IRNAS/smartparks-lion-tracker-hardware/LION/04_OUTPUT_FILES/Lion_9.png

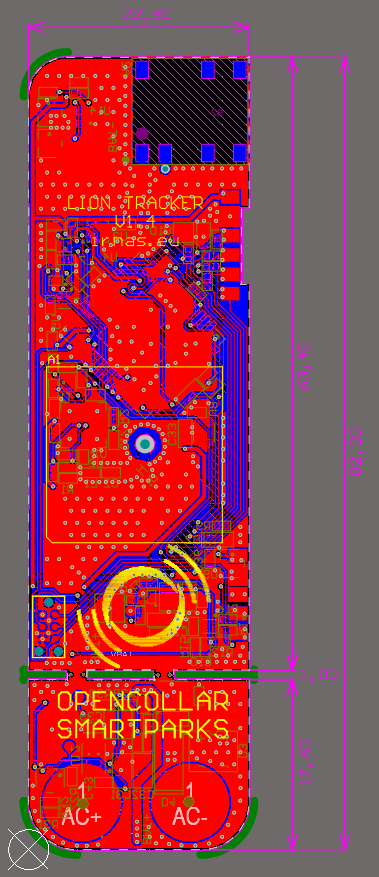
LION/04_OUTPUT_FILES/Lion_9.png
