IRNAS/smartparks-lion-tracker-hardware/Fence_monitor/06_RELEASE/V1/Fence monitor_V1_3D/Fence monitor_V1_PCB_3D_PRINT.pdf

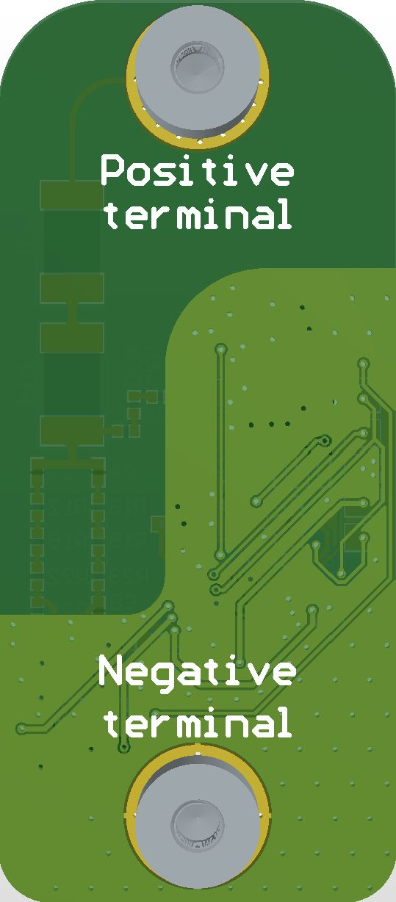
[picture p21: figure]

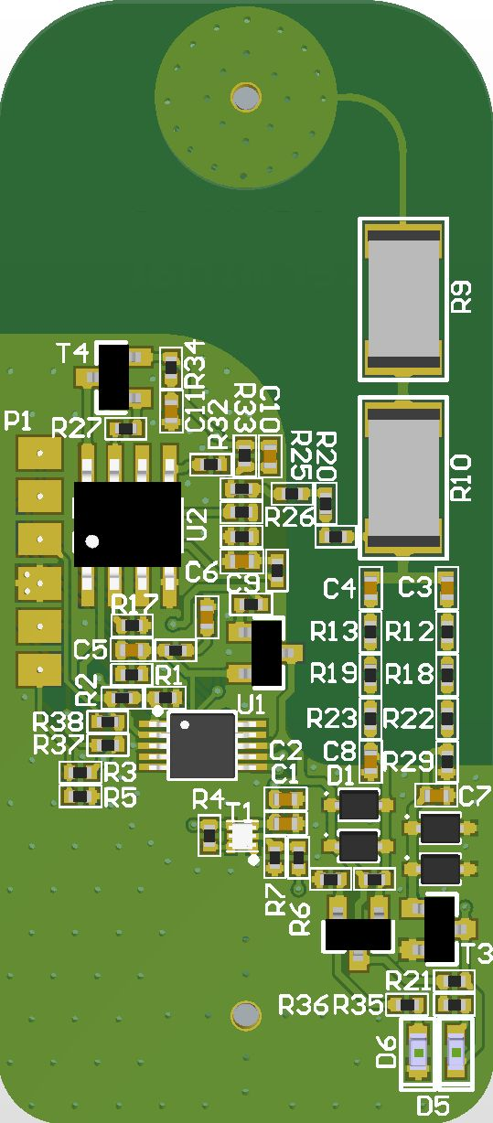
[picture p22: figure]
