IRNAS/smartparks-lion-tracker-hardware/LION/06_RELEASE/V1.4/Lion_Tracker_V1.4_3D/Lion_Tracker_V1.4_PCB 3D Print.pdf

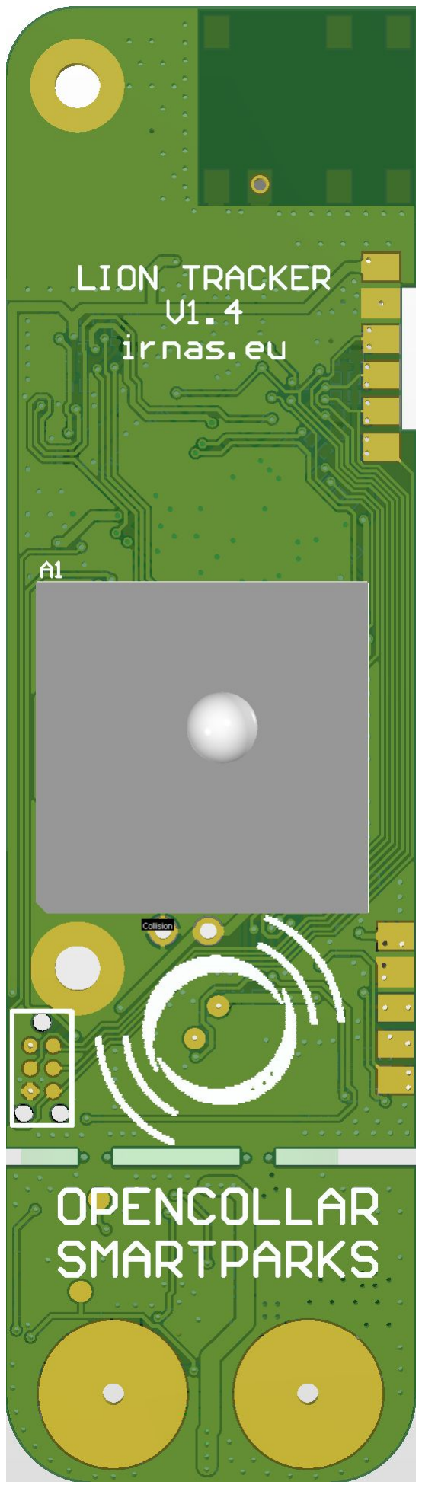
[picture p23: figure]

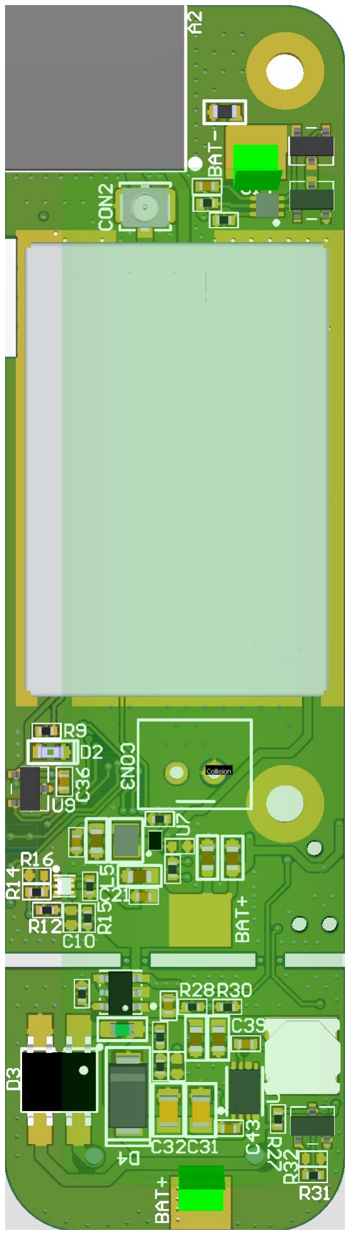
[picture p24: figure]
