IRNAS/smartparks-lion-tracker-hardware/LION/06_RELEASE/V0/Lion tracker_V0_3D/Lion tracker_V0_PCB 3D Print.pdf

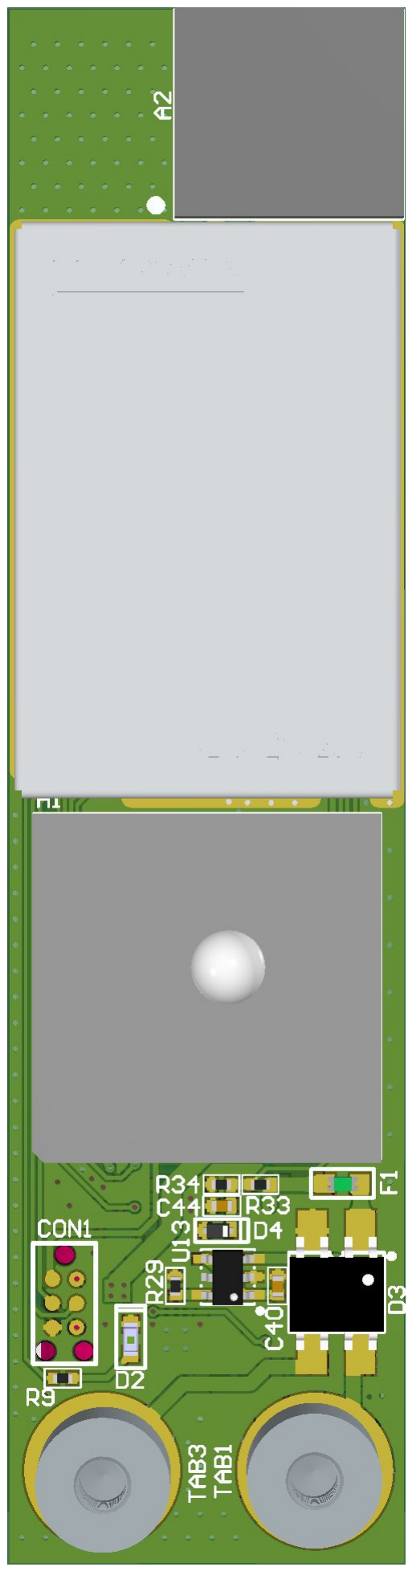
[picture p25: figure]

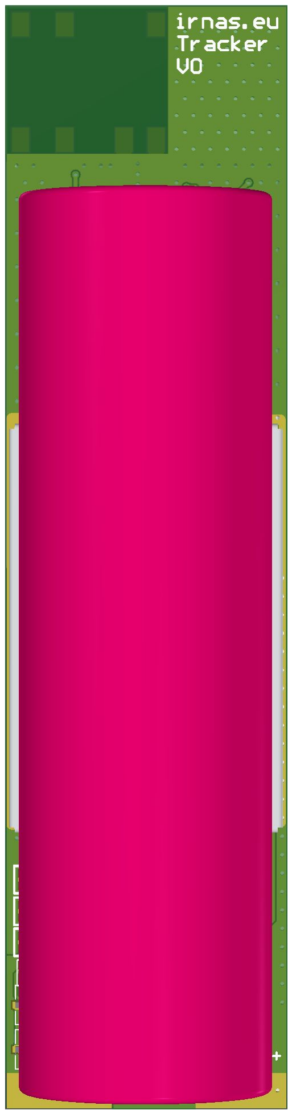
[picture p26: figure]
