IRNAS/smartparks-lion-tracker-hardware/LION/06_RELEASE/V1.1/Lion_Tracker_V1.1_3D/Lion_Tracker_V1.1_PCB 3D Print.pdf

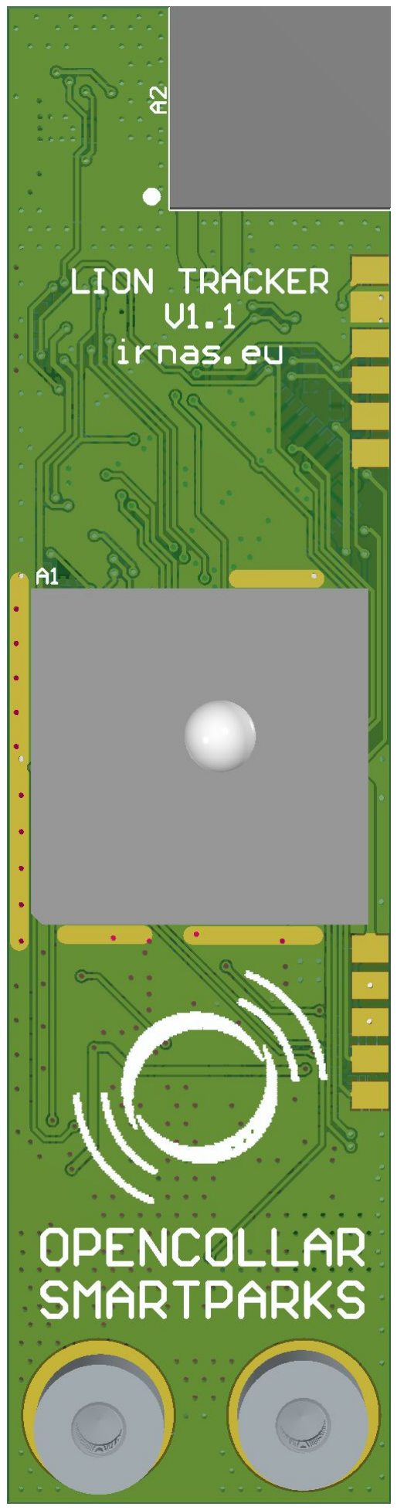
[picture p27: figure]

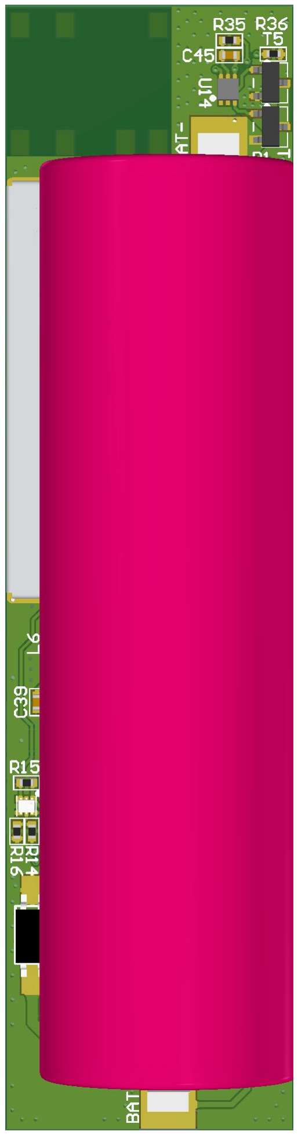
[picture p28: figure]
