IRNAS/smartparks-lion-tracker-hardware/LION/06_RELEASE/V1.2/Lion_Tracker_V1.2_3D/Lion_Tracker_V1.2_PCB 3D Print.pdf

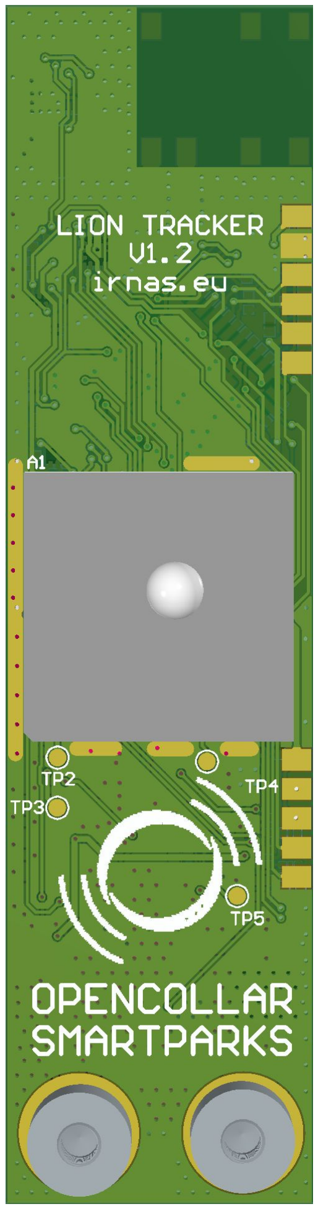
[picture p29: figure]

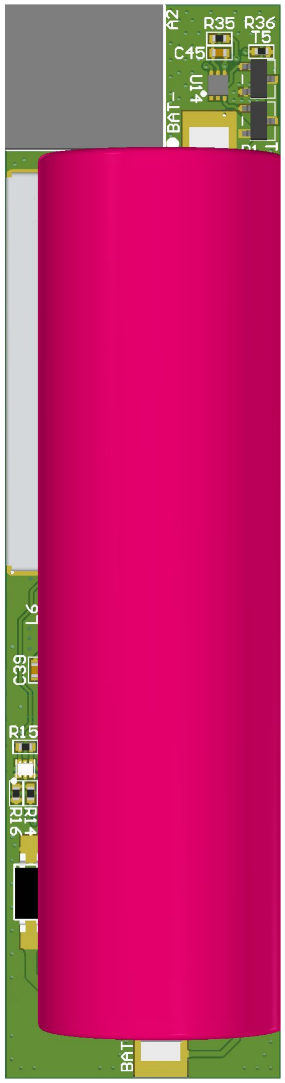
[picture p30: figure]
