IRNAS/smartparks-lion-tracker-hardware/LION/06_RELEASE/V1.3/Lion_Tracker_V1.3_3D/Lion_Tracker_V1.3_PCB 3D Print.pdf

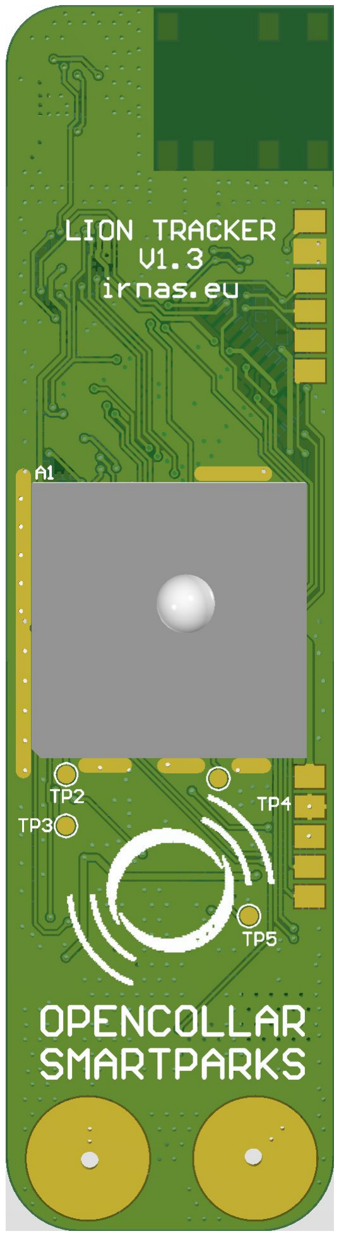
[picture p31: figure]

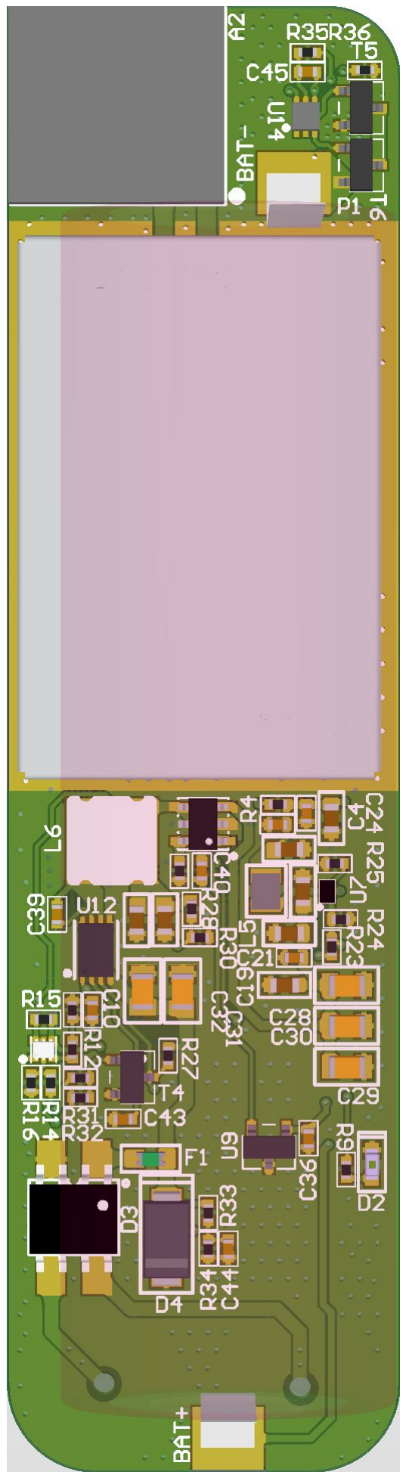
[picture p32: figure]
