IRNAS/smartparks-lion-tracker-hardware/LION/06_RELEASE/V1.4/Lion_Tracker_V1.4_SCHEMATICS/Lion_Tracker_V1.4_SCHEMATICS.PDF

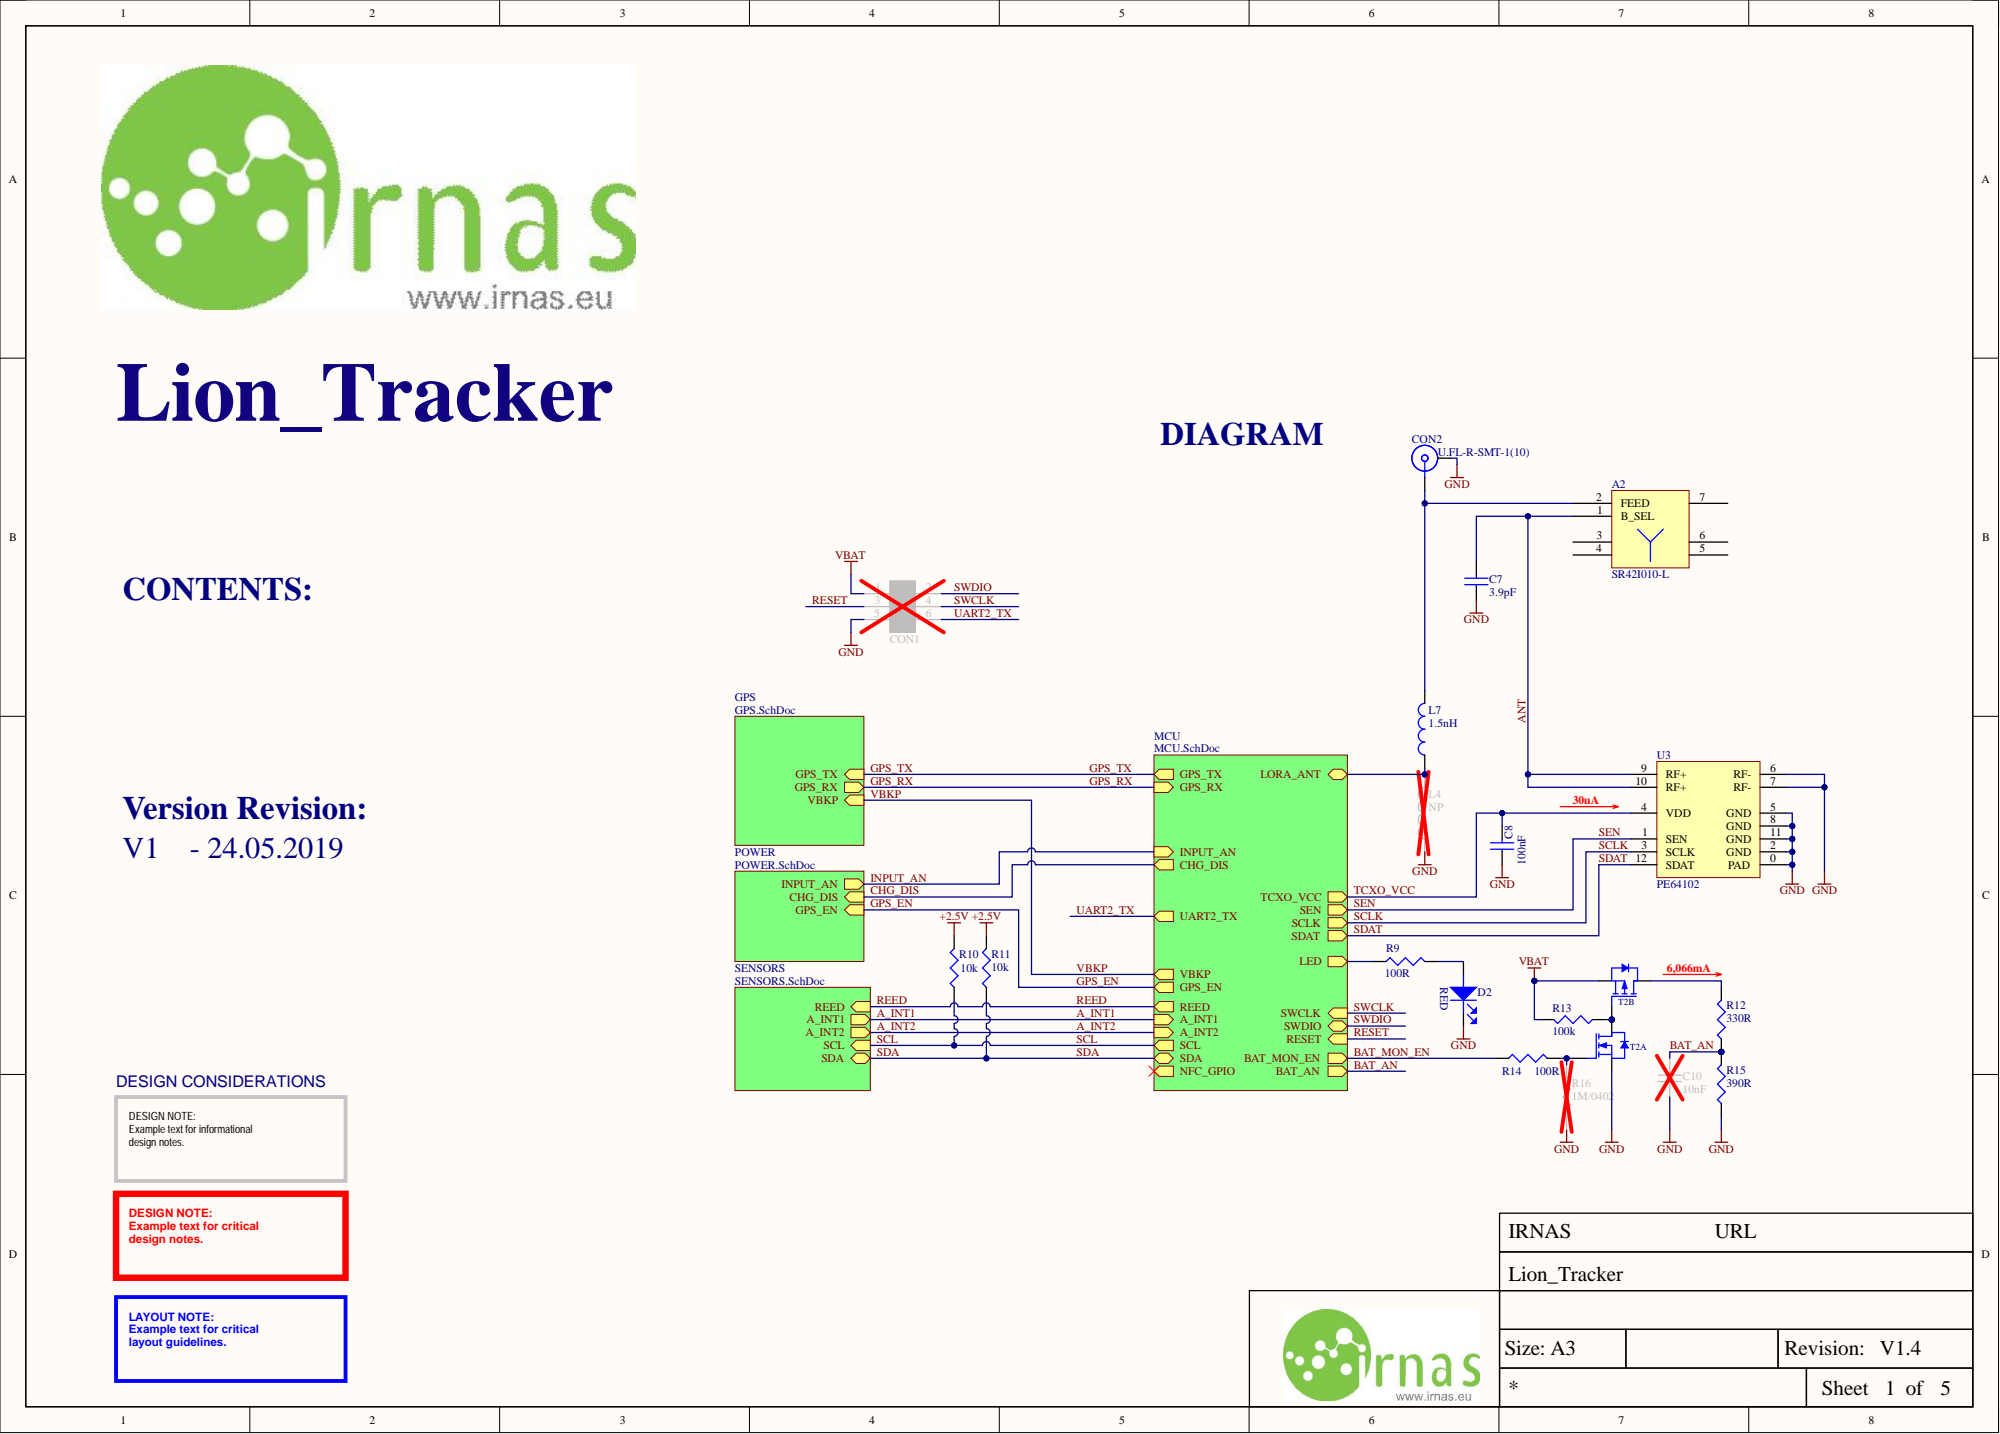
[picture p64: page 1]

B_SEL 1 FEED 2

SCLK
SDAT

GPS_EN | SEN

+2.5V +2.5V R10 R11 10k 10k VBKP | SCLK

REED A_INT1 A_INT2 SCL SDA | REED | REED

A_INT1 | A_INT1

SCL | SCL
SDA | SDA

DESIGN NOTE:
Example text for informational
design notes.

Example text for critical

LAYOUT NOTE:
layout guidelines.

Size: A3 | | Revision: V1.4

Sheet of

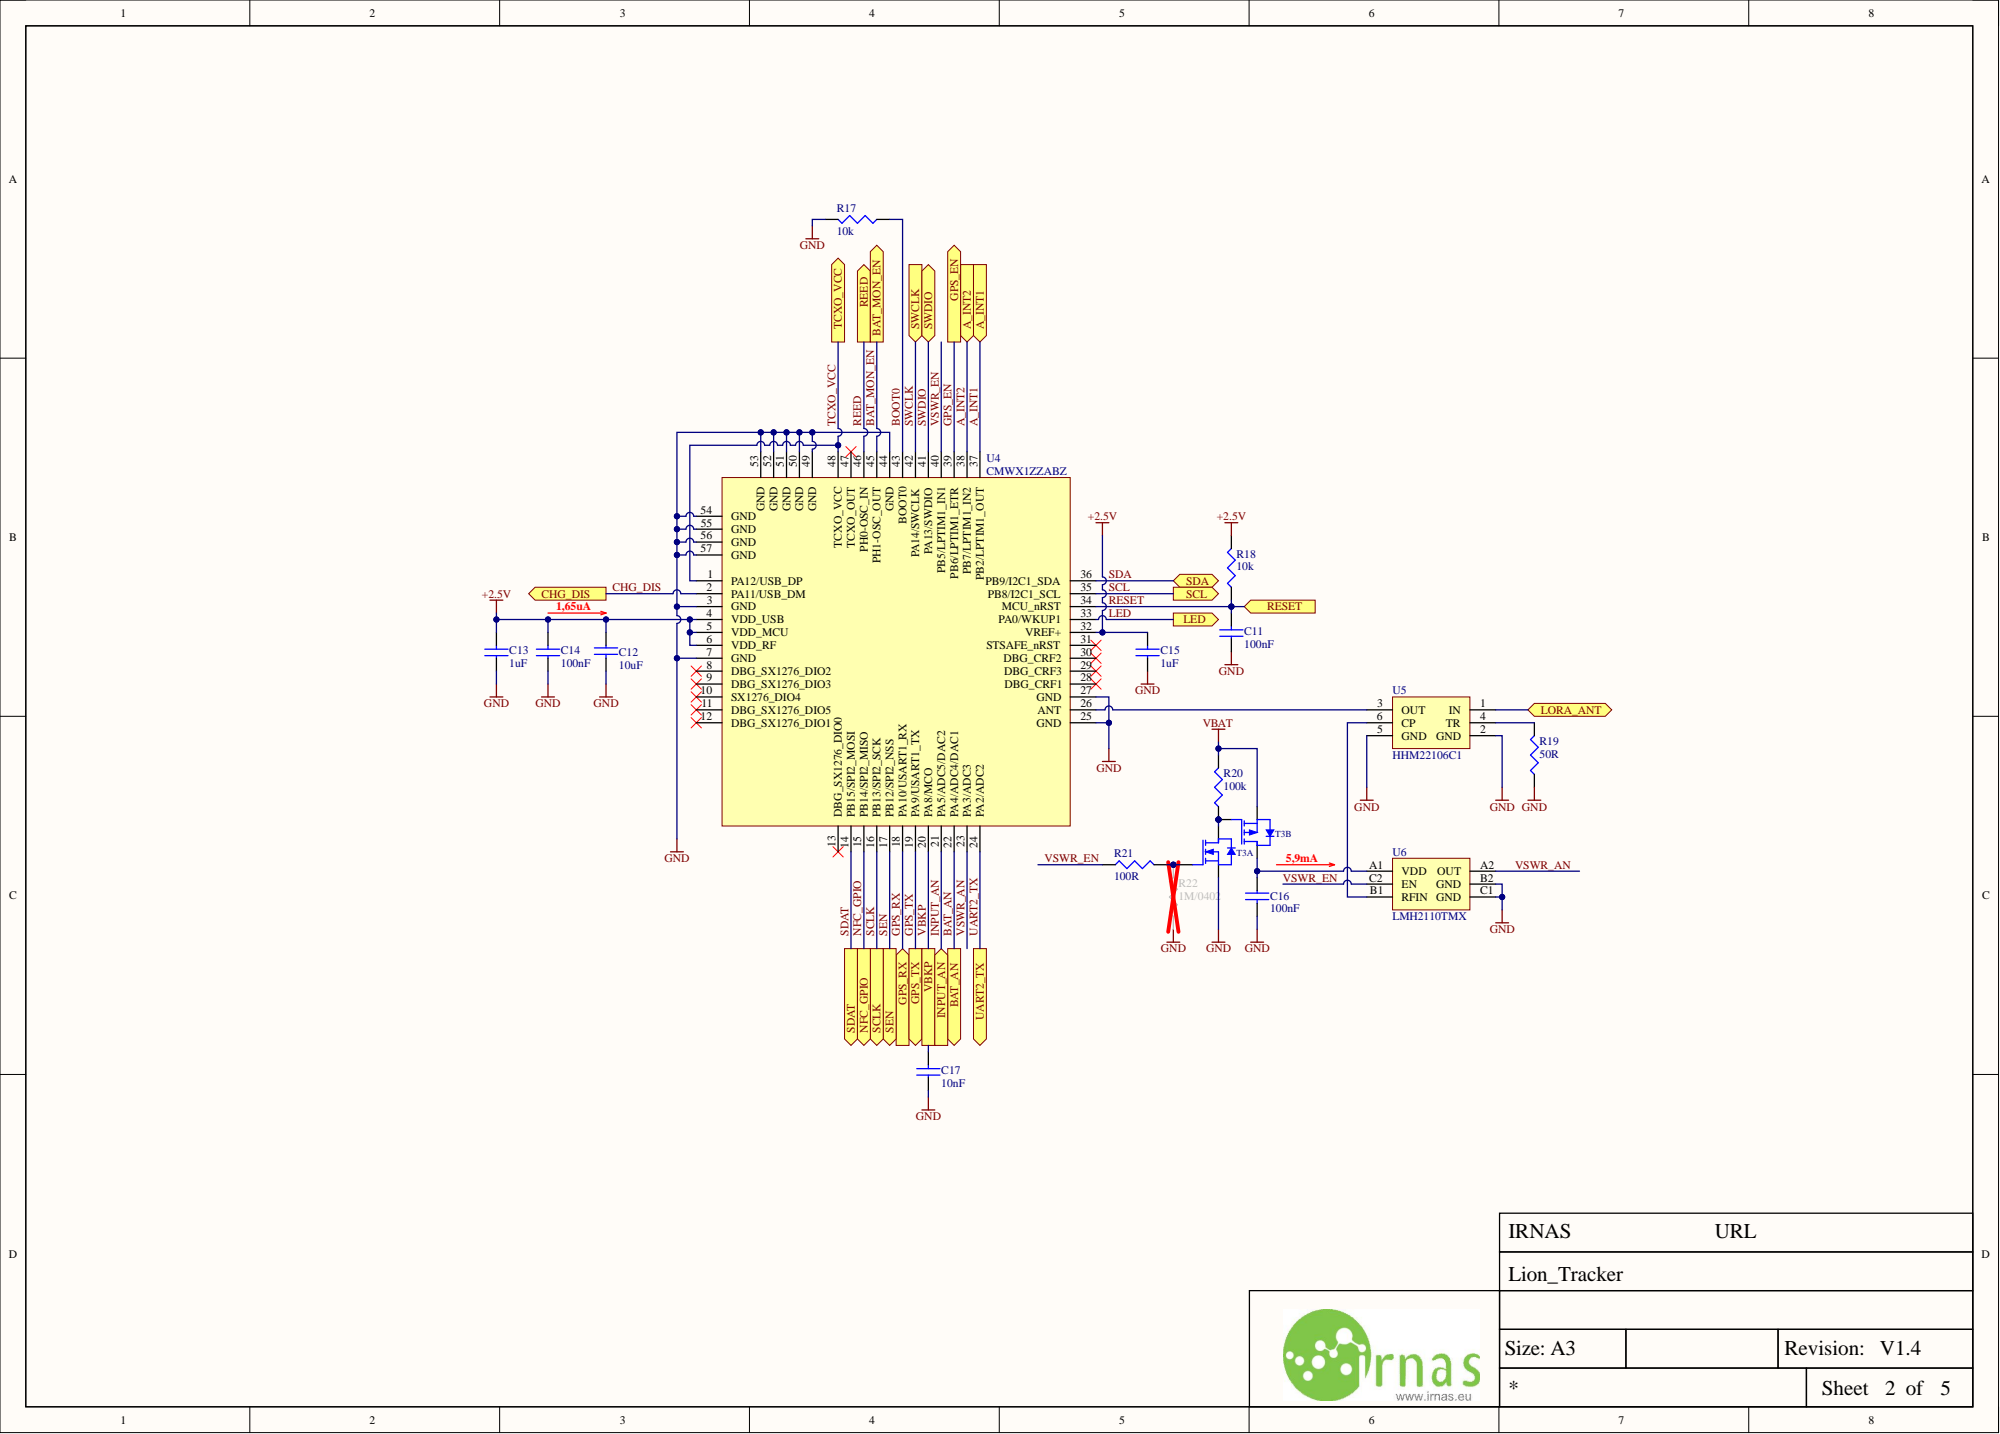
[picture p65: page 2]

GND 50 GND 51 GND 52 GND 53

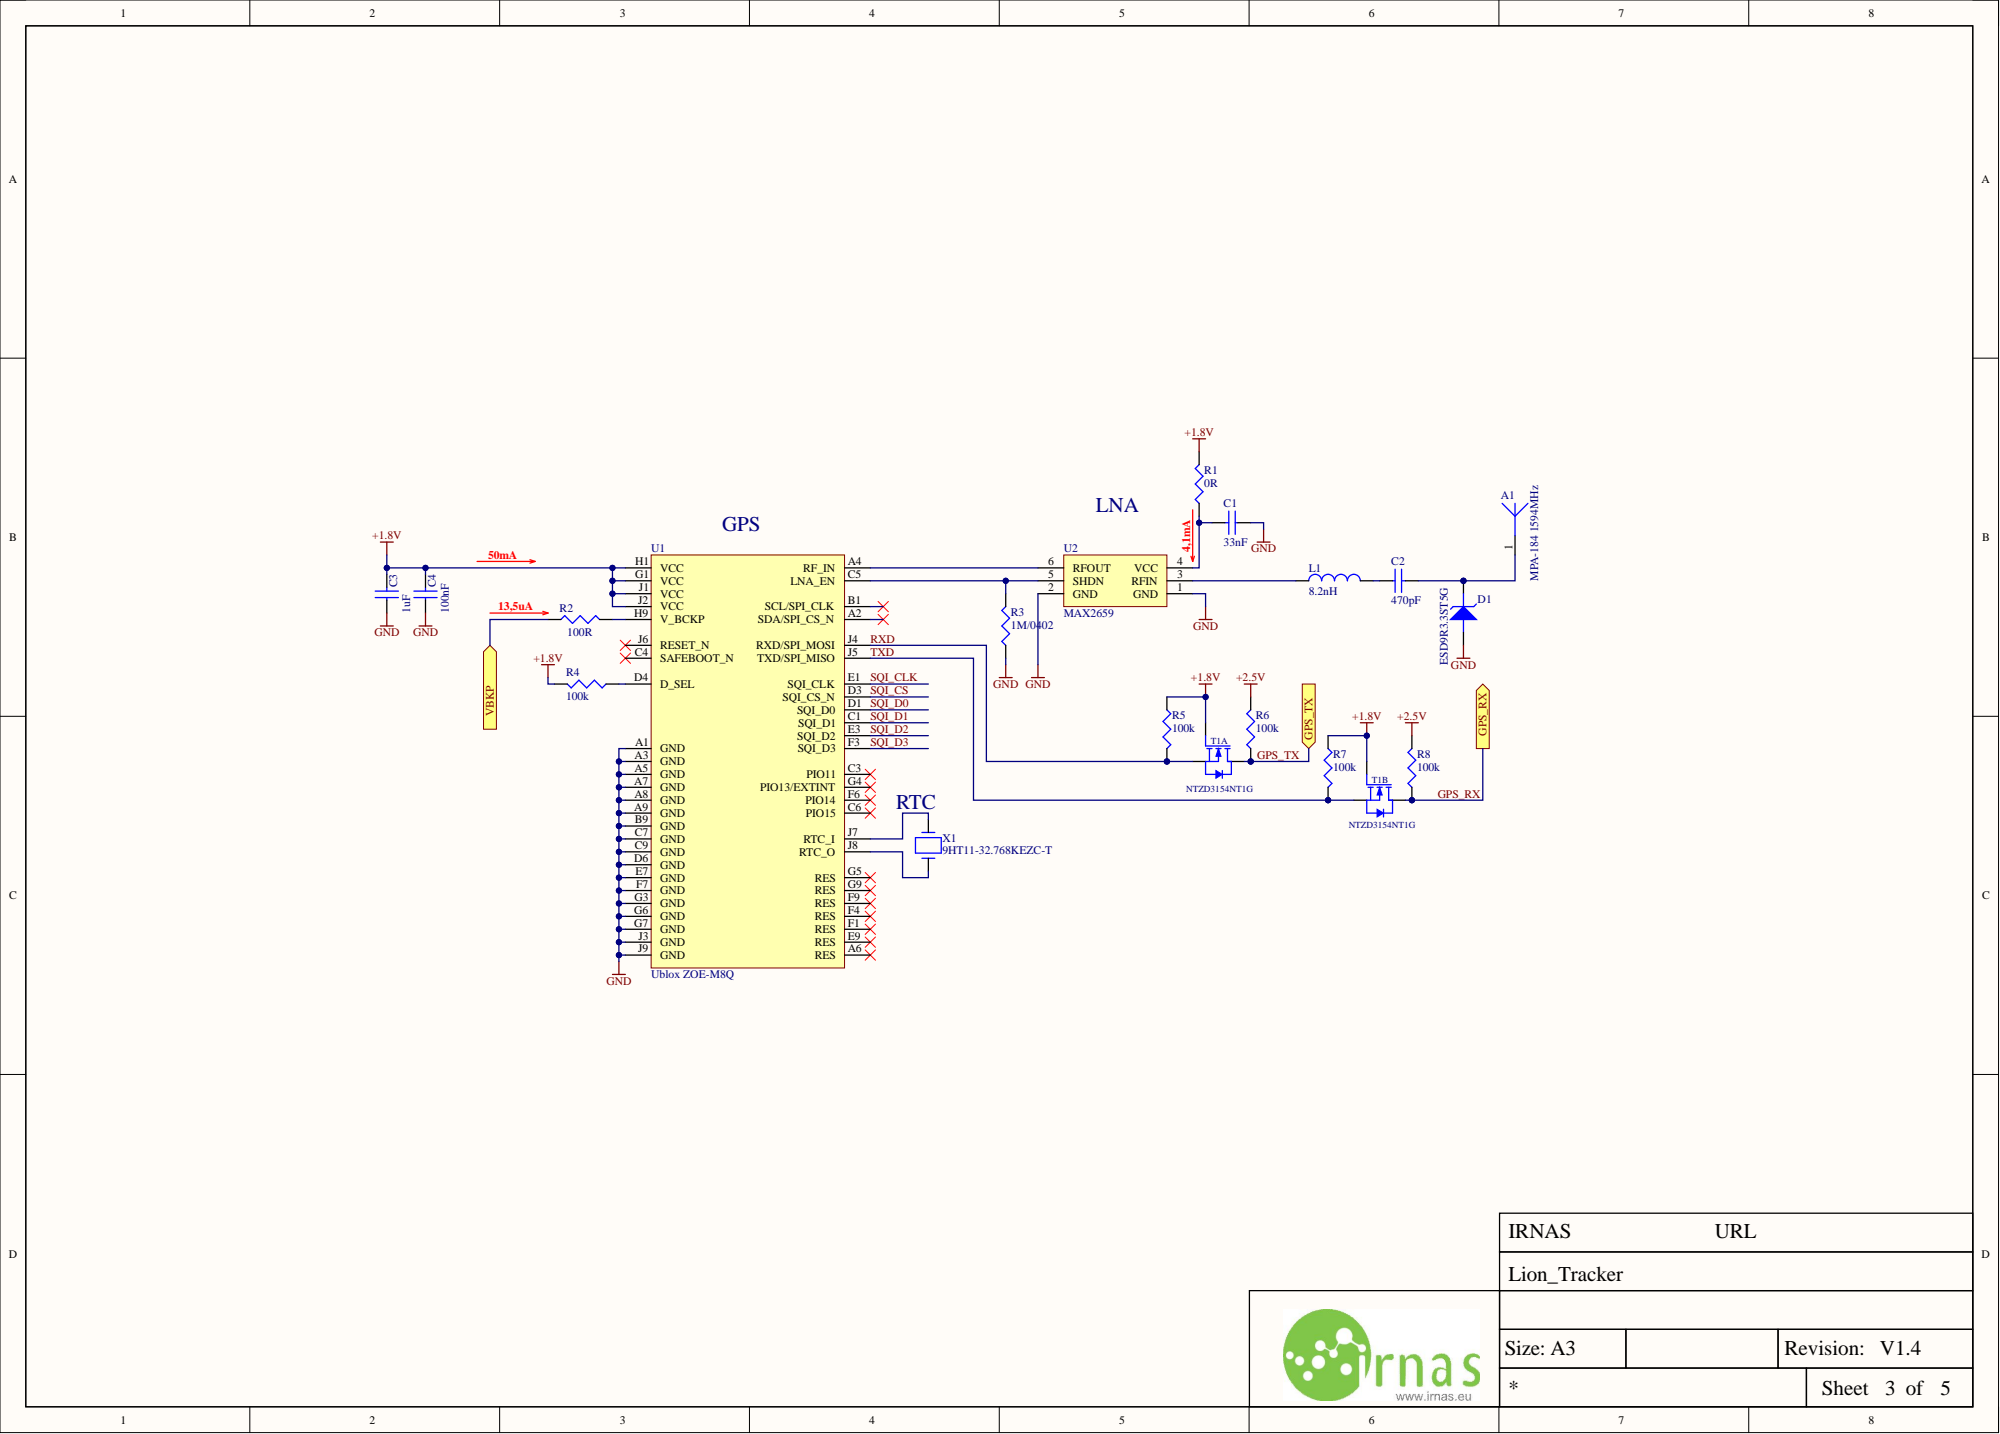
[picture p66: page 3]

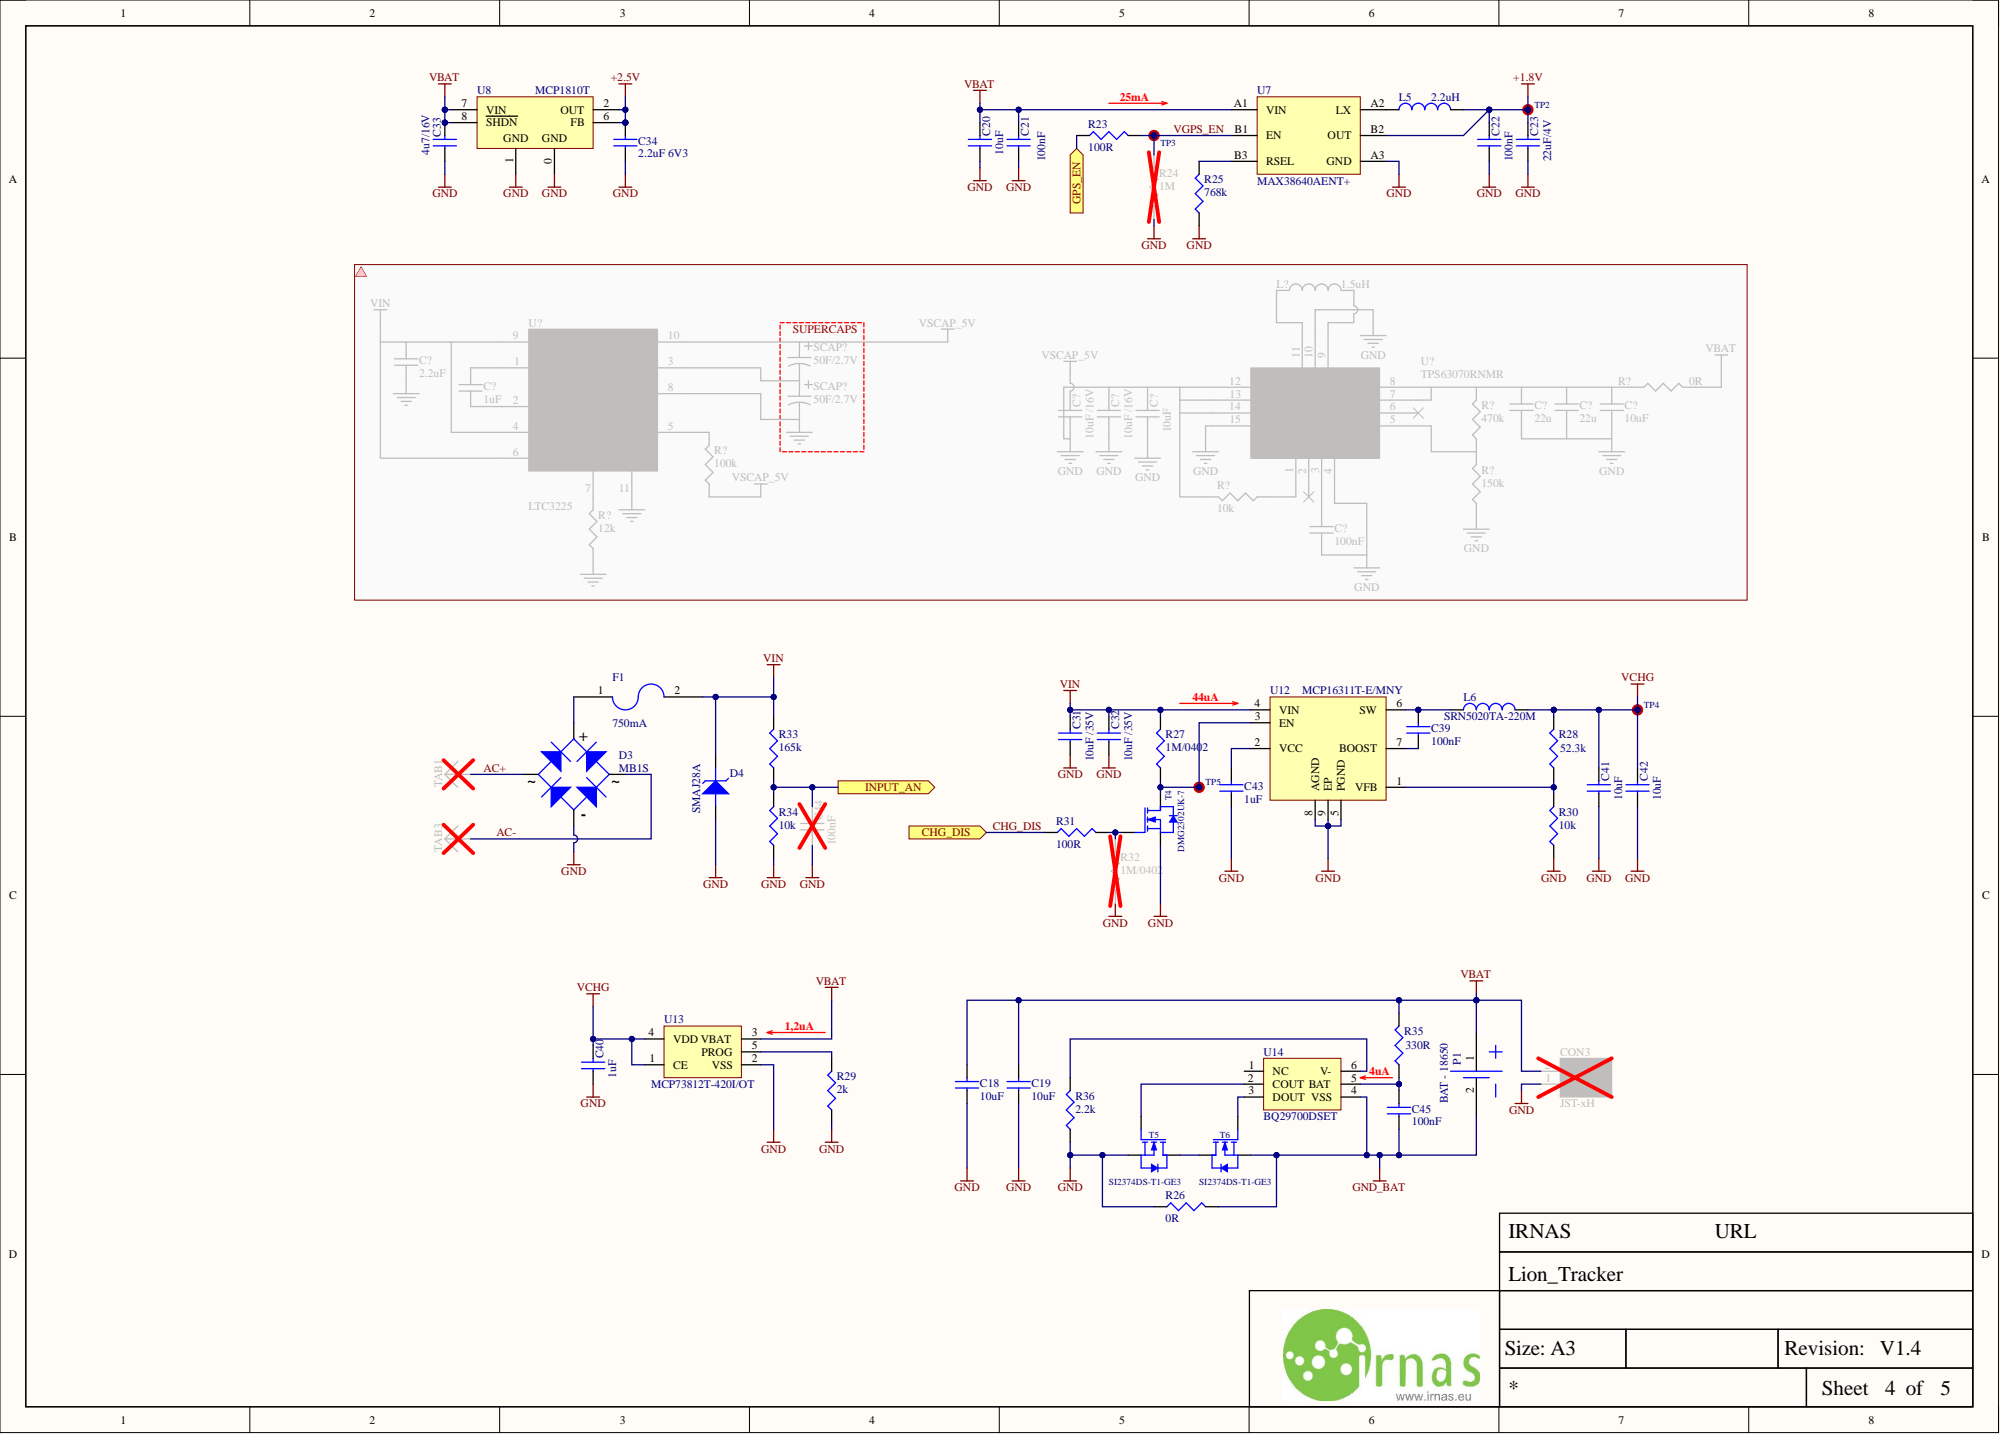
[picture p67: page 4]

VIN 13

VSEL 15

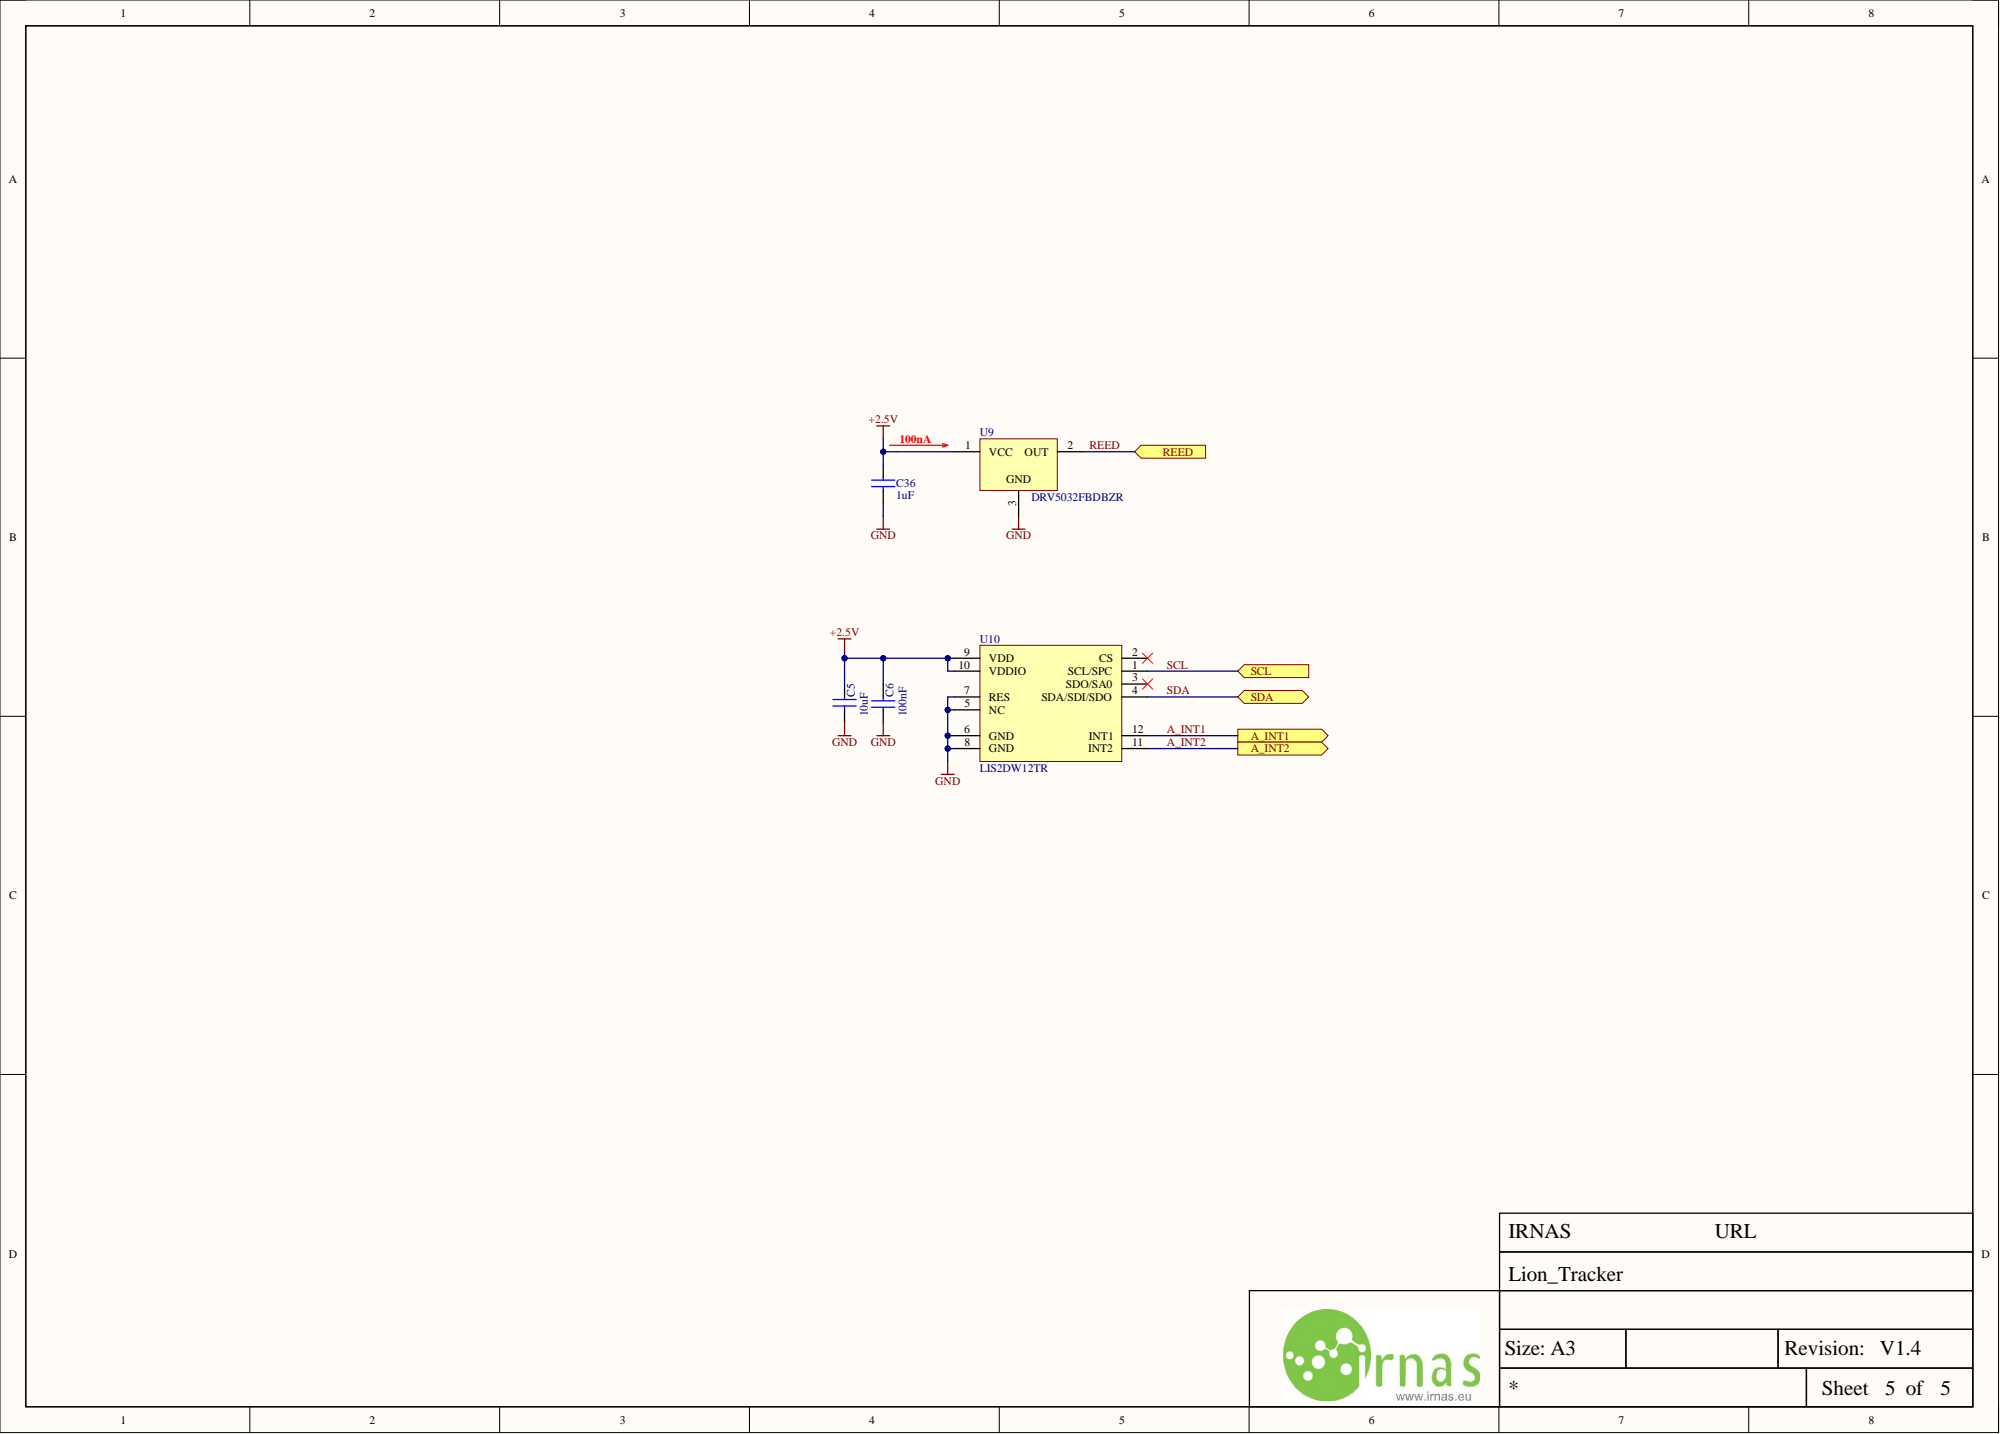
[picture p68: page 5]
