IRNAS/smartparks-lion-tracker-hardware/LION/06_RELEASE/V0/Lion tracker_V0_SCHEMATICS/Lion tracker_V0_SCHEMATICS.PDF

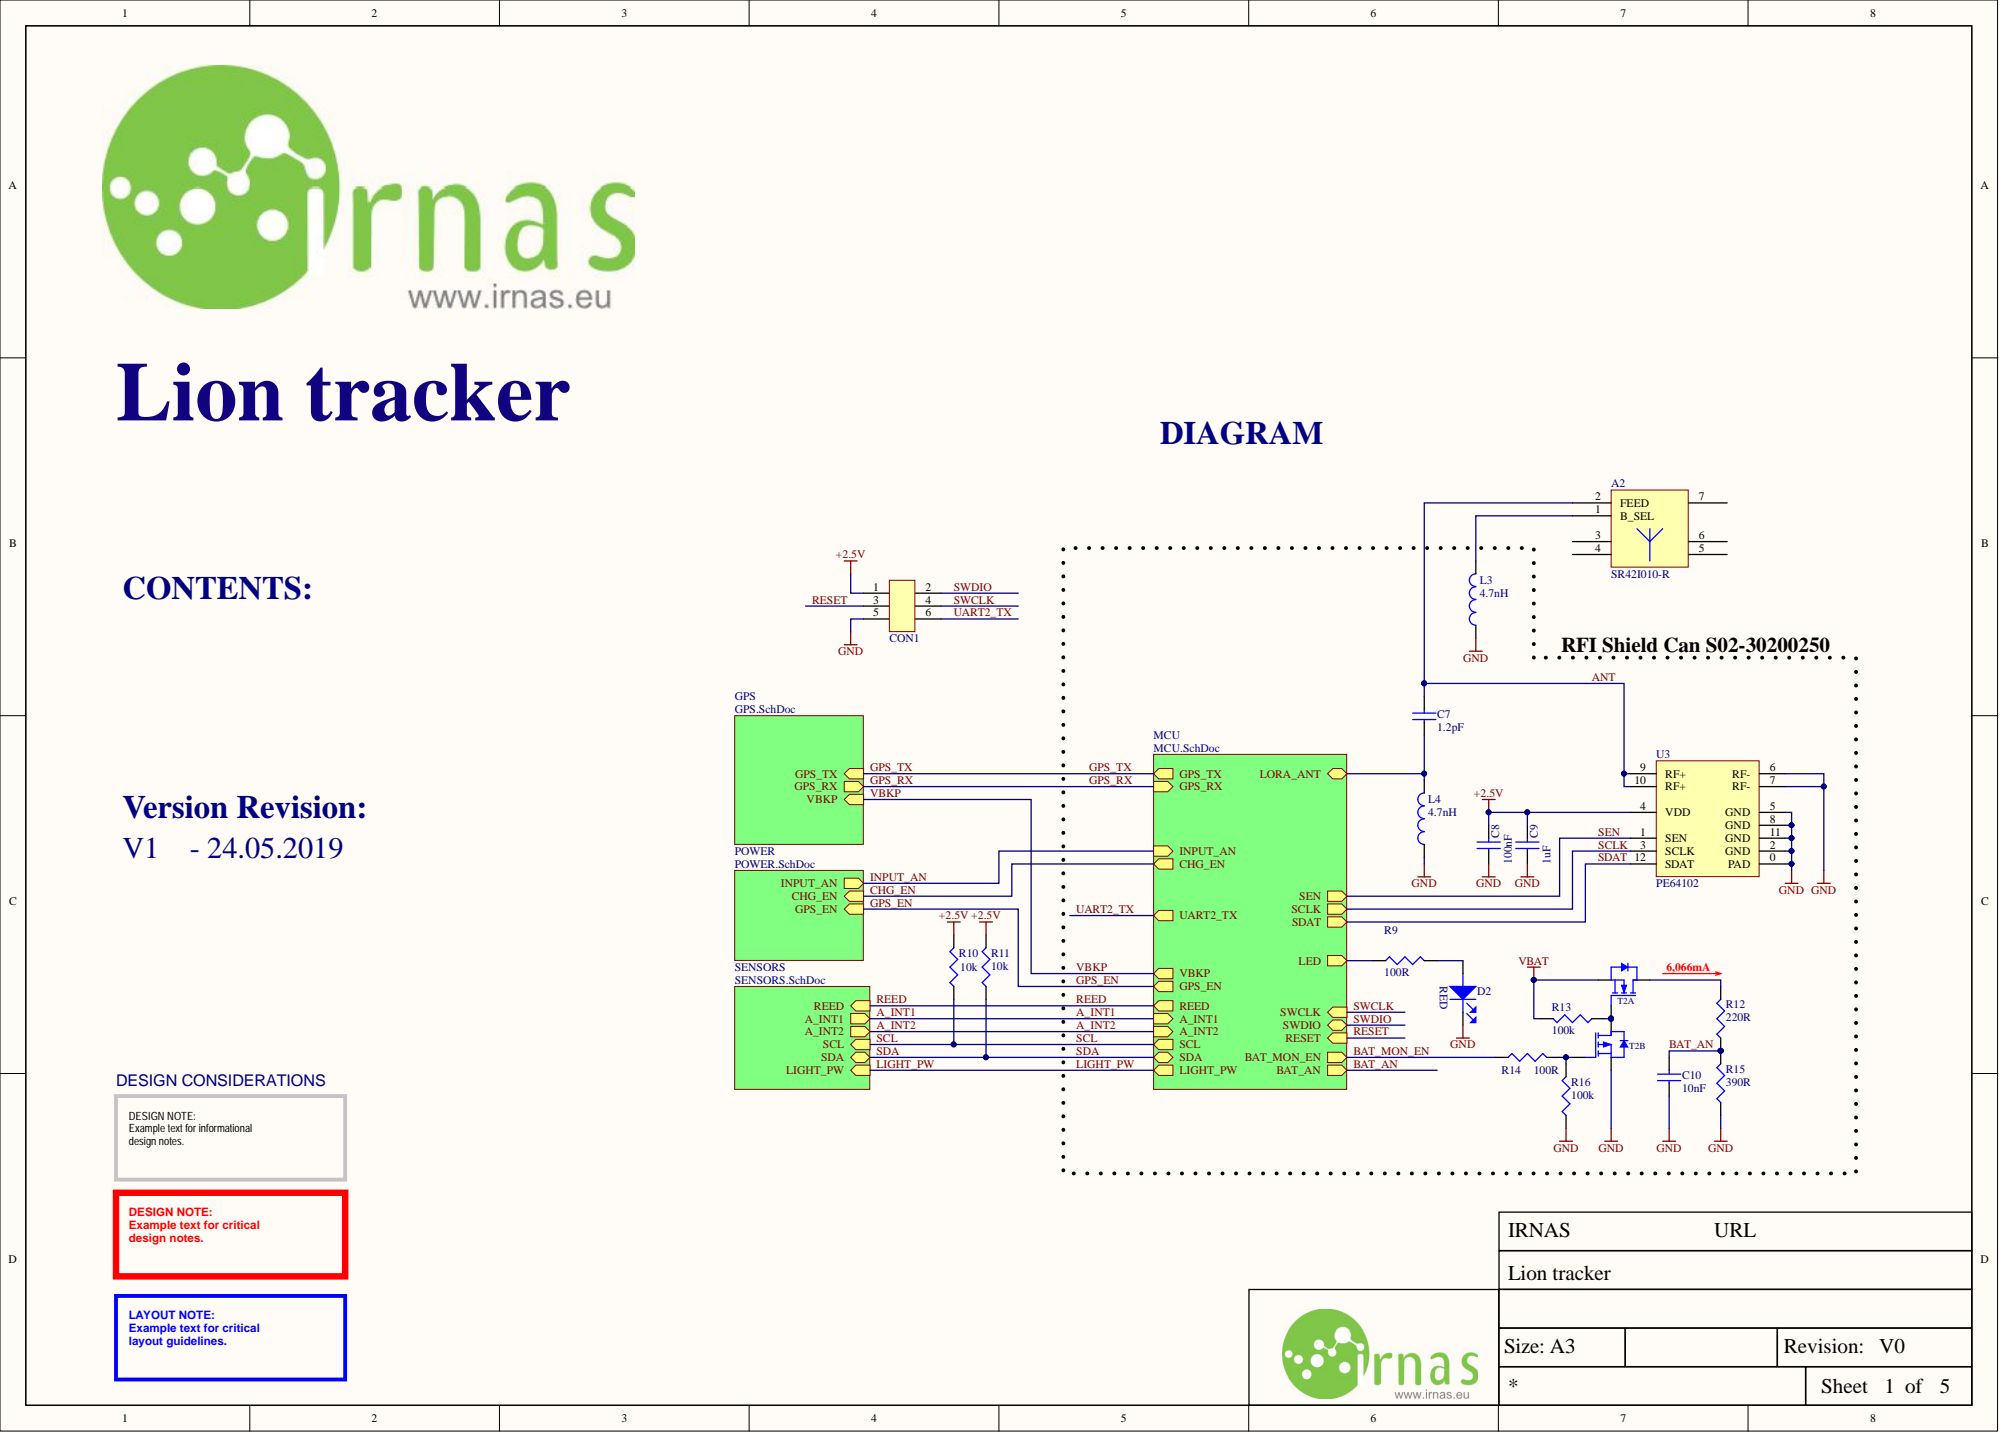
[picture p69: page 1]

SEN | | | 1 1

SDAT | | SDAT 12 | 0

INPUT_AN | | | | GND | GND
CHG_EN

+2.5V | +2.5V R10 10k | R1 1 10k | VBKP

UART2_TX

GPS_EN

REED A_INT1 A_INT2 SCL SDA LIGHT_PW | REED | | | REED

A_INT1 | | | A_INT1
A_INT2 | | | A_INT2
SCL | | | SCL
SDA | | | SDA

DESIGN NOTE:
Example text for informational
design notes.

Example text for critical

LAYOUT NOTE:
layout guidelines.

Size: A3 | | Revision: V0

Sheet of

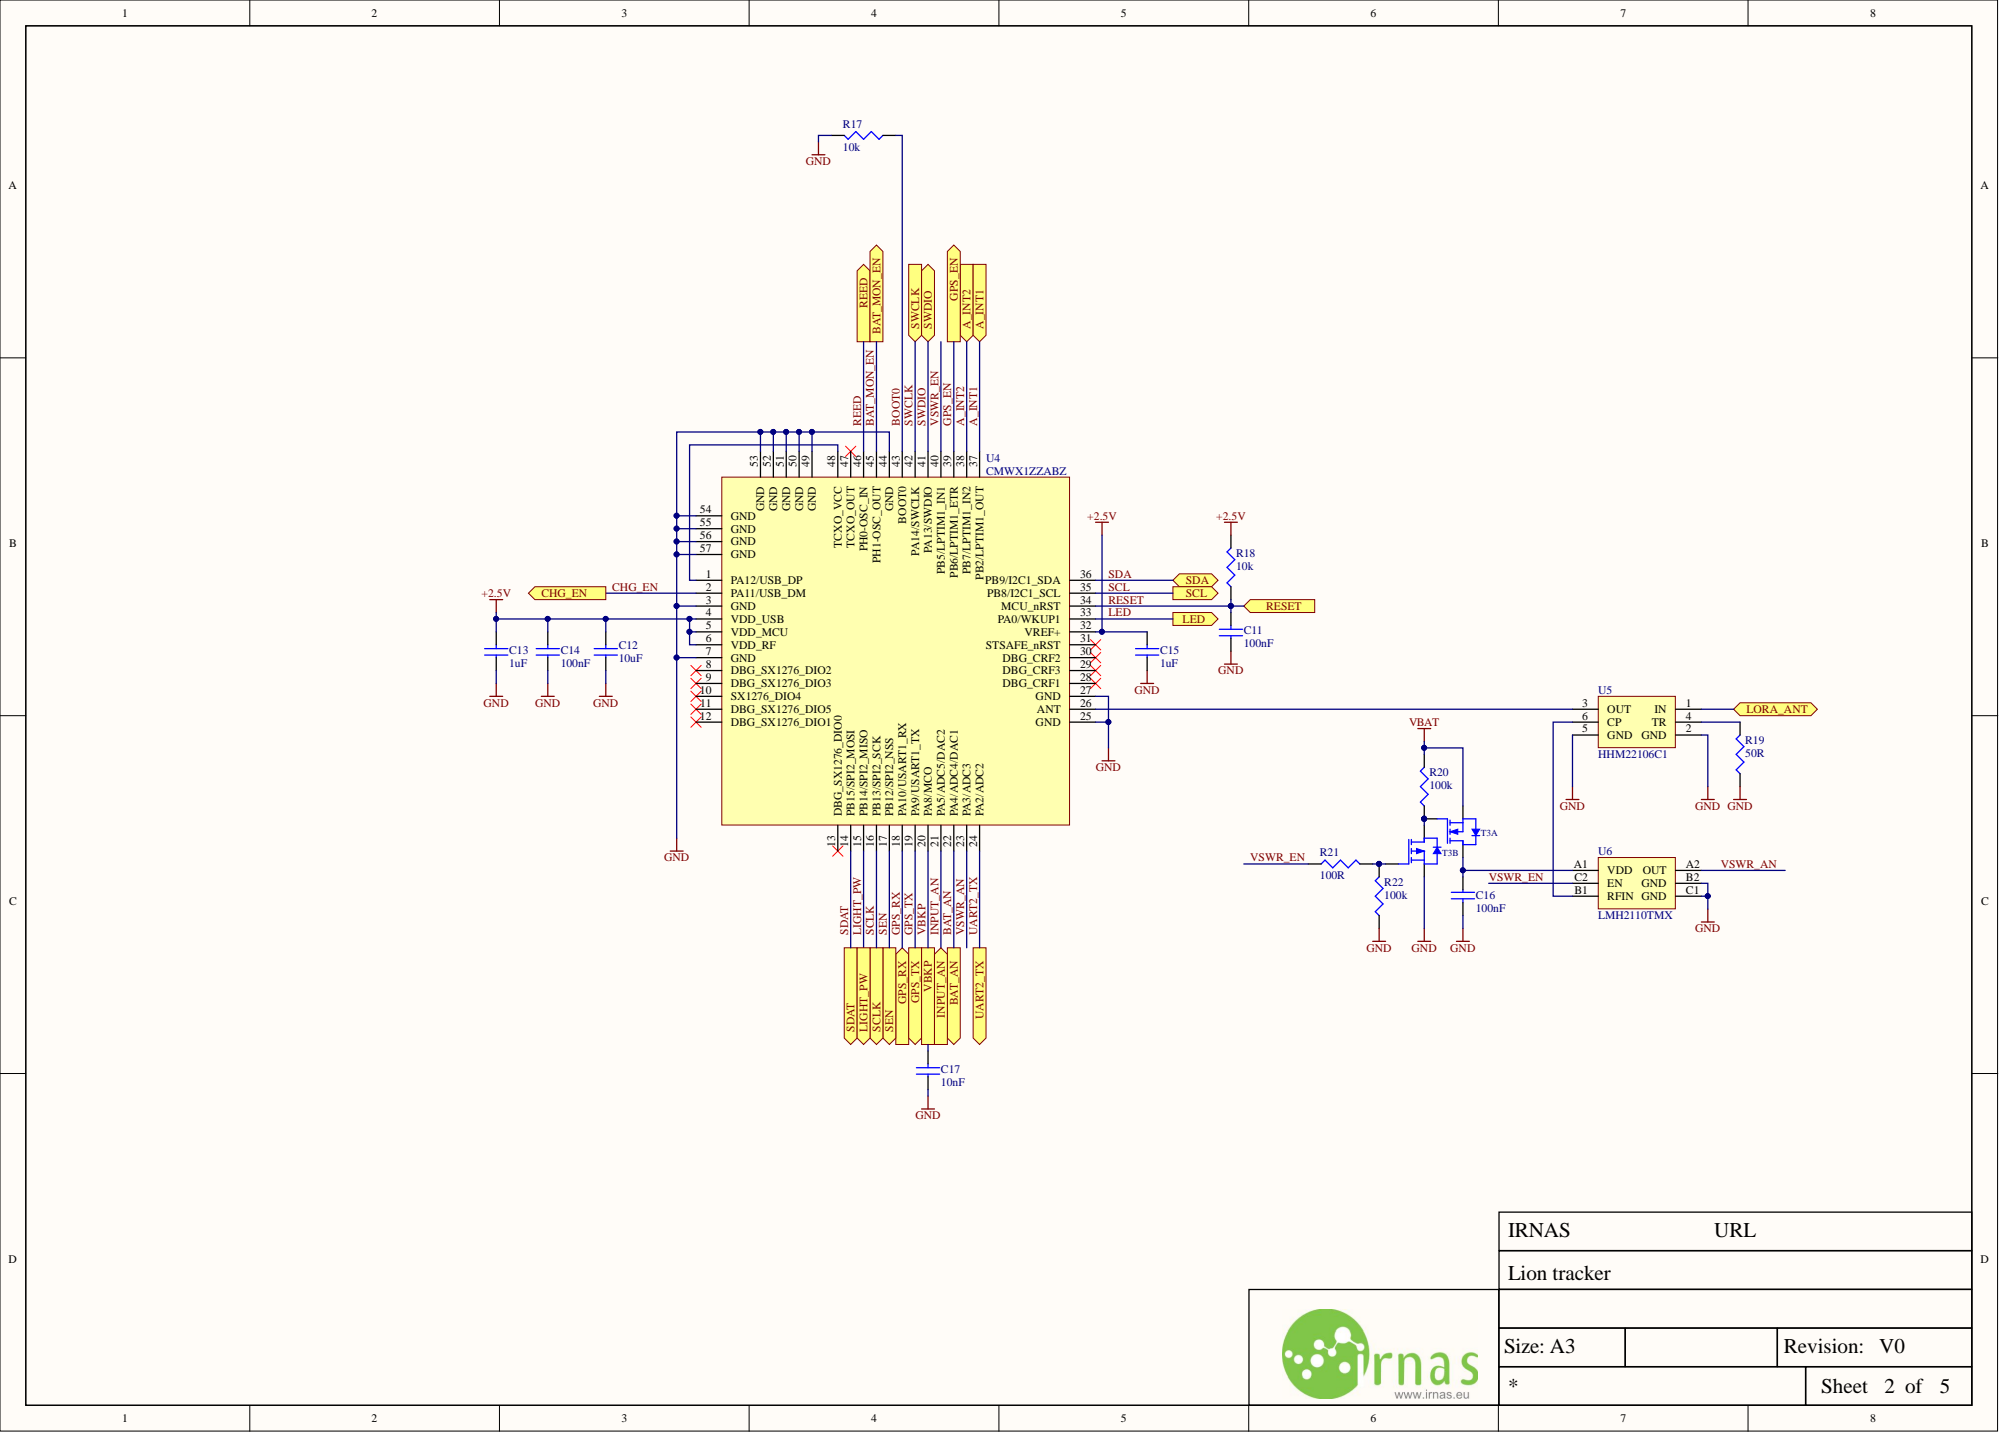
[picture p70: page 2]

GND 50 GND 51 GND 52 GND 53

GND 54 | PA0/WKUP1 | 33 MCU_nRST 34 PB8/I2C1_SCL 35 PB9/I2C1_SDA P
GND 55
GND 56

PA12/USB_DP 1

GND 3

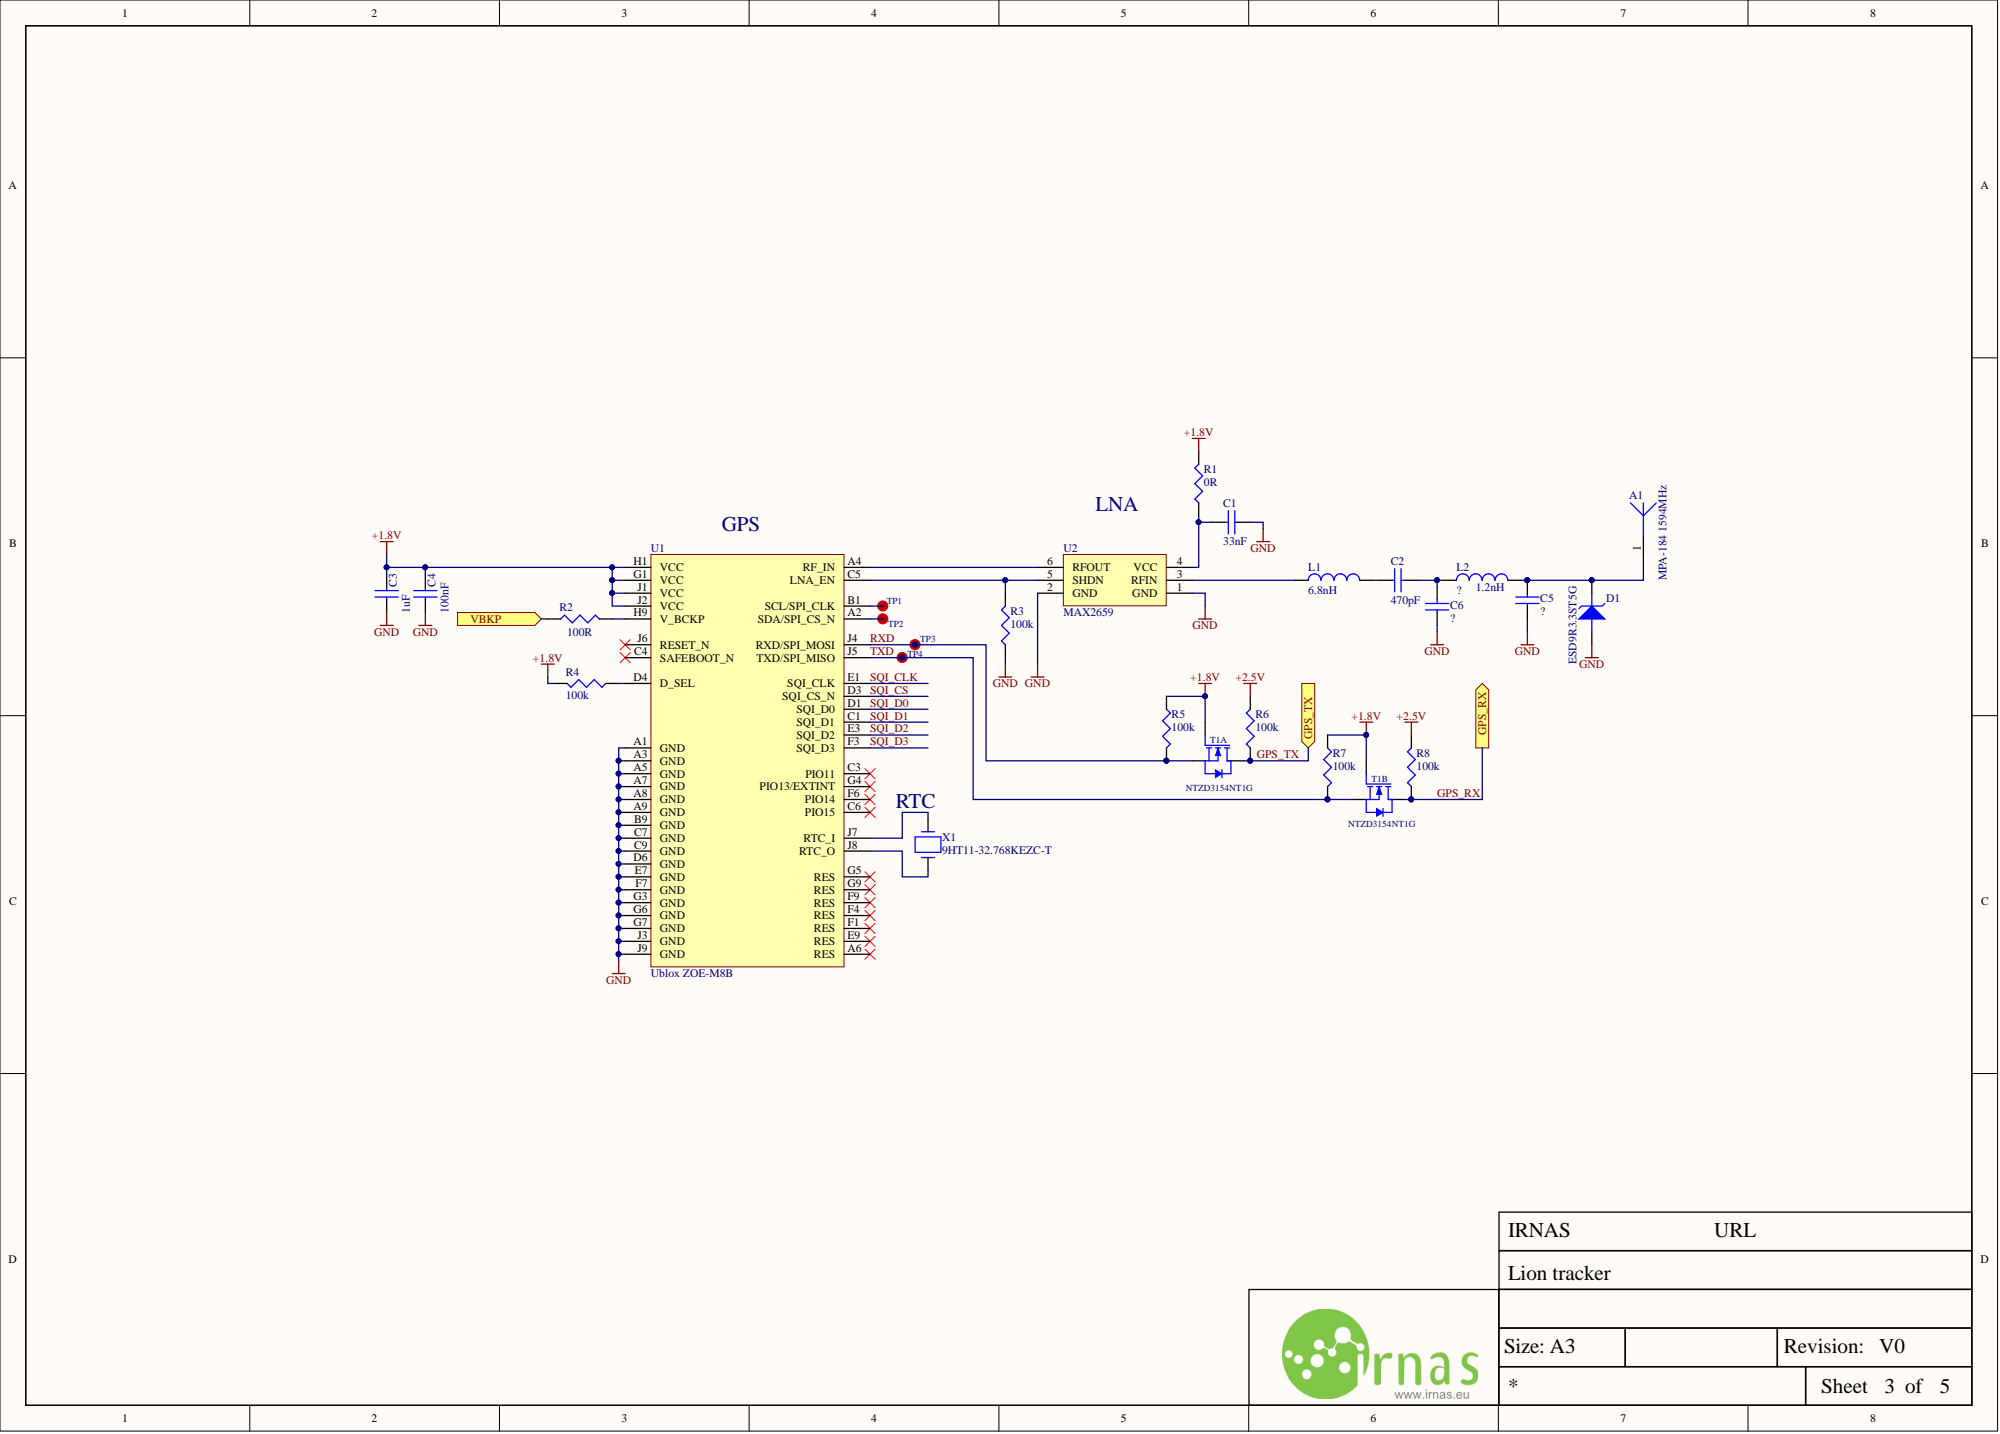
[picture p71: page 3]

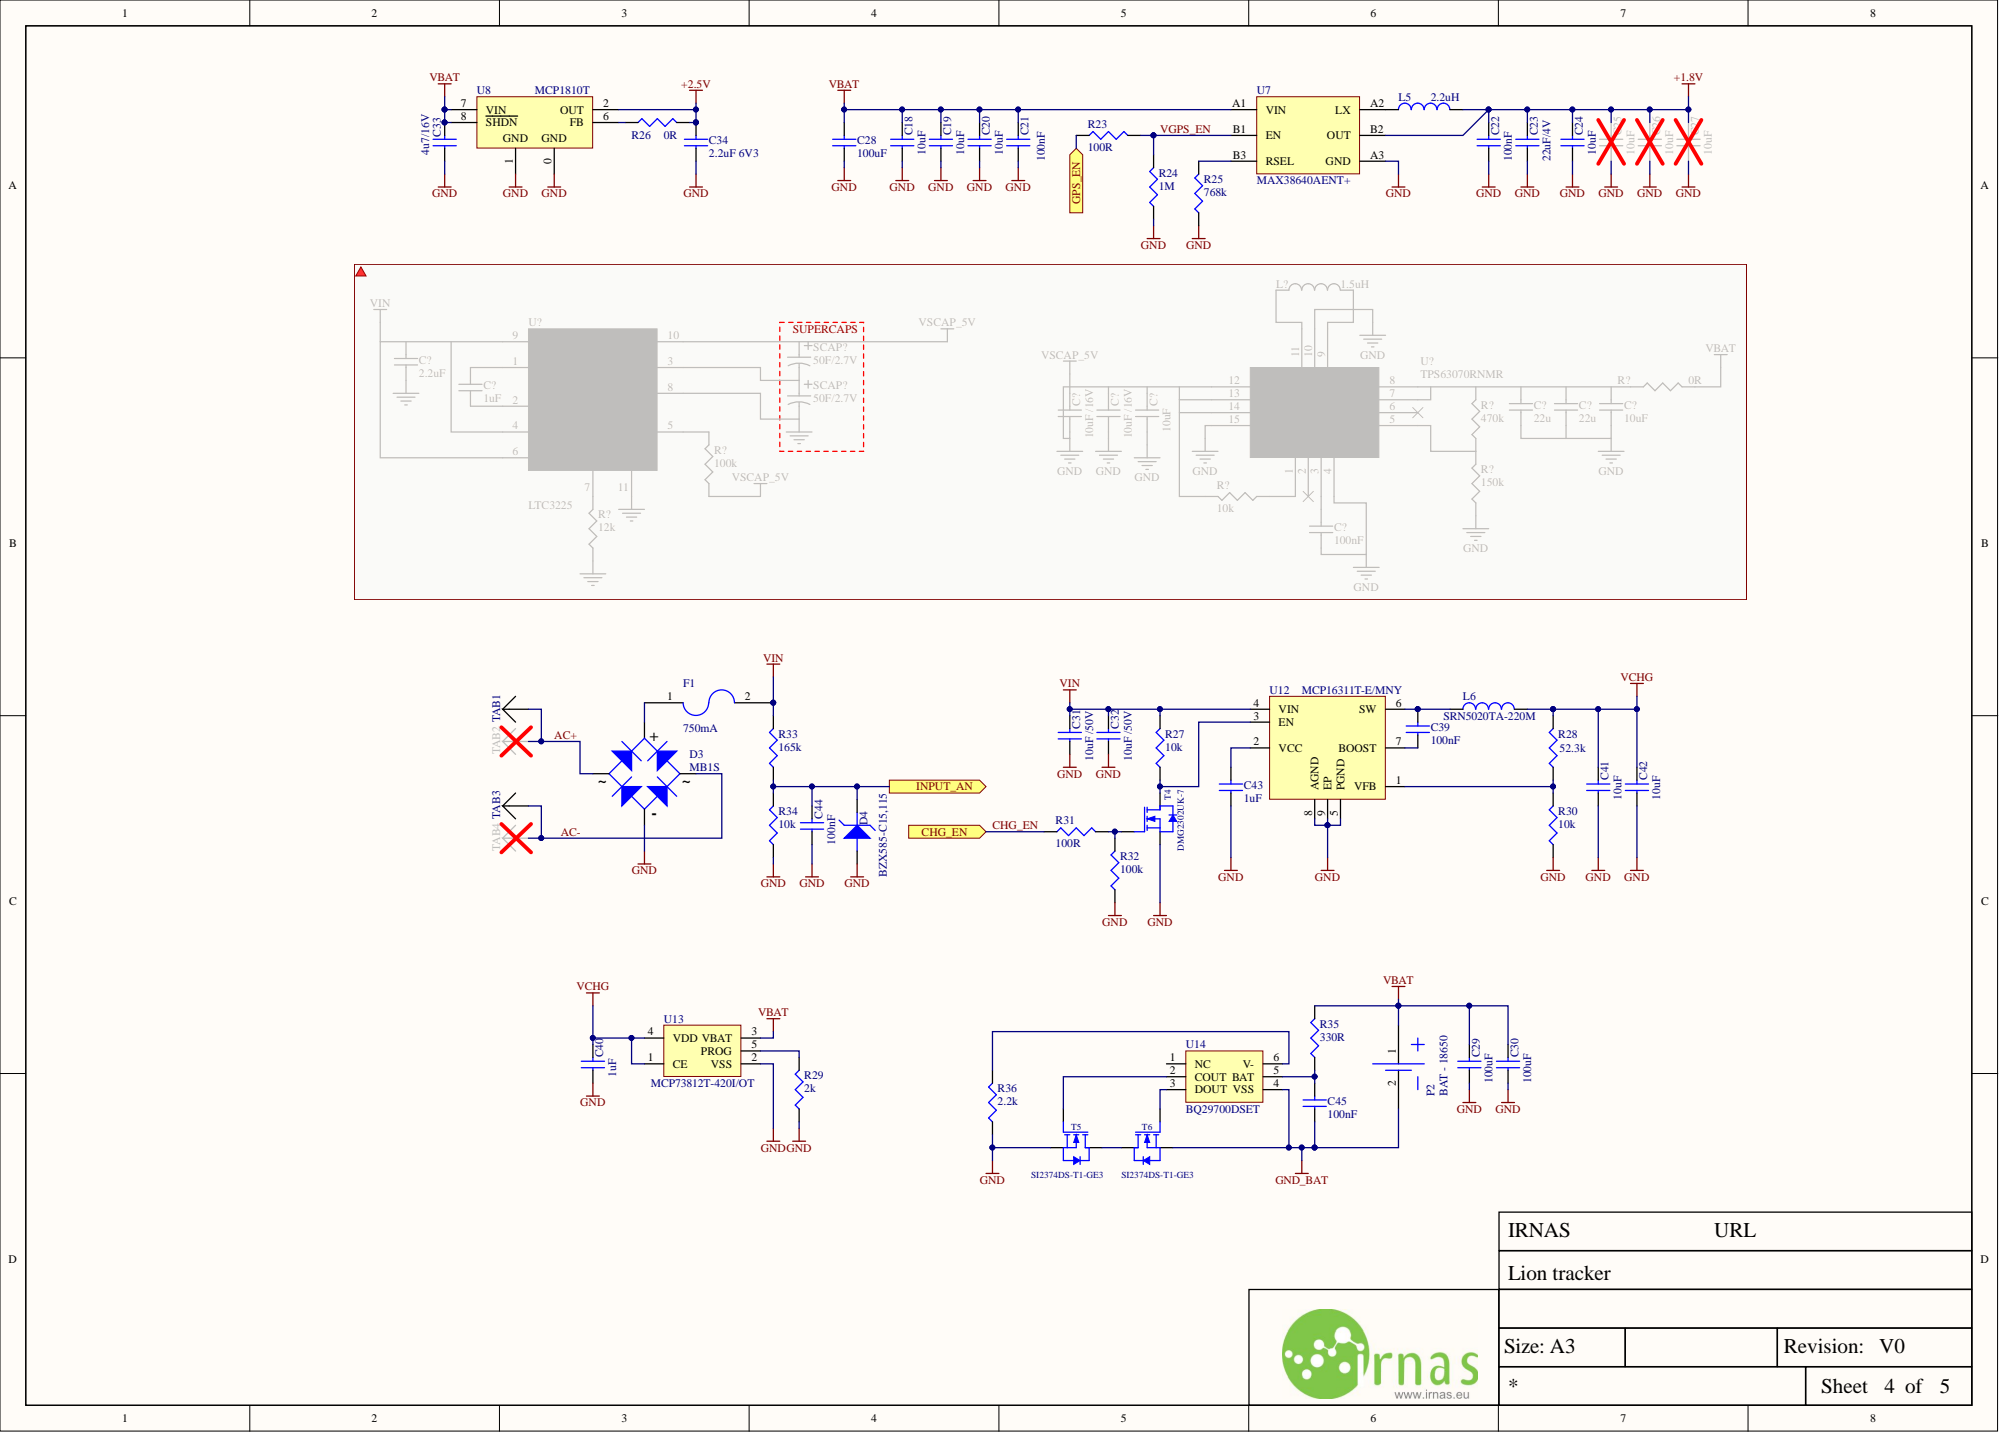
[picture p72: page 4]

VIN 13

VSEL 15

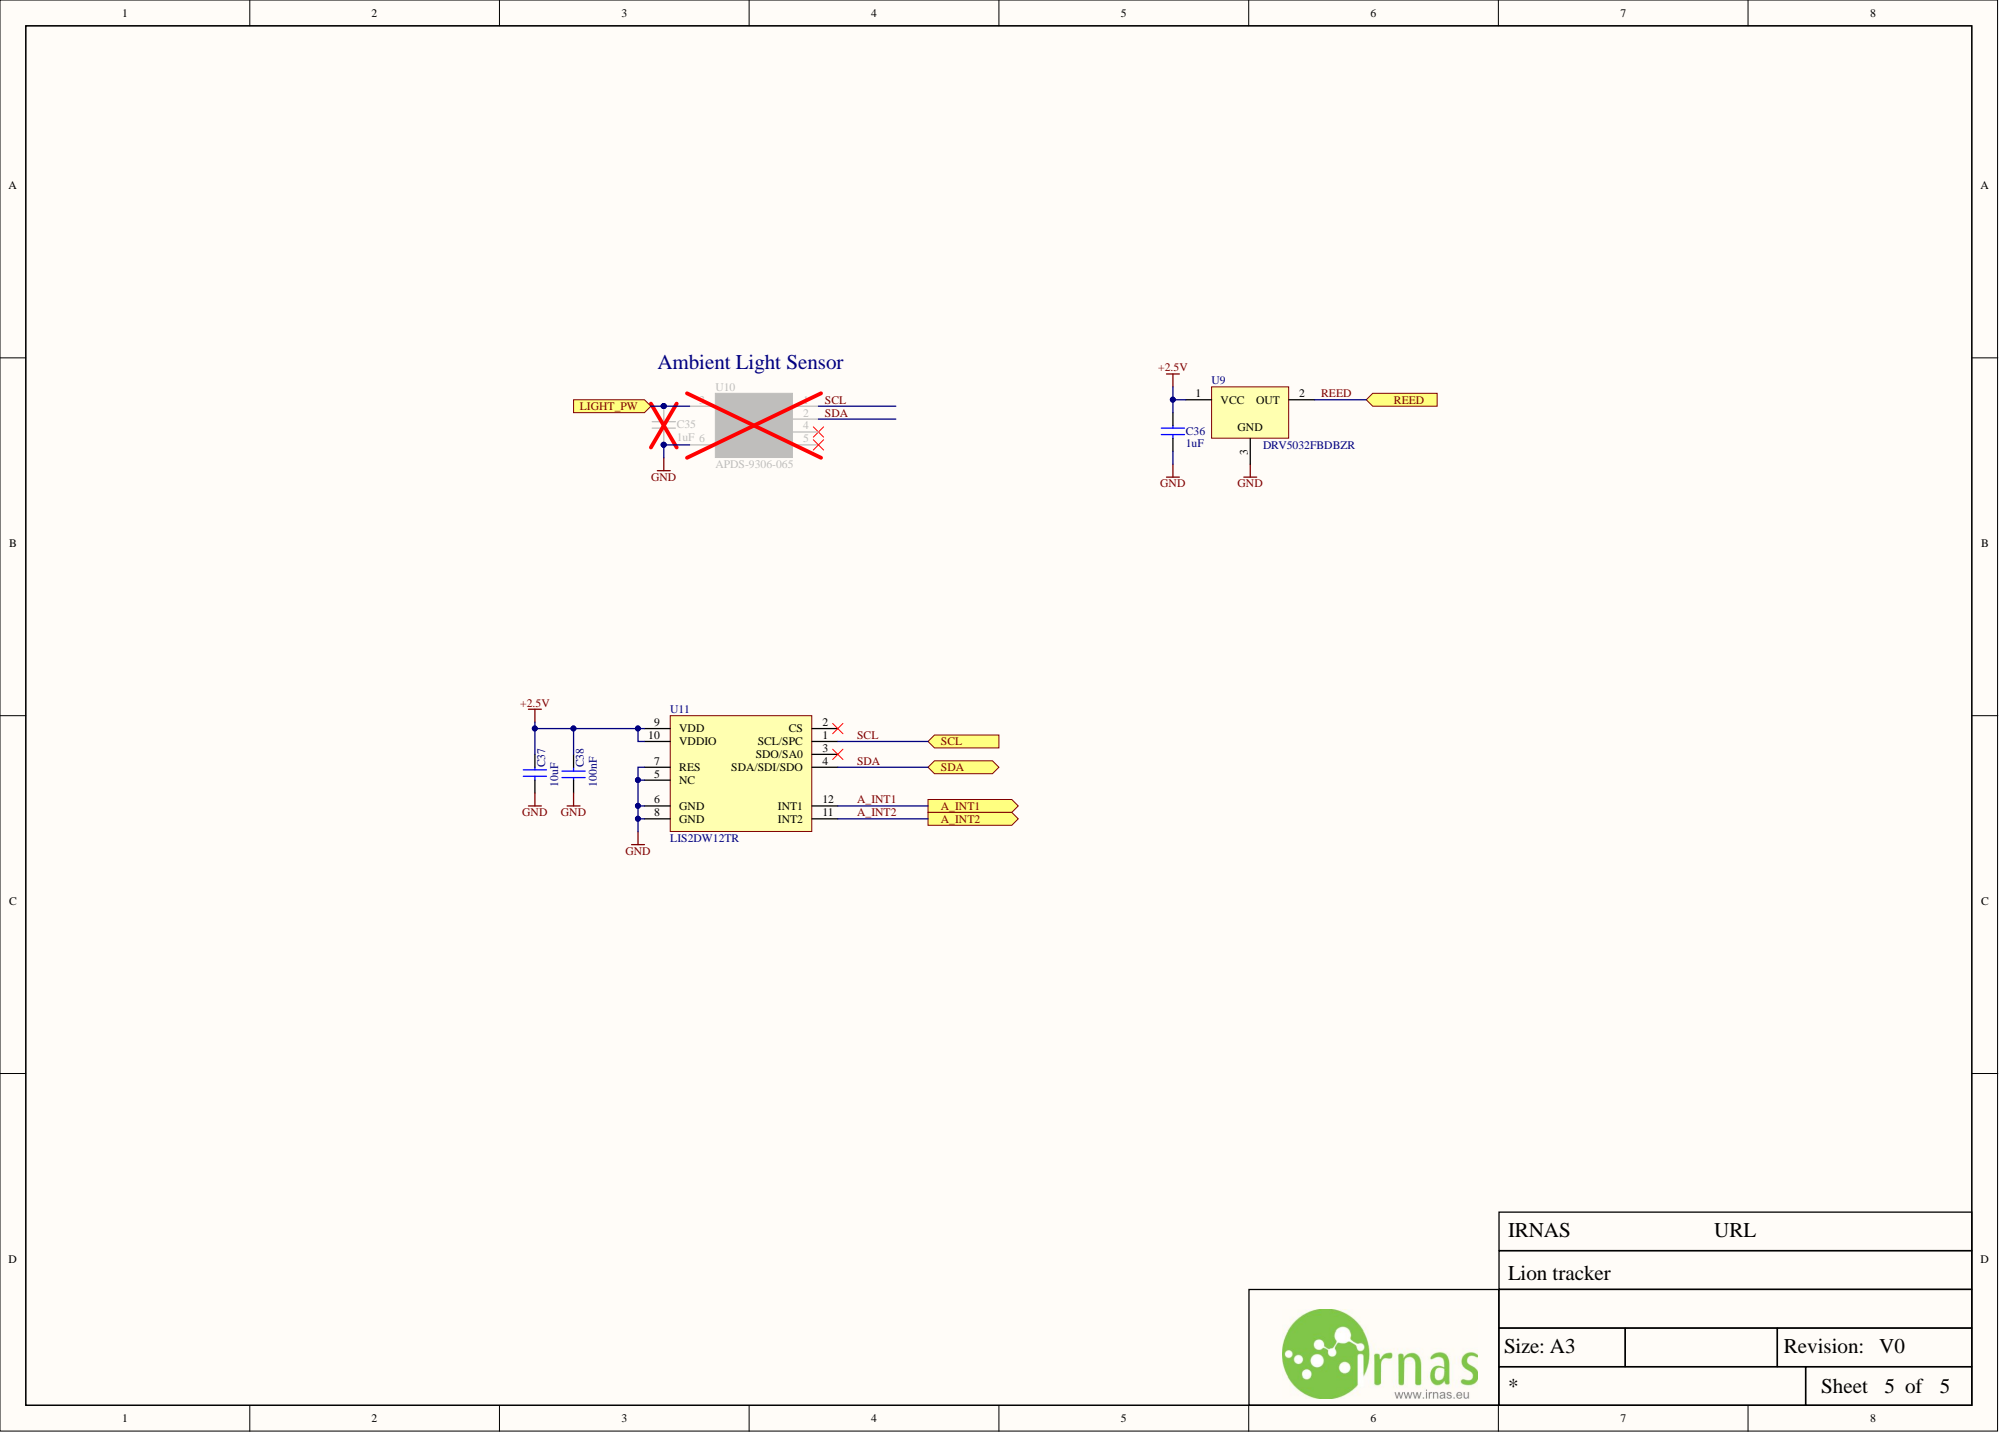
[picture p73: page 5]
