IRNAS/smartparks-lion-tracker-hardware/LION/06_RELEASE/V1.3/Lion_Tracker_V1.3_SCHEMATICS/Lion_Tracker_V1.3_SCHEMATICS.PDF

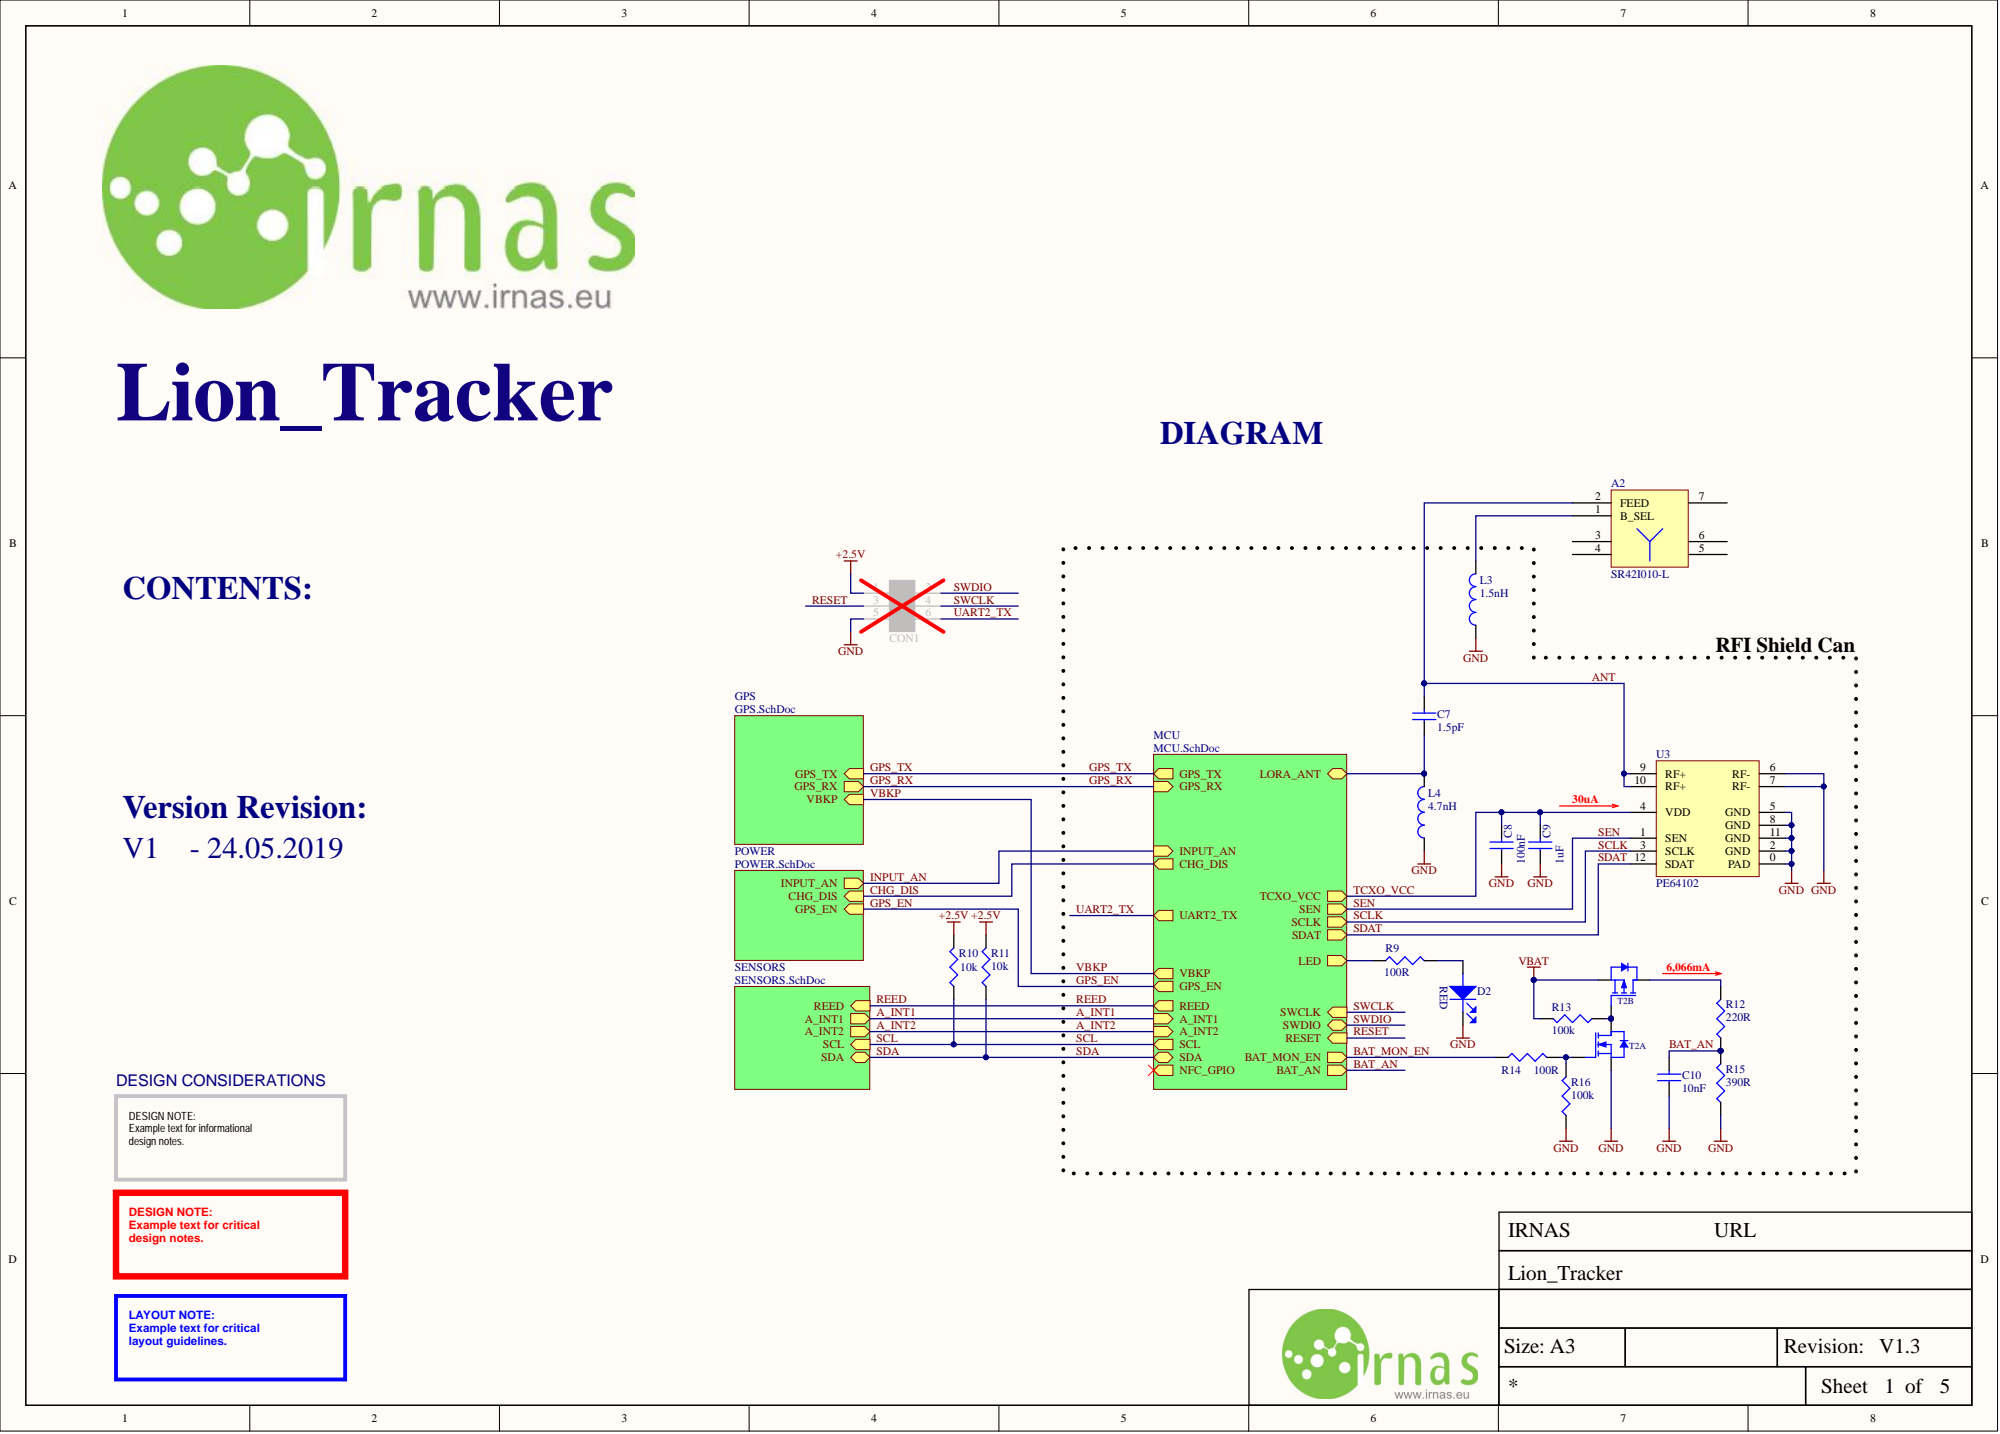
[picture p84: page 1]

SEN | | 1 1
SCLK | 3
SDAT | SDAT 12 | 0

INPUT_AN | | | GND TCXO_VCC
CHG_DIS

+2.5V +2.5V R10 R1 1 10k 10k | VBKP | | SCLK

UART2_TX | | SEN

GPS_EN

REED A_INT1 A_INT2 SCL SDA | REED | REED

A_INT1 | A_INT1
A_INT2 | A_INT2
SCL | SCL
SDA | SDA

DESIGN NOTE:
Example text for informational
design notes.

Example text for critical

LAYOUT NOTE:
layout guidelines.

Size: A3 | | Revision: V1.3

Sheet of

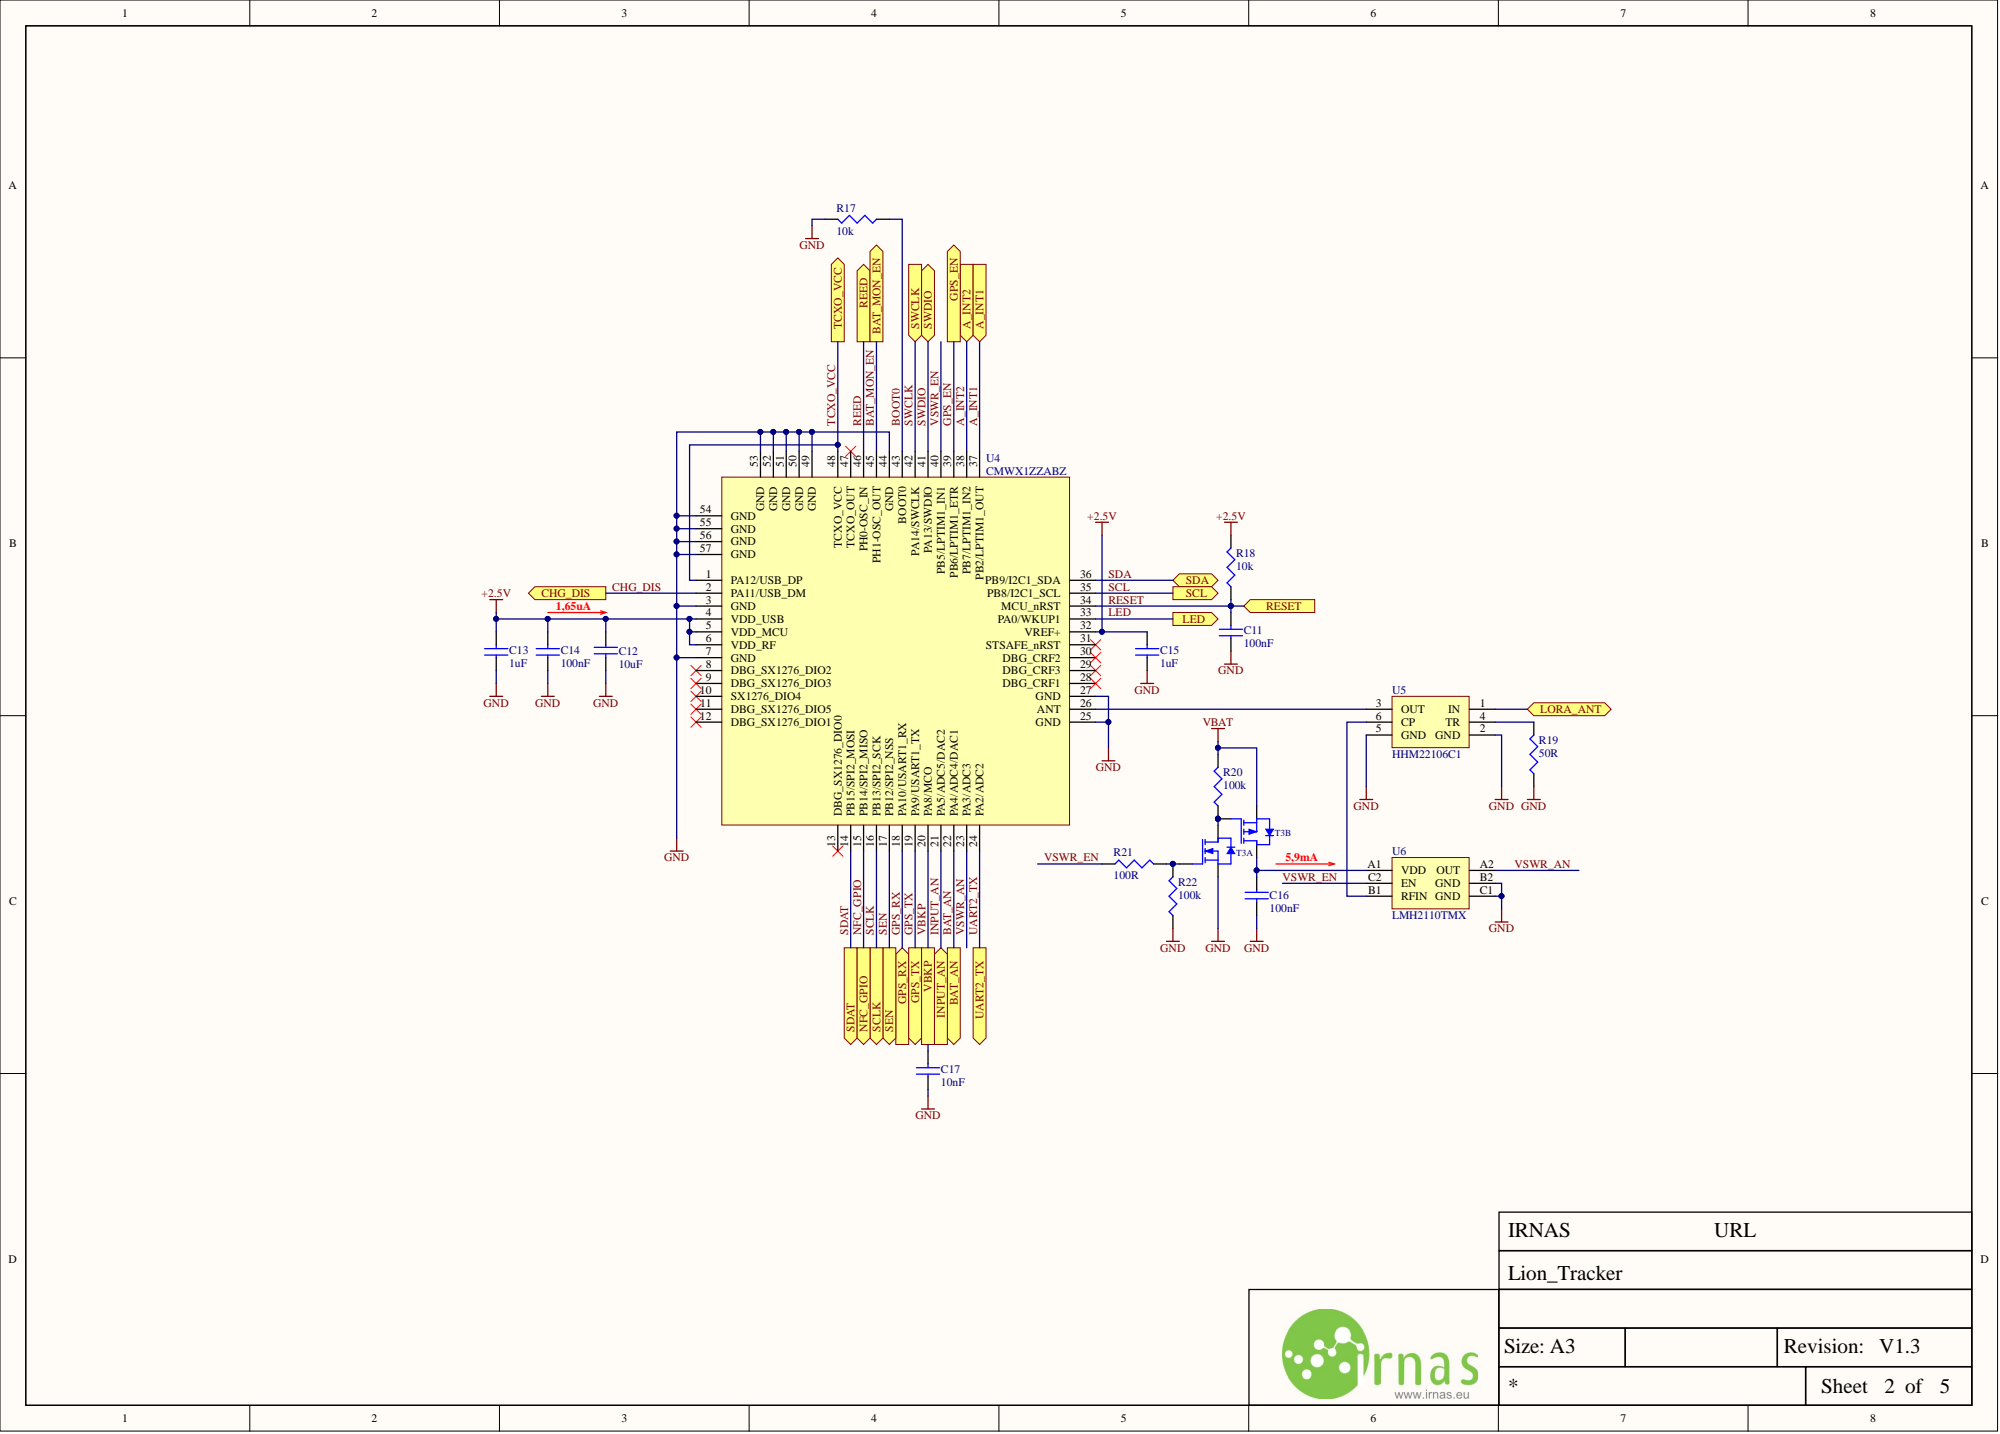
[picture p85: page 2]

GND 50 GND 51 GND 52 GND 53

GND 54 | PA0/WKUP1 | 35 PB9/I2C1_SDA P
GND 55
GND 56
GND 57

PA12/USB_DP 1
PA11/USB_DM 2 | 33 MCU_nRST 34 PB8/I2C1_SCL

GND 3 | RESET
VDD_USB 4

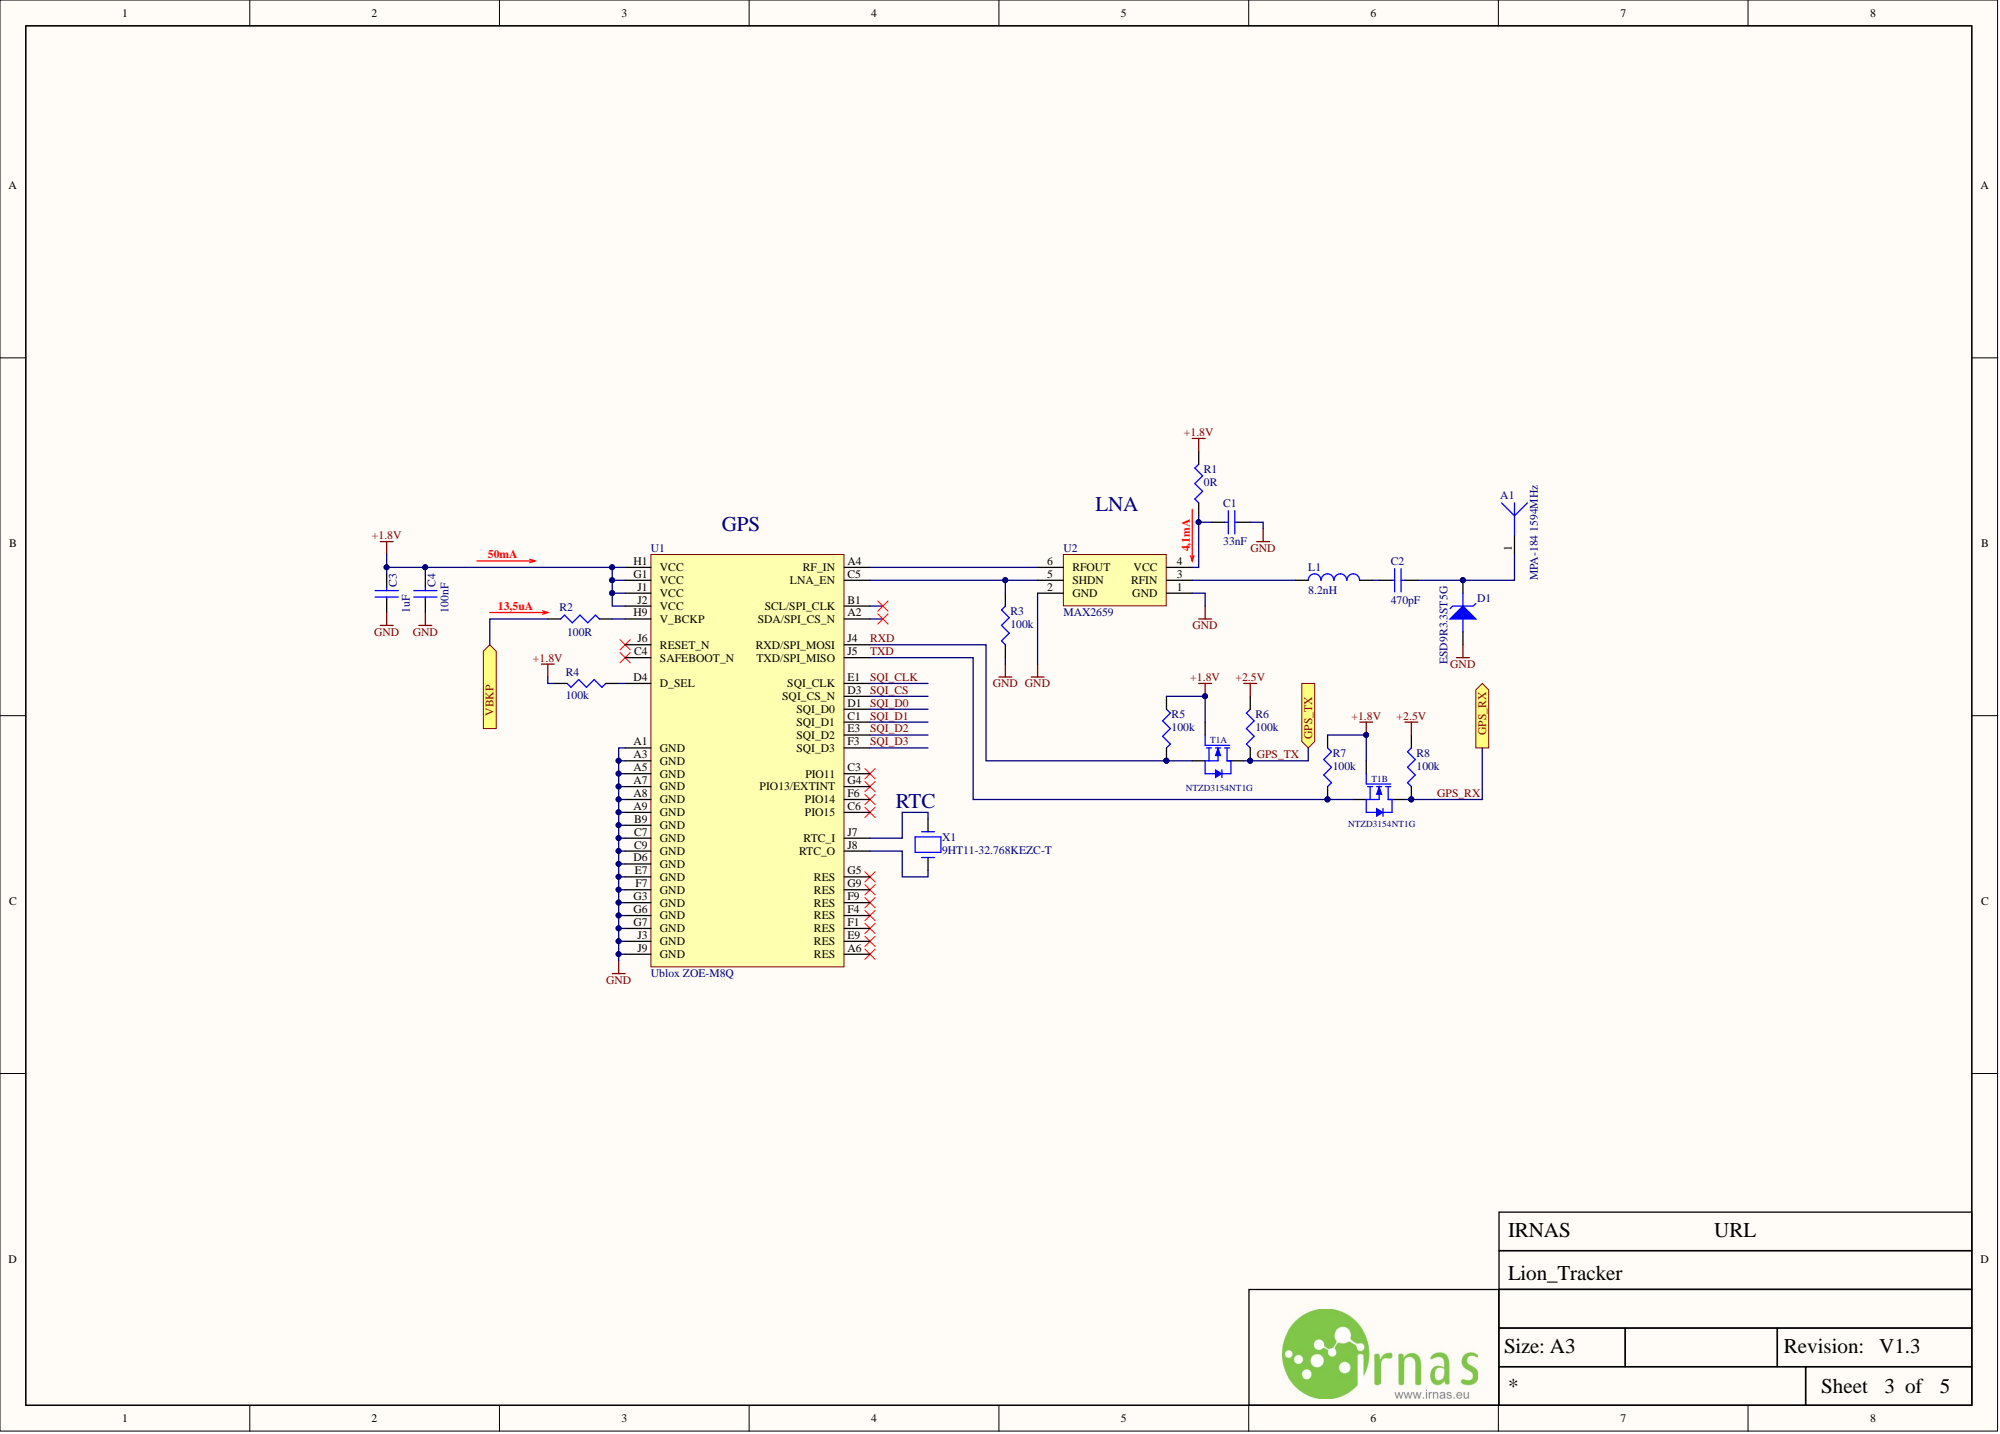
[picture p86: page 3]

TXD

GND | +1.8V +2.5V

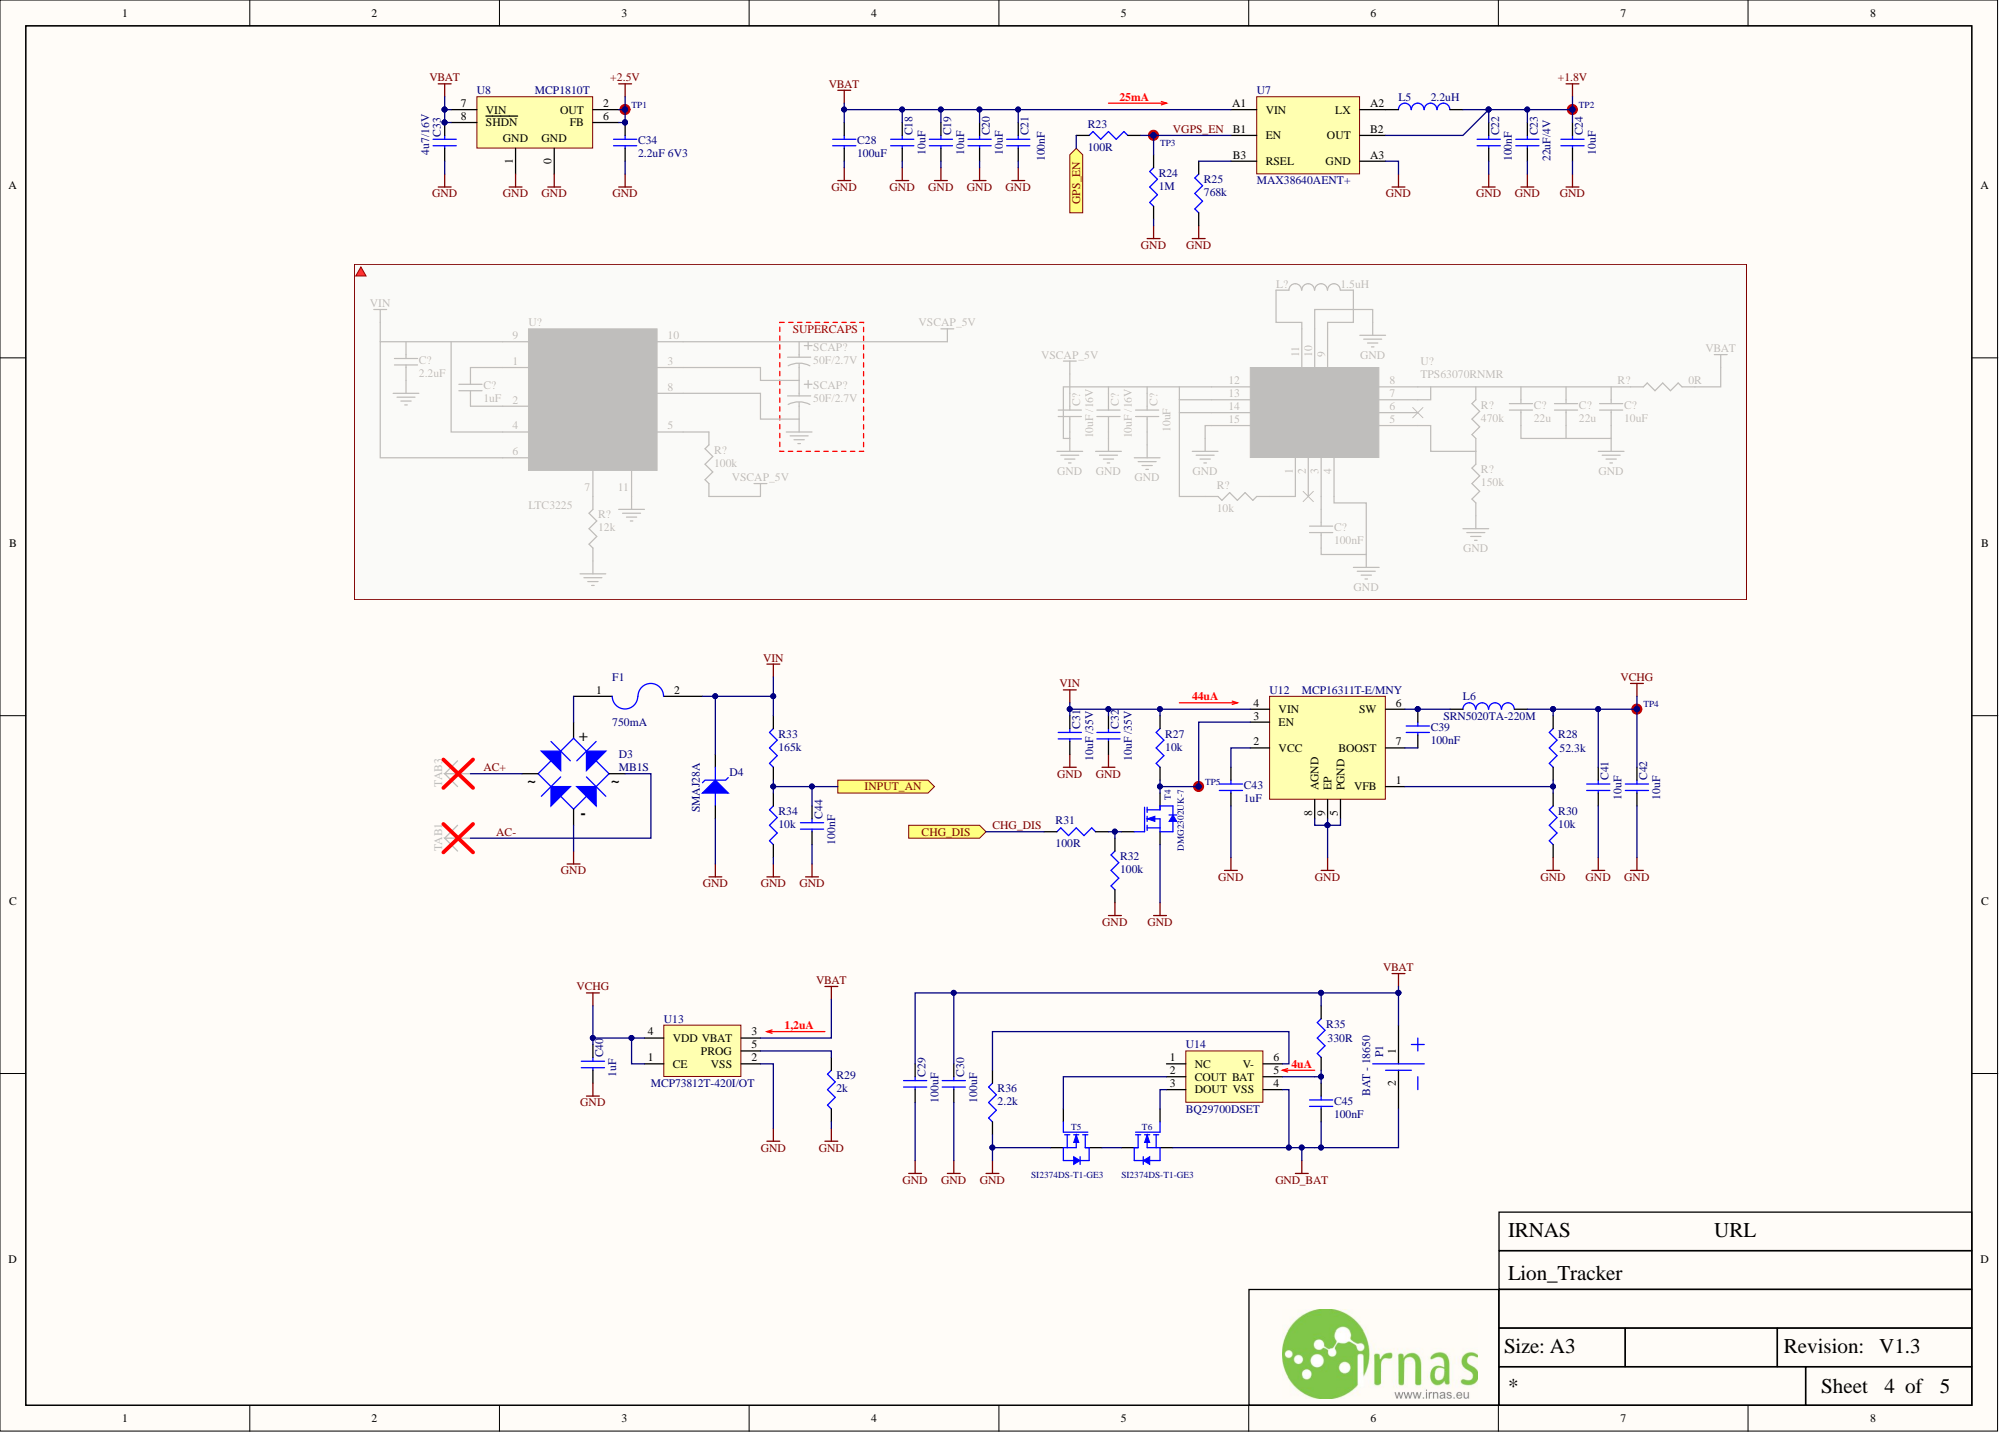
[picture p87: page 4]

VIN 13

VSEL 15

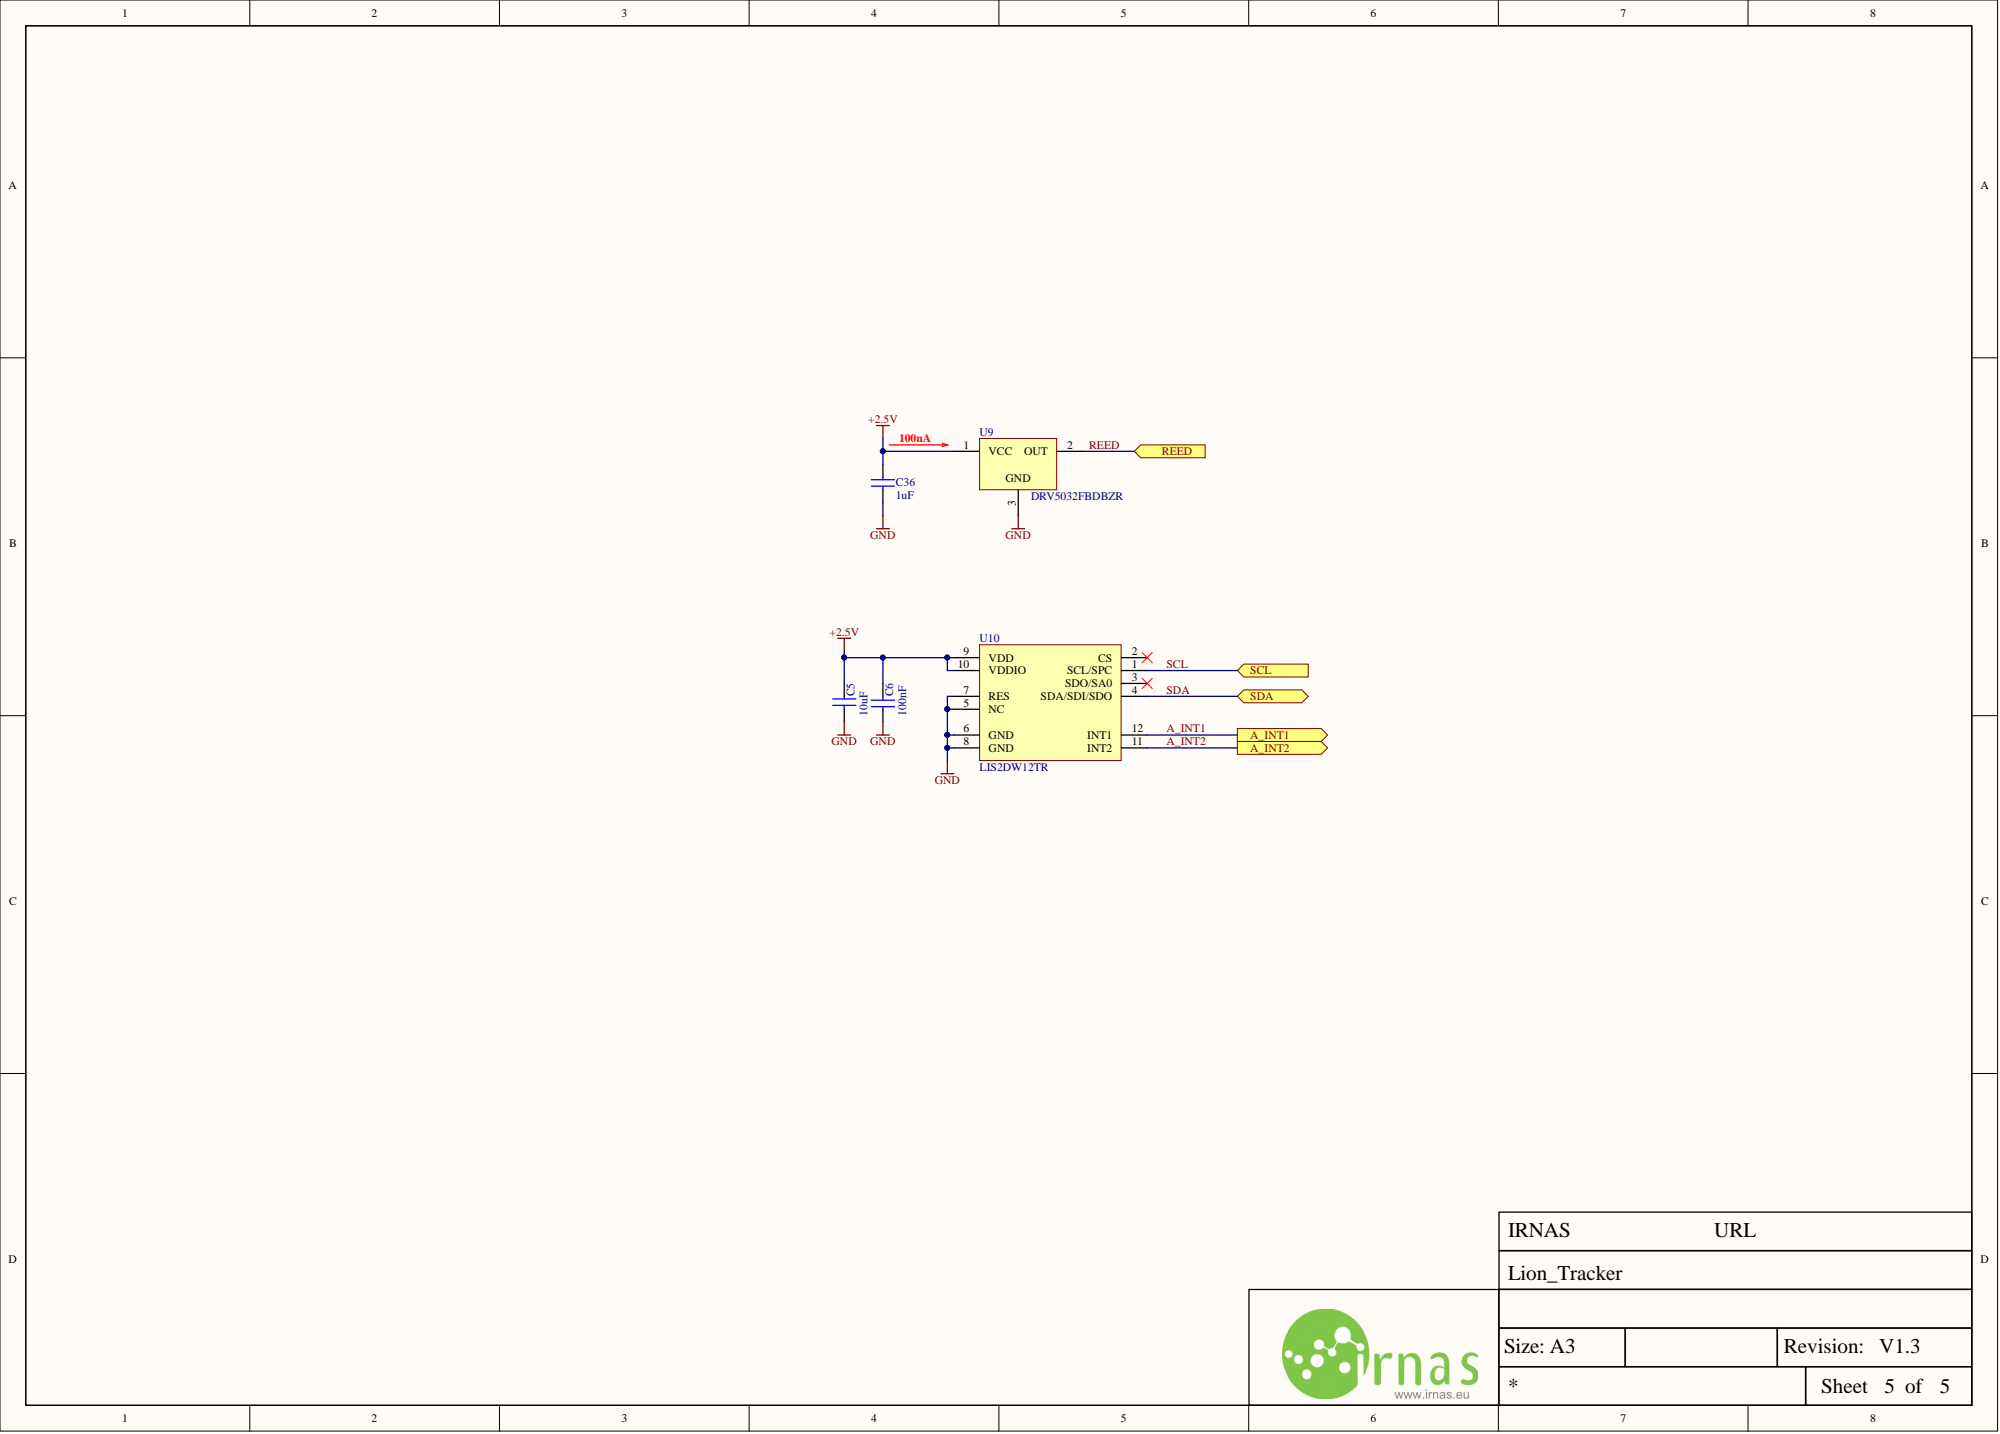
[picture p88: page 5]
