IRNAS/smartparks-lion-tracker-hardware/Fence_monitor/06_RELEASE/V1/Fence monitor_V1_ASSEMBLY/Fence monitor_V1_ASSEMBLY.PDF

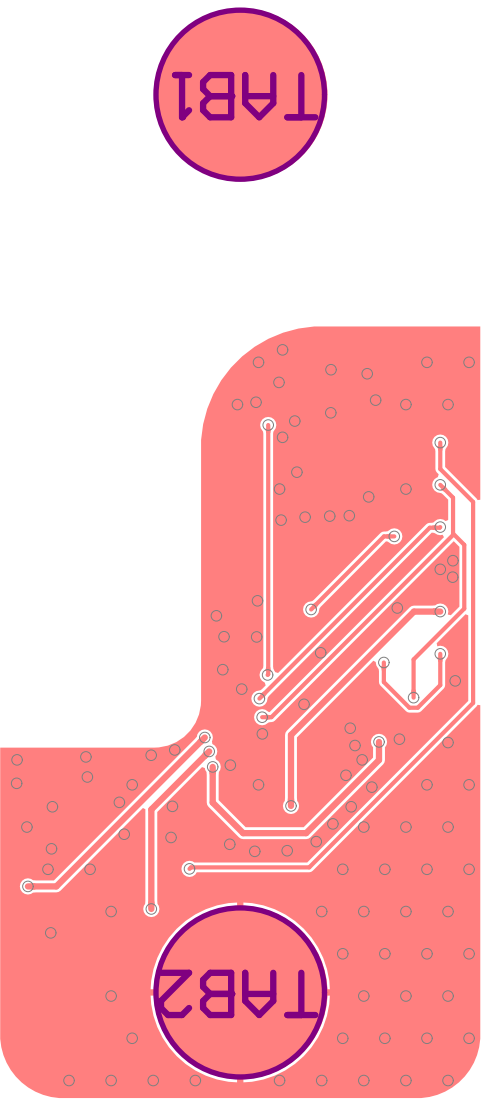
[picture p89: page 1]

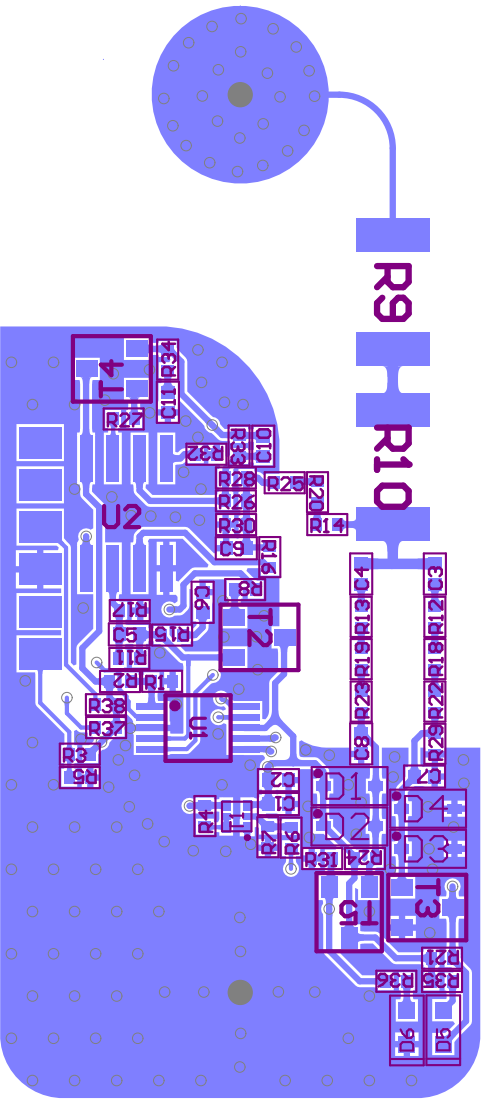
[picture p90: page 2]
