IRNAS/smartparks-lion-tracker-hardware/Fence_monitor/06_RELEASE/V1/Fence monitor_V1_PCB_PRINT/Fence monitor_V1_PCB_PRINT.PDF

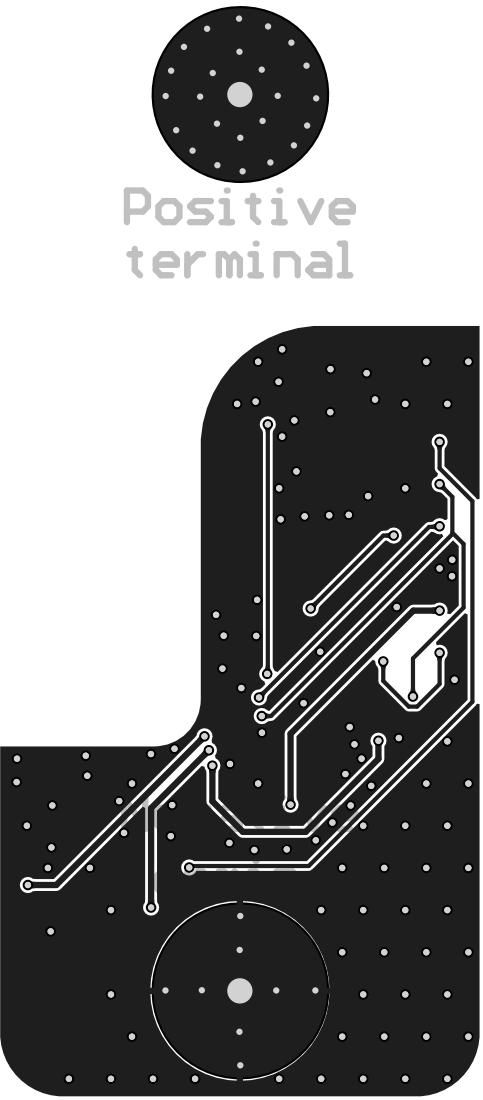
[picture p91: page 1]

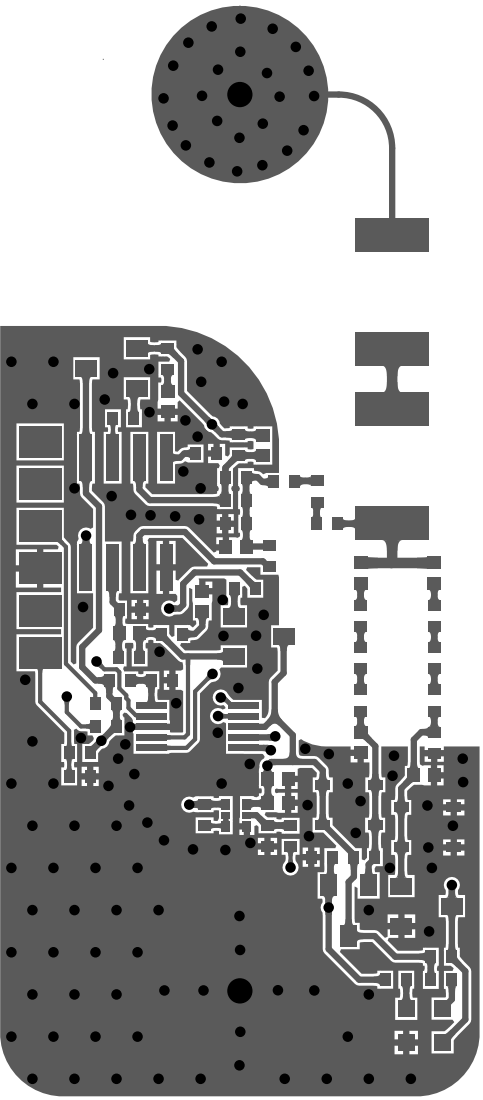
[picture p92: page 4]

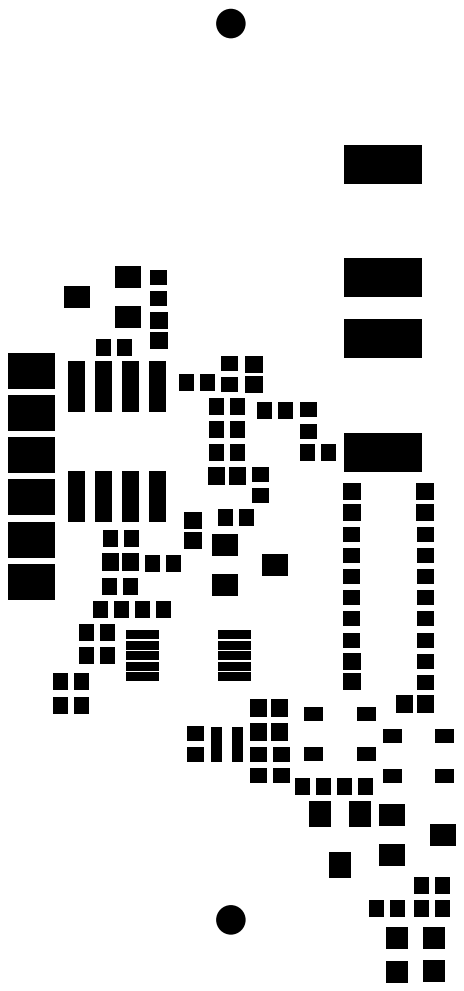
[picture p93: page 5]

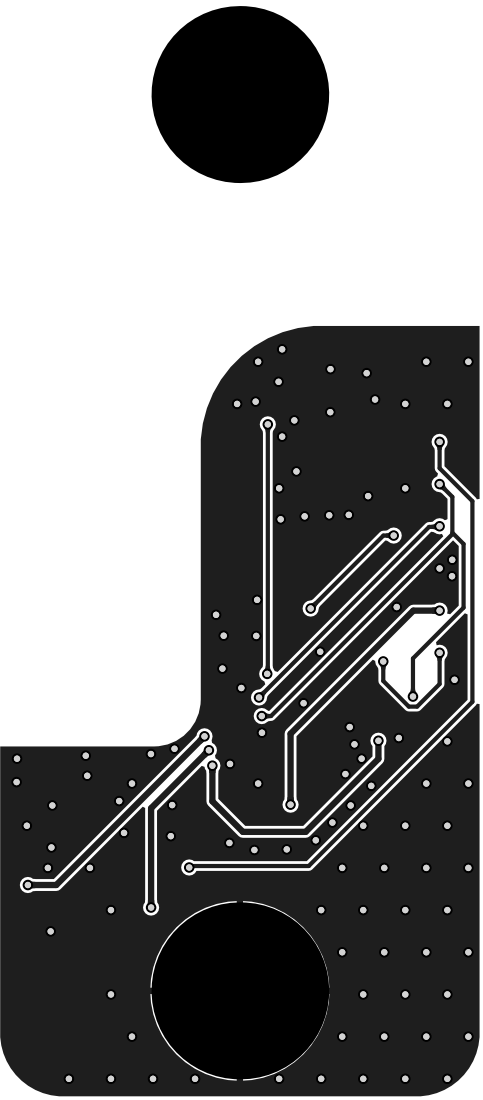
[picture p94: page 6]

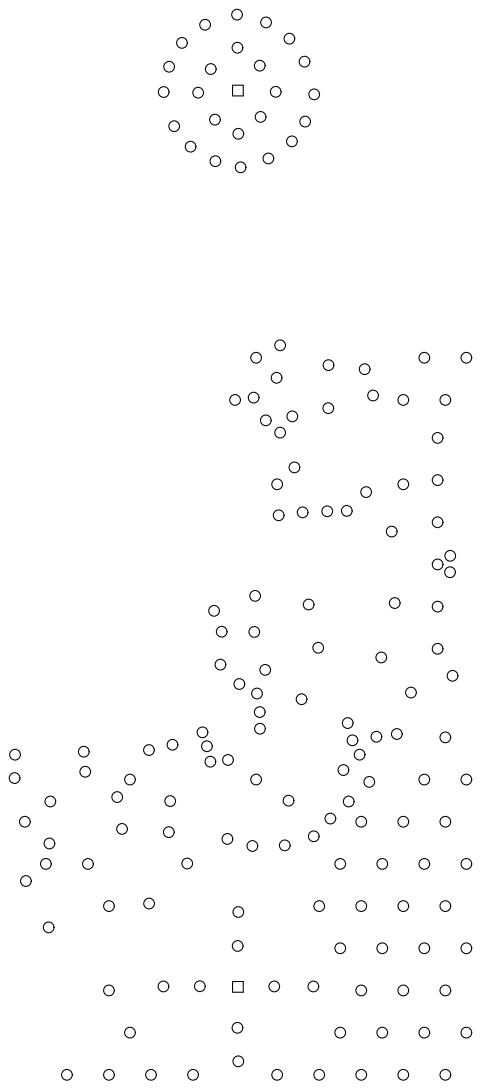
[picture p95: page 7]
