IRNAS/smartparks-lion-tracker-hardware/Fence_monitor/06_RELEASE/V1/Fence monitor_V1_SCHEMATICS/Fence monitor_V1_SCHEMATICS.PDF

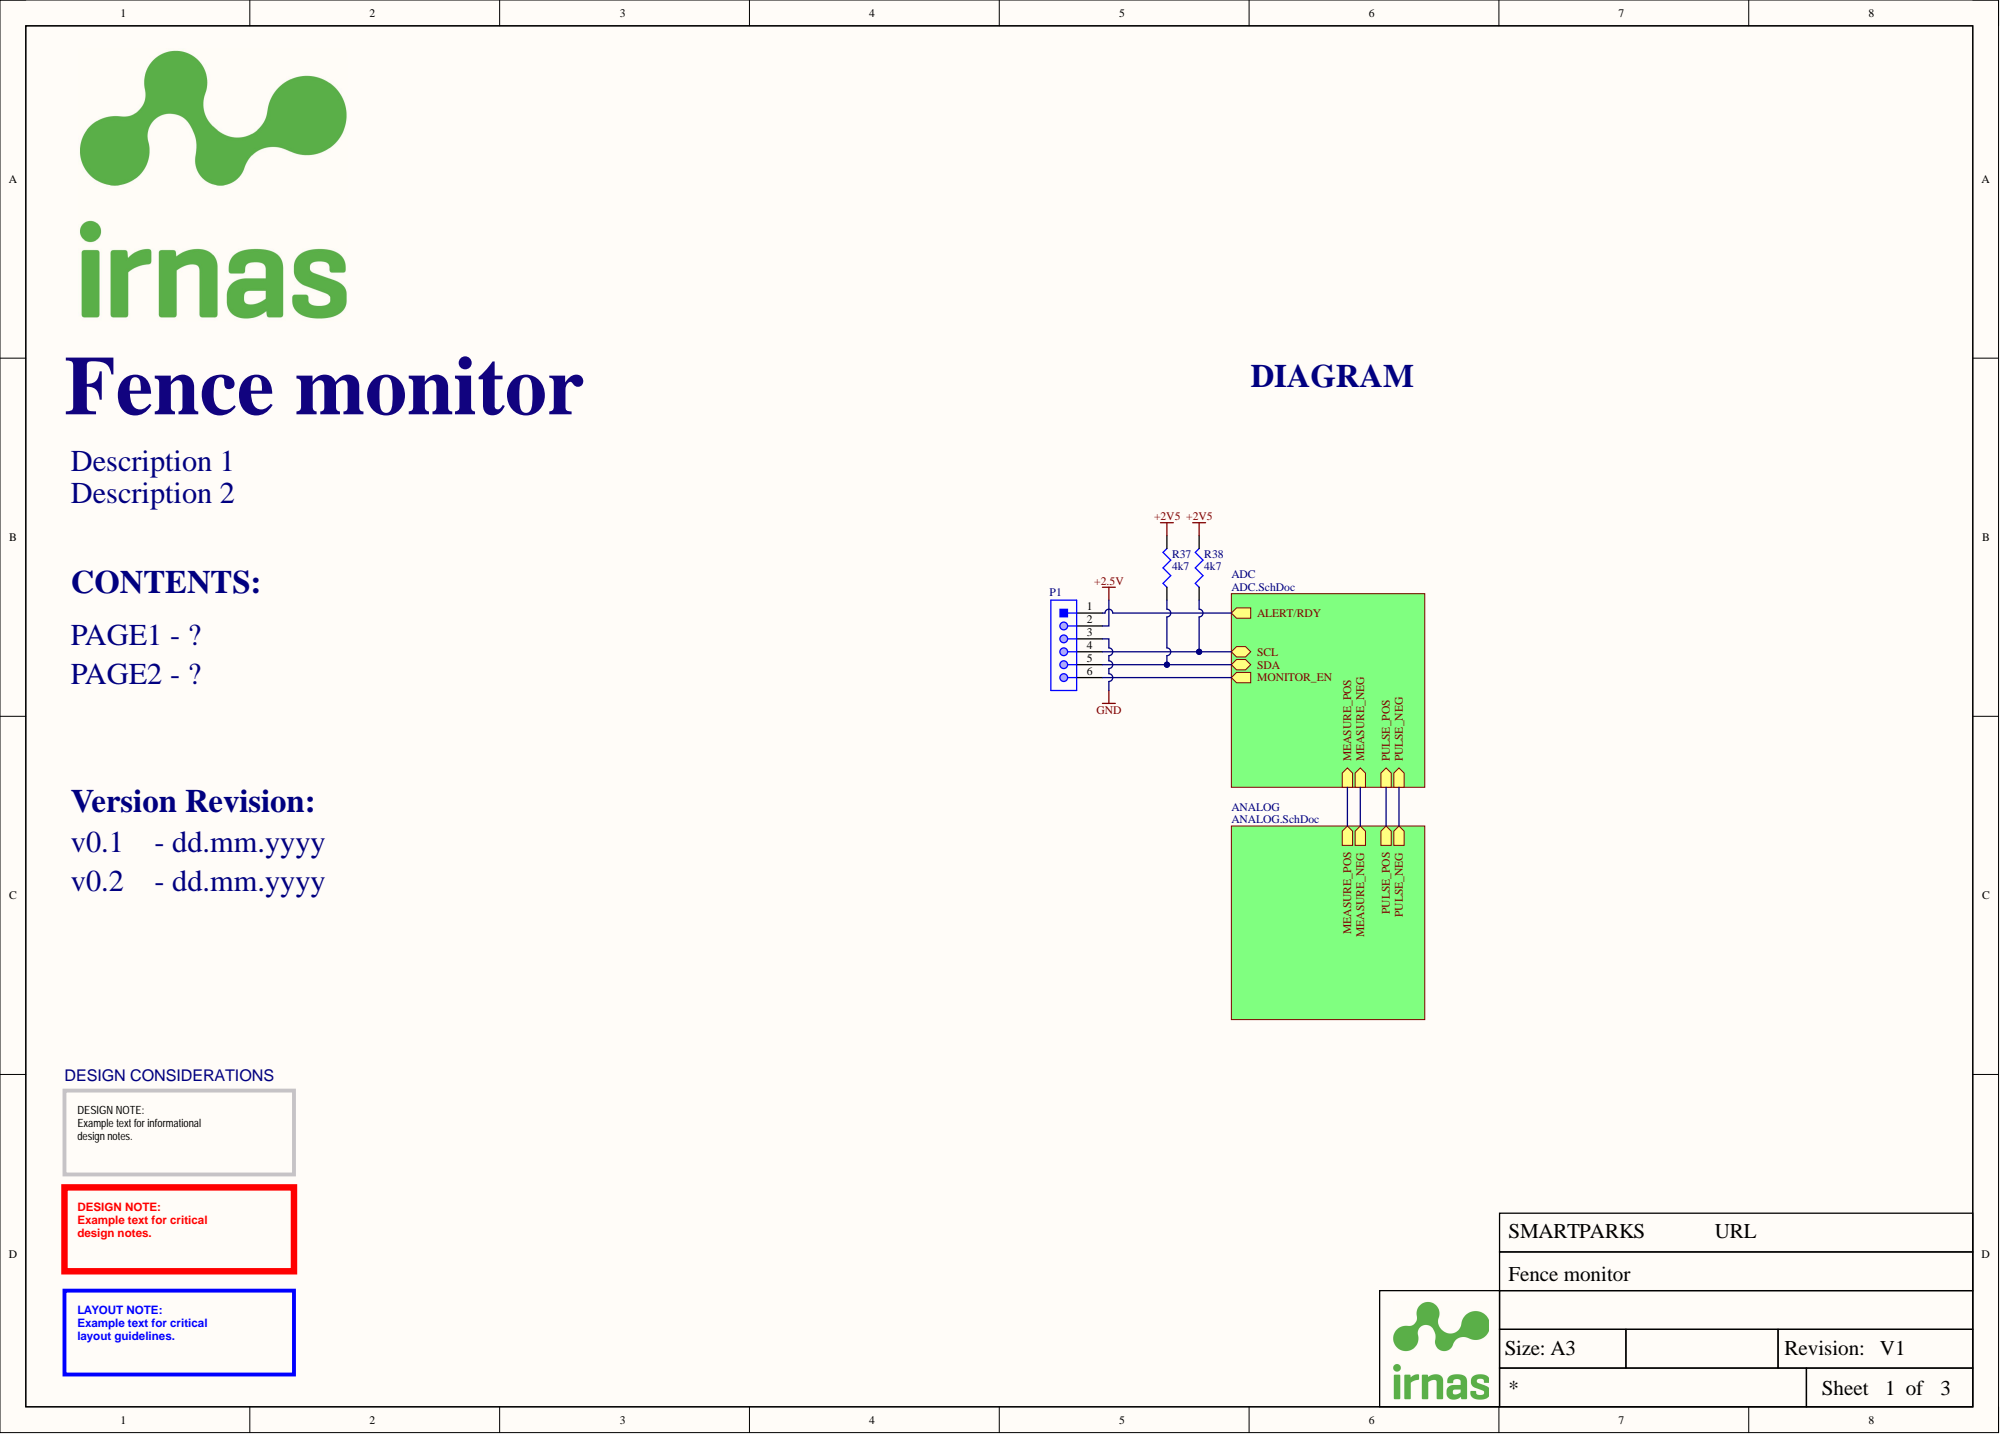
[picture p96: page 1]

DESIGN NOTE:
Example text for informational
design notes.

Example text for critical

LAYOUT NOTE:
layout guidelines.

Size: A3 | | Revision: V1

* | Sheet 1 of 3

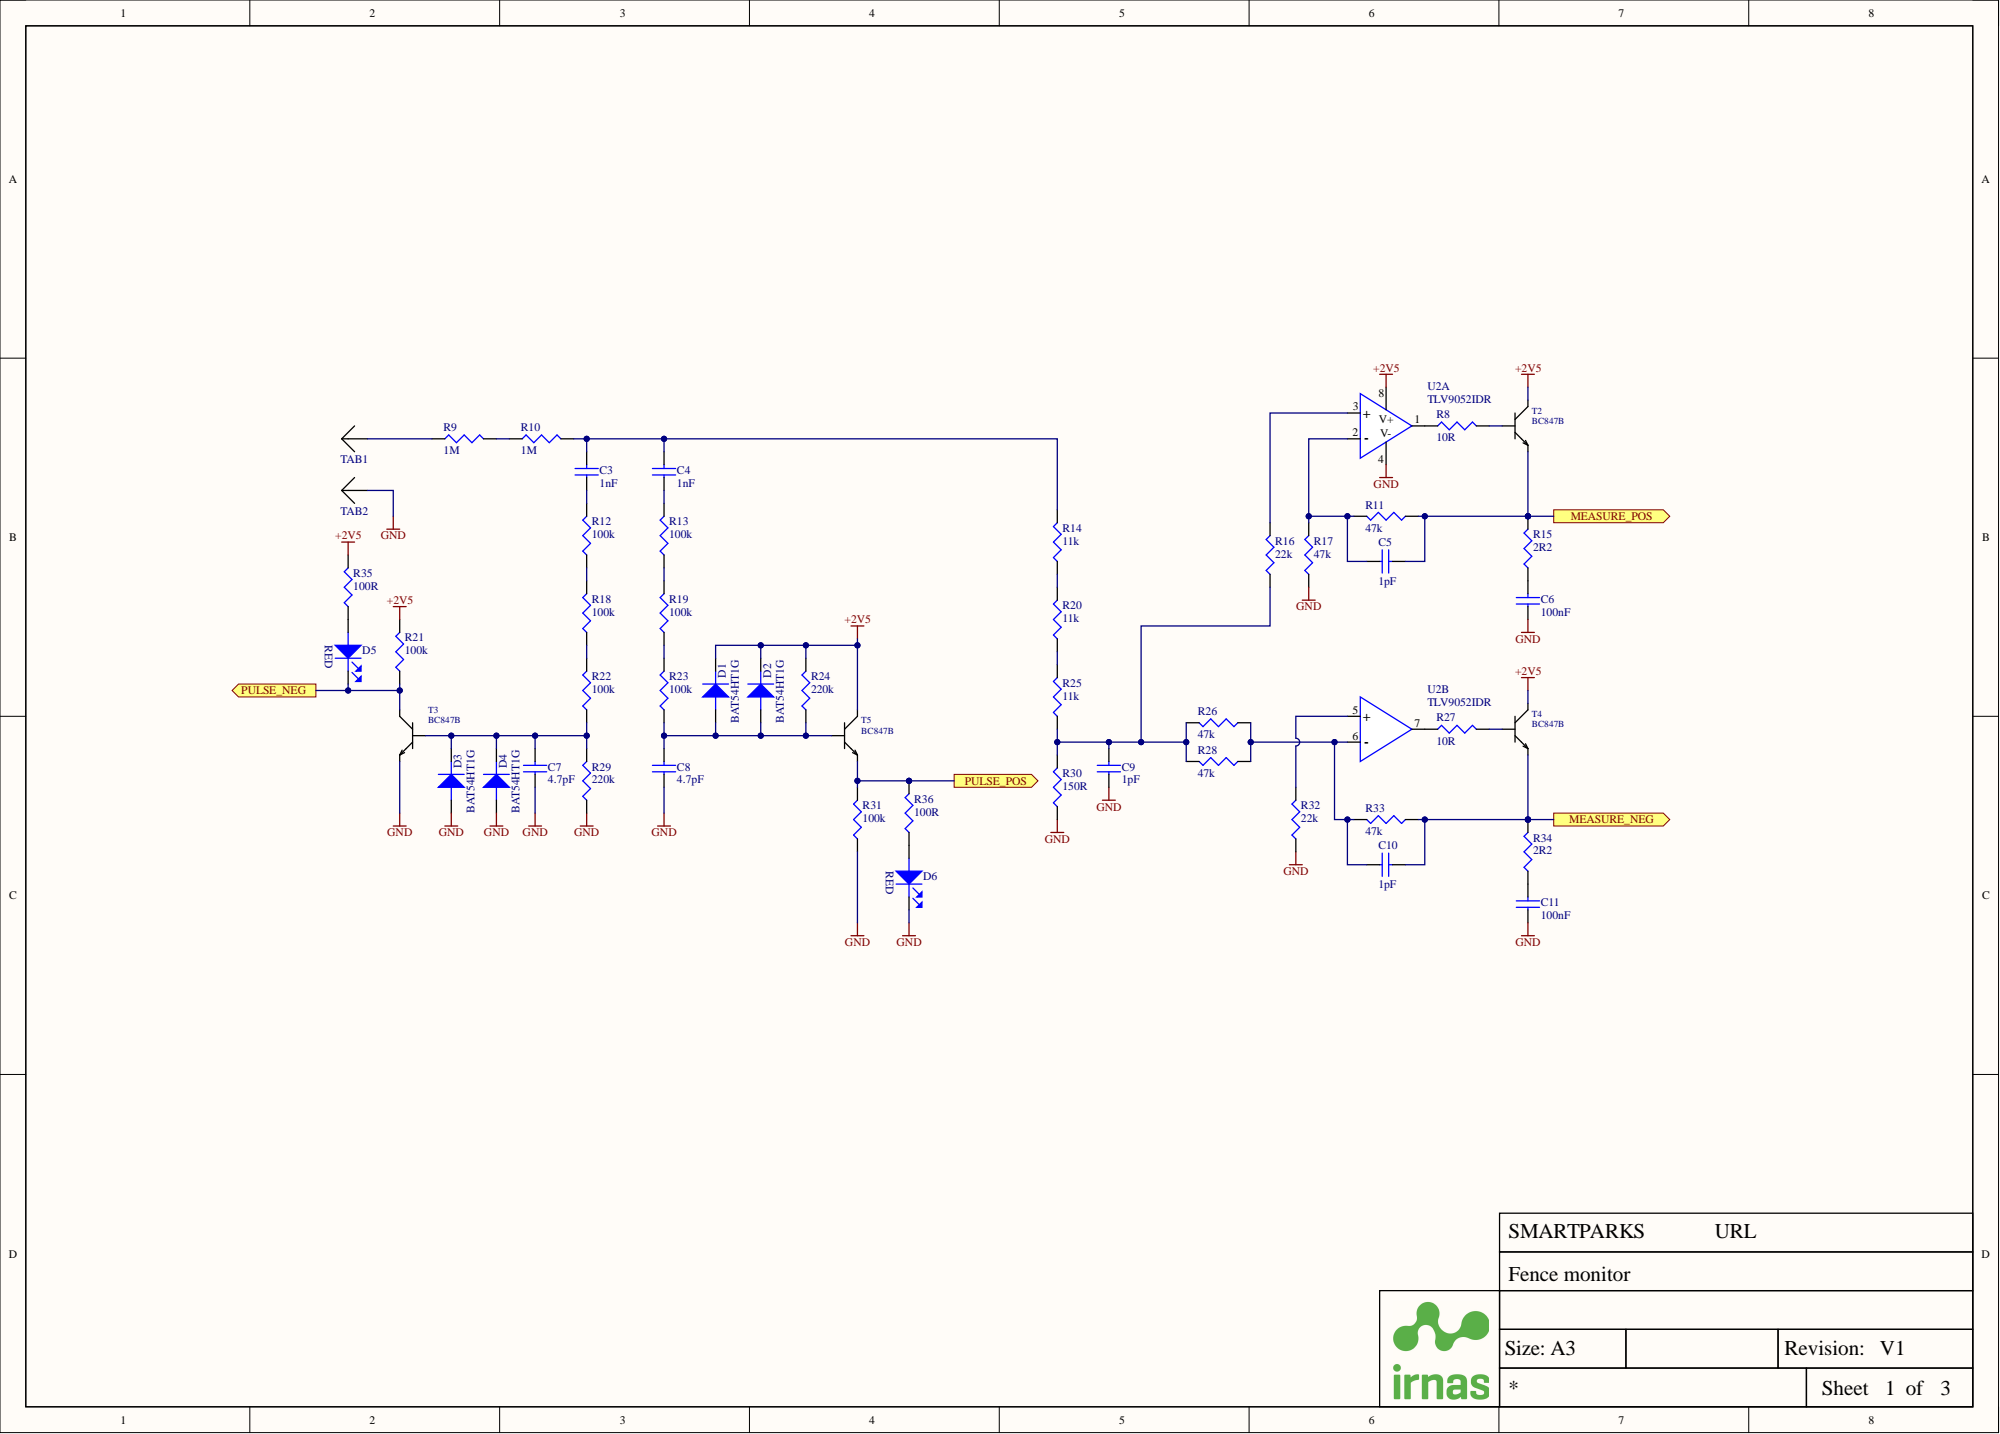
[picture p97: page 2]

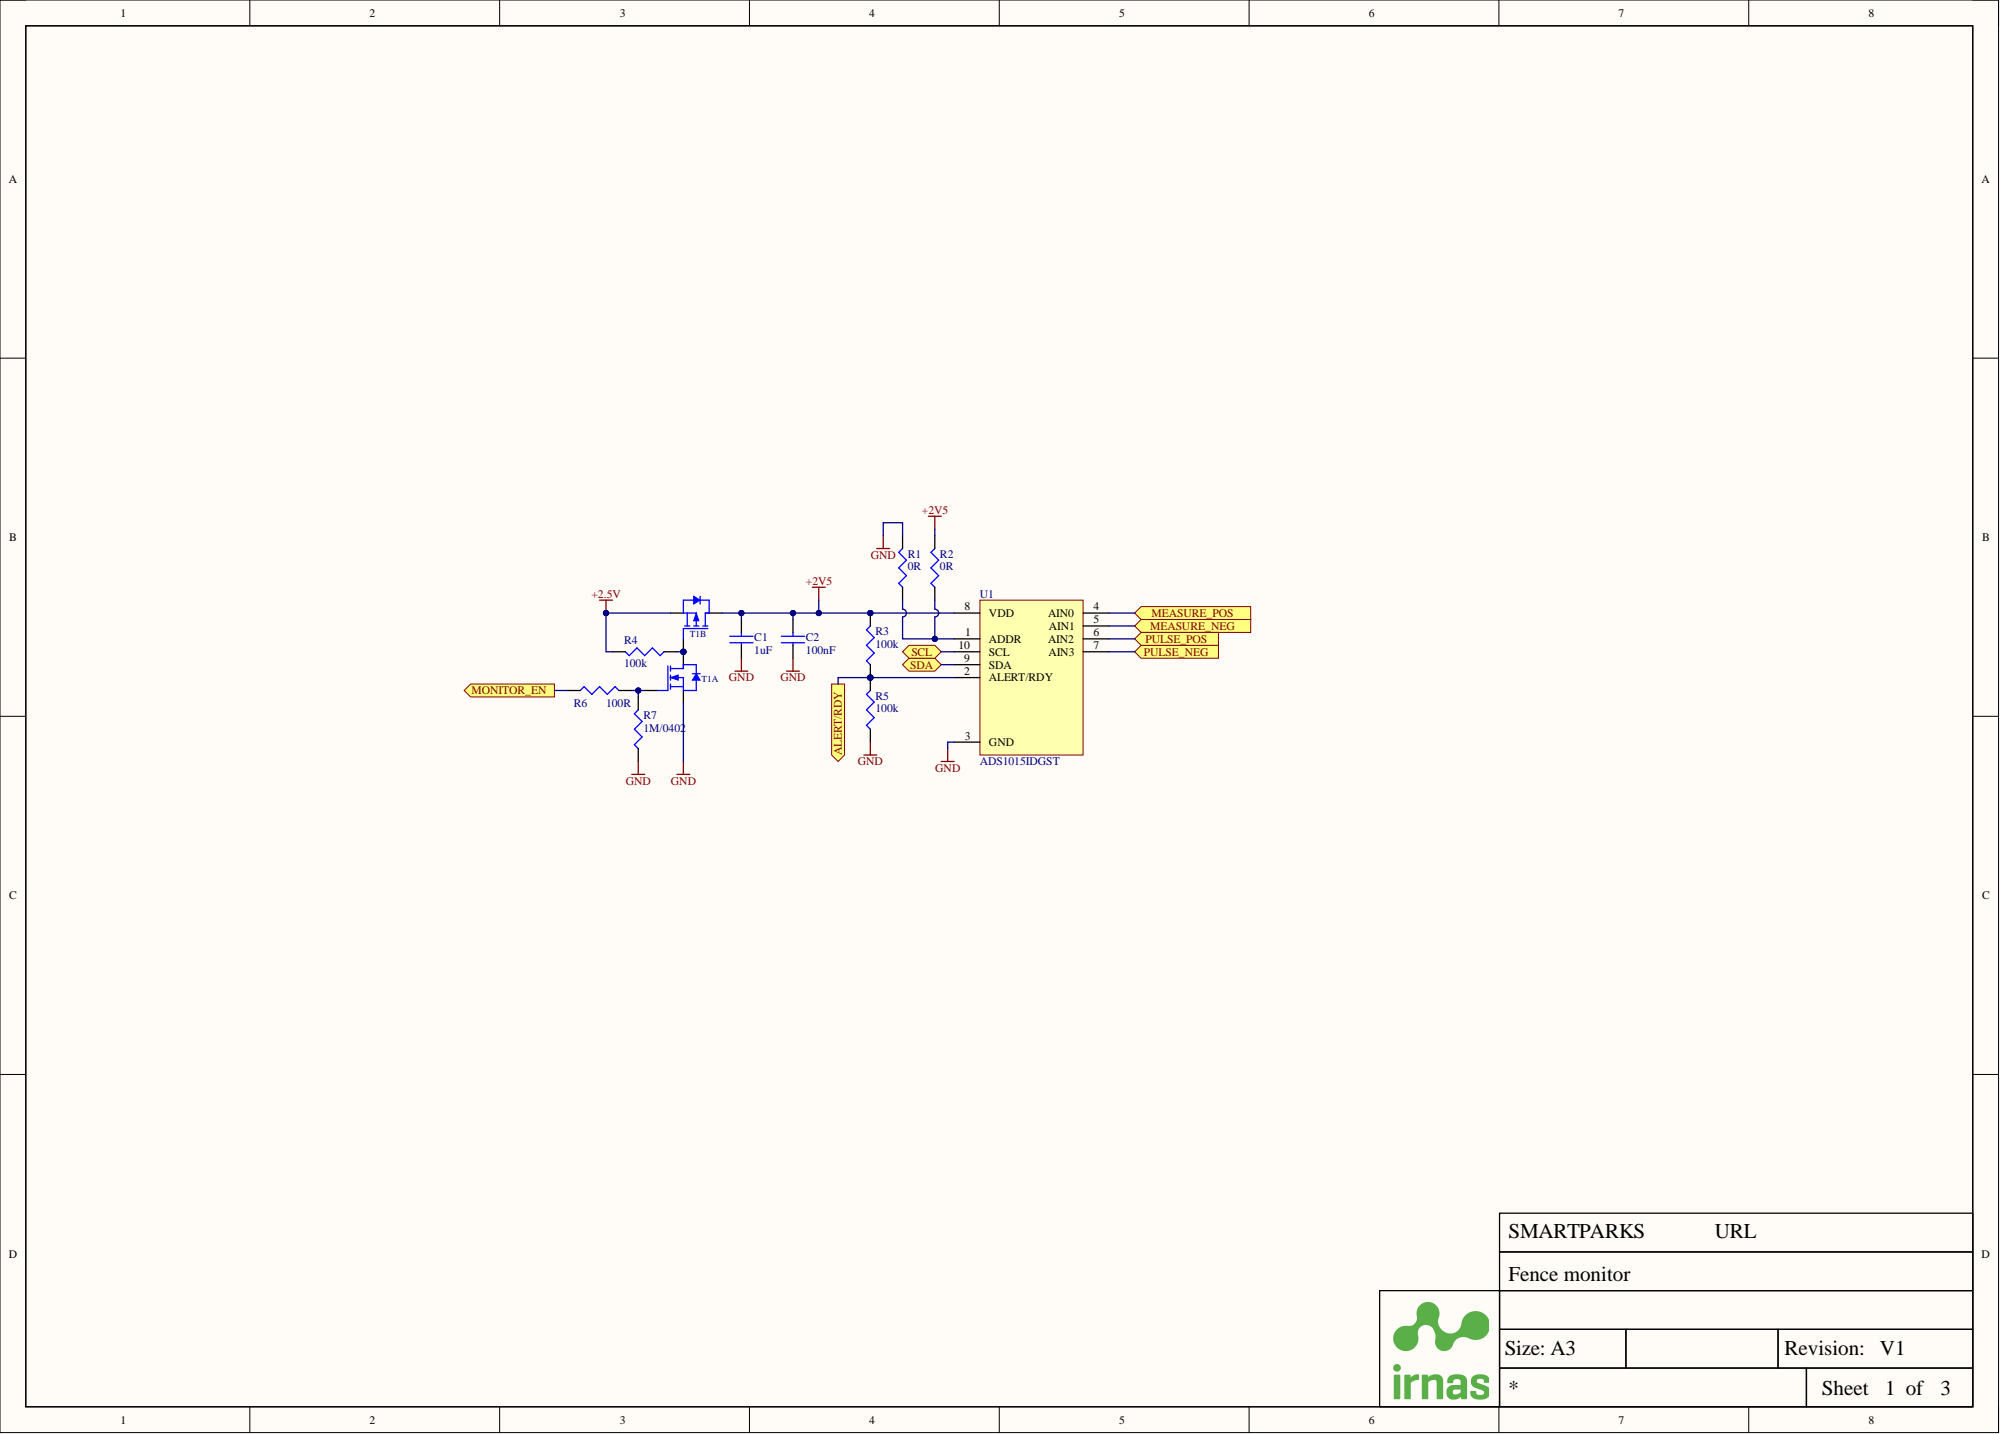
[picture p98: page 3]
