IRNAS/smartparks-lion-tracker-hardware/LION/06_RELEASE/V1.4/Lion_Tracker_V1.4_Assembly/Lion_Tracker_V1.4_Assembly.PDF

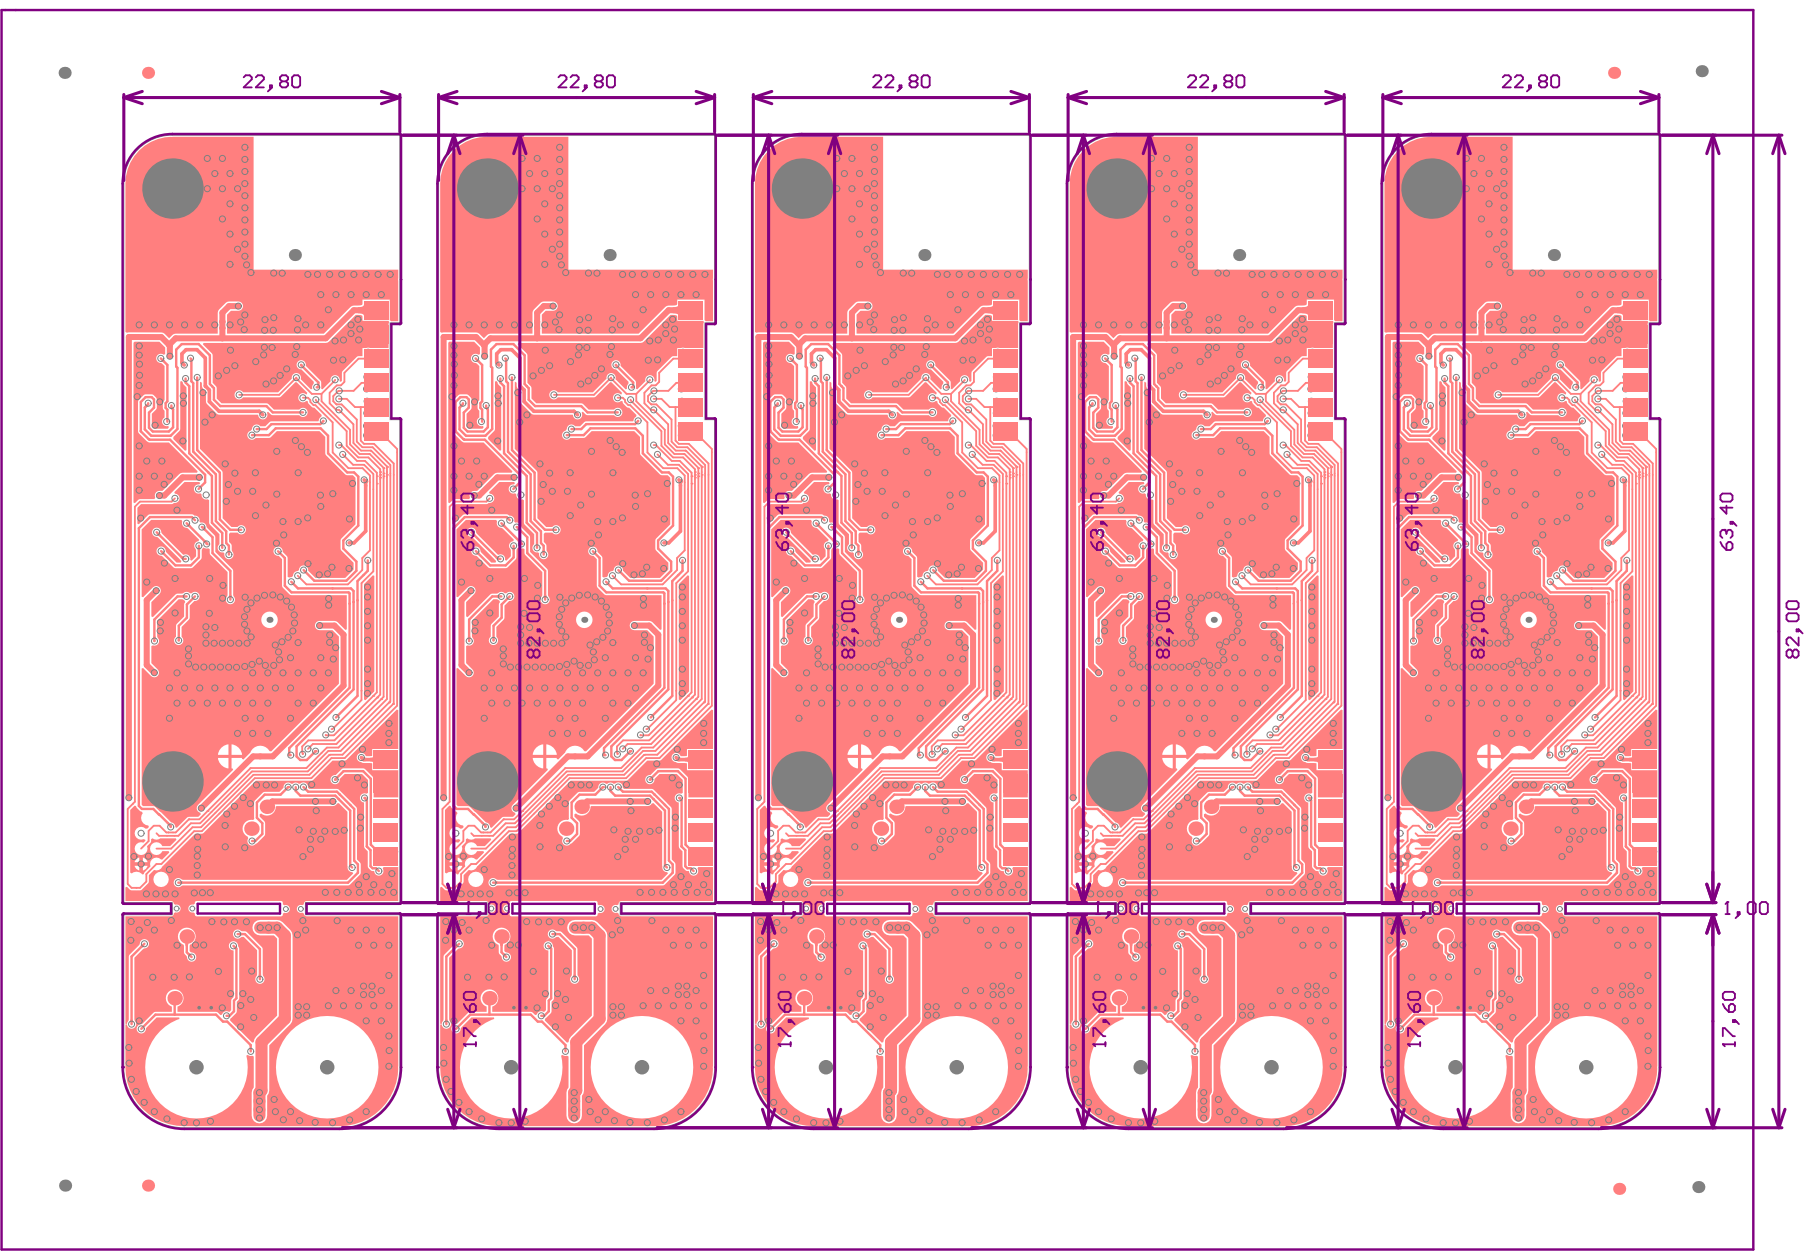
[picture p99: page 1]

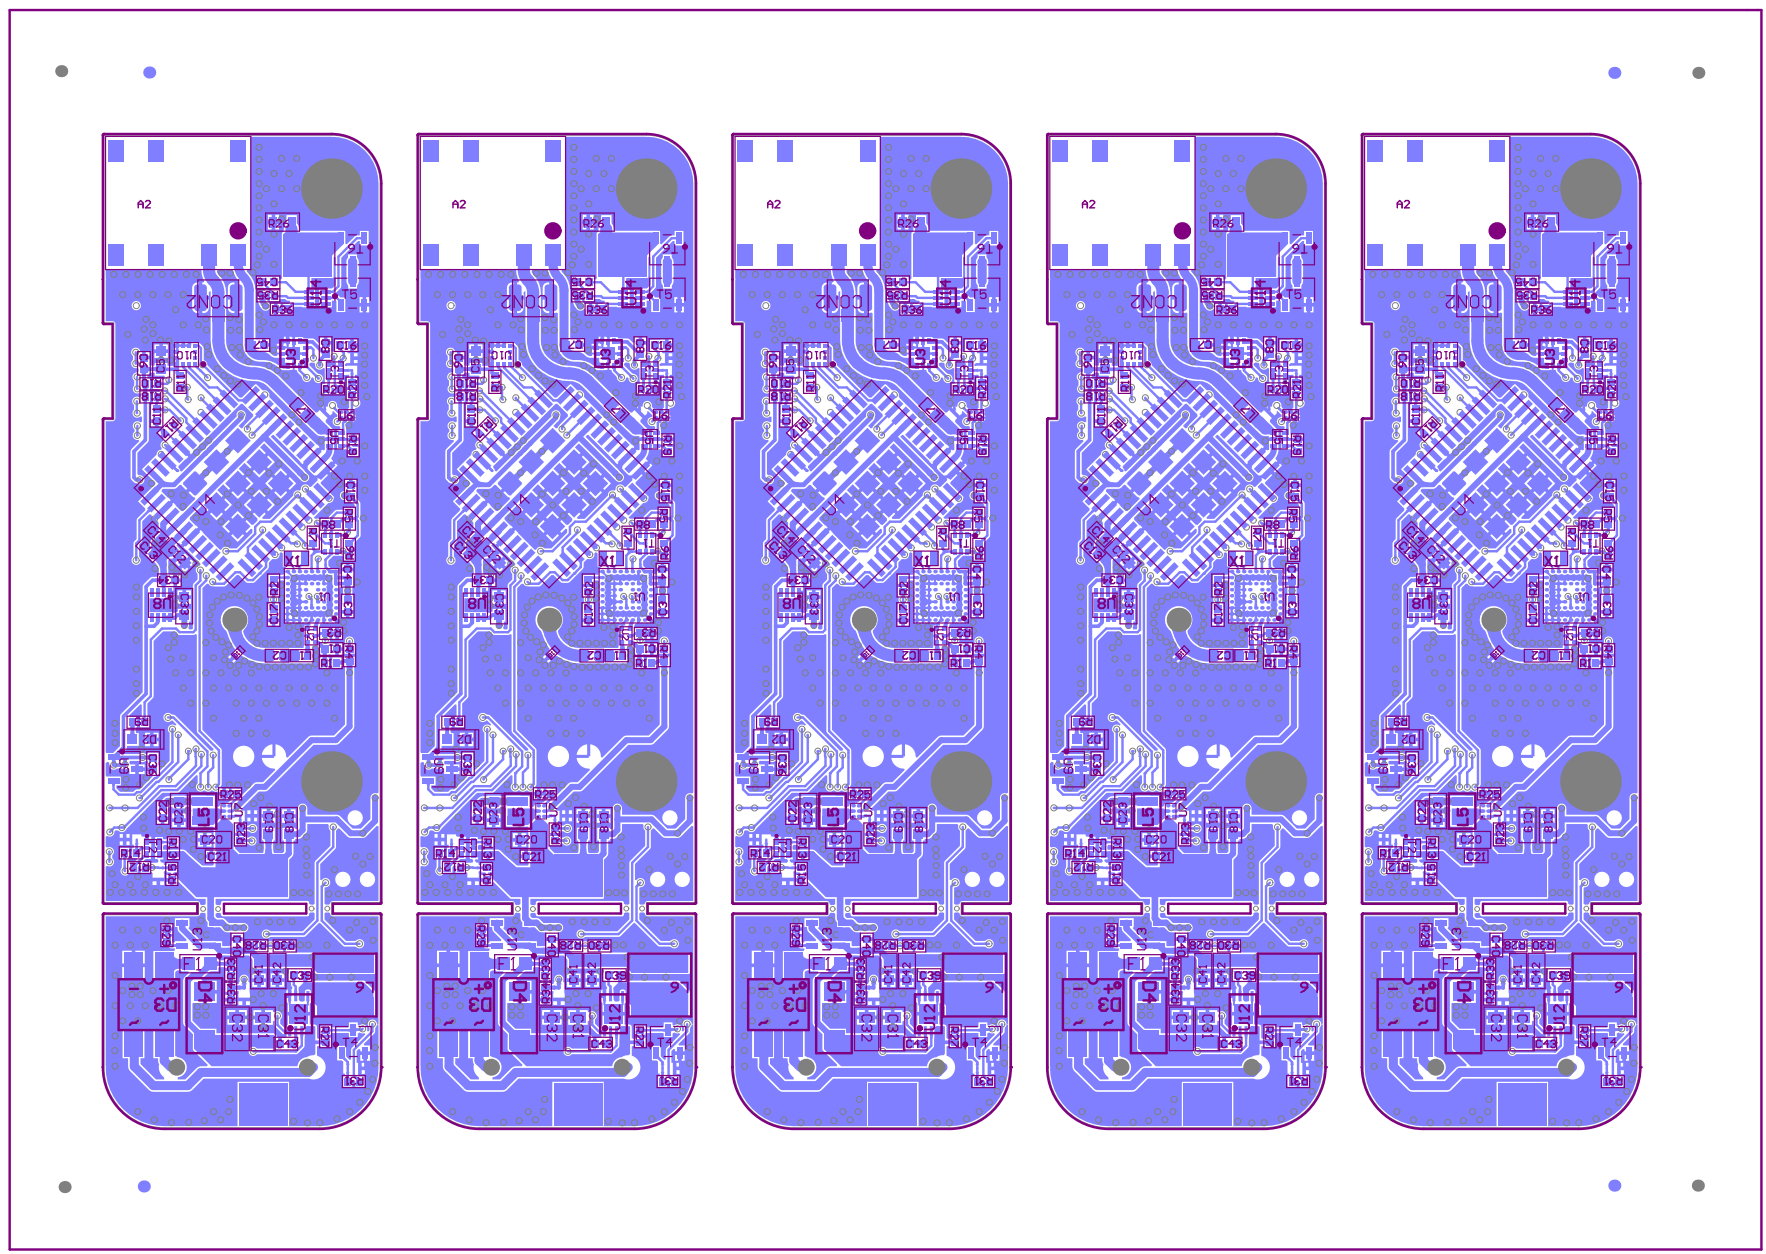
[picture p100: page 2]
