IRNAS/smartparks-lion-tracker-hardware/LION/06_RELEASE/V1.4/Lion_Tracker_V1.4_PCB_Print/Lion_Tracker_V1.4_PCB_Print.PDF

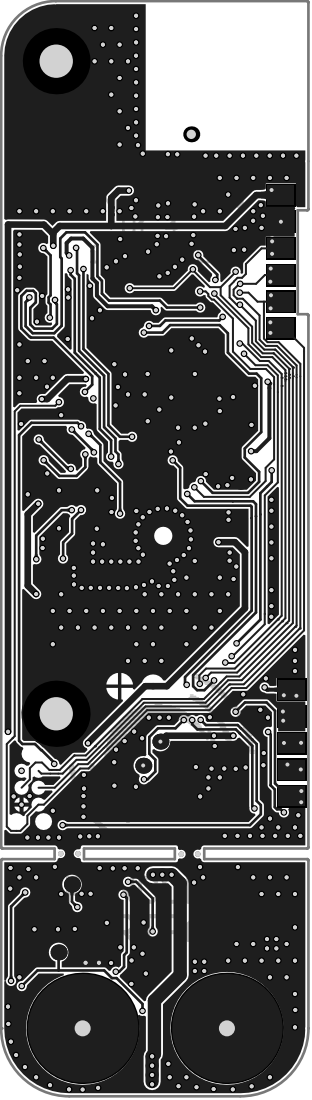
[picture p101: page 1]

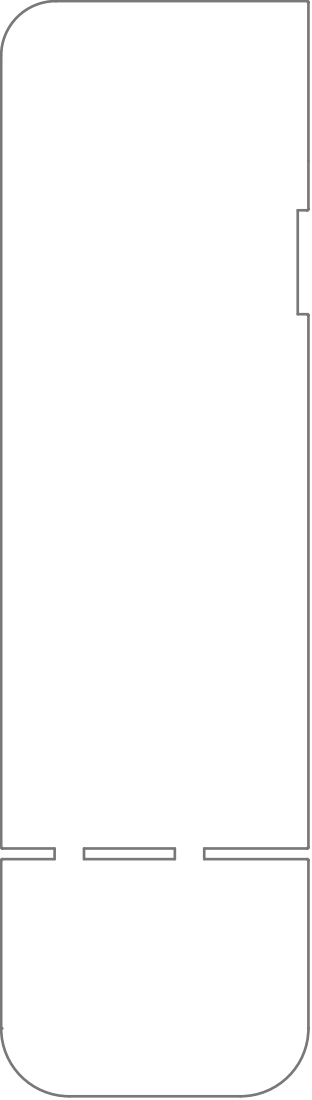
[picture p102: page 2]

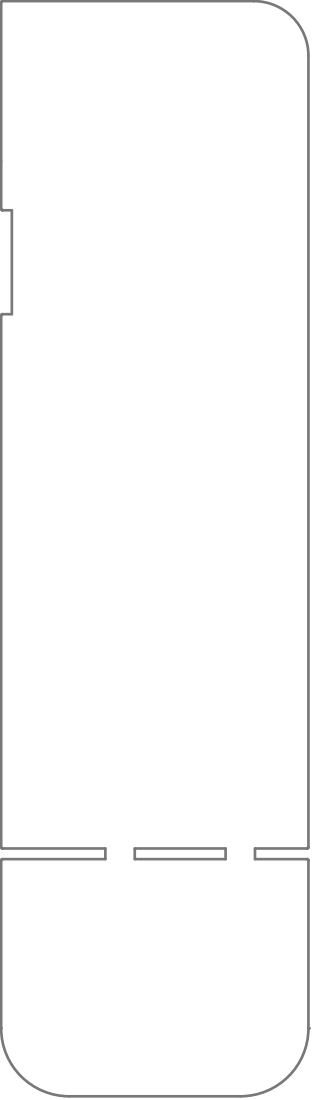
[picture p103: page 3]

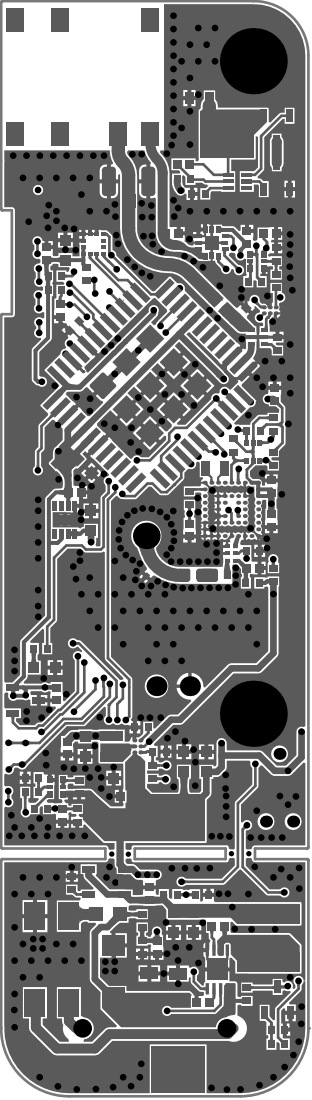
[picture p104: page 4]

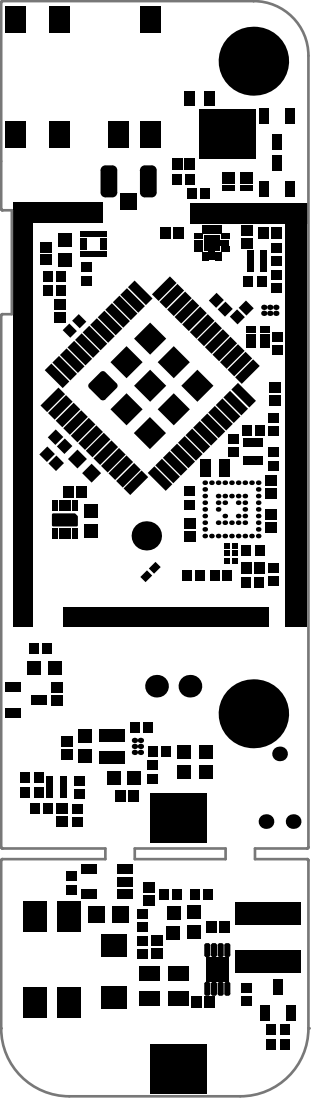
[picture p105: page 5]

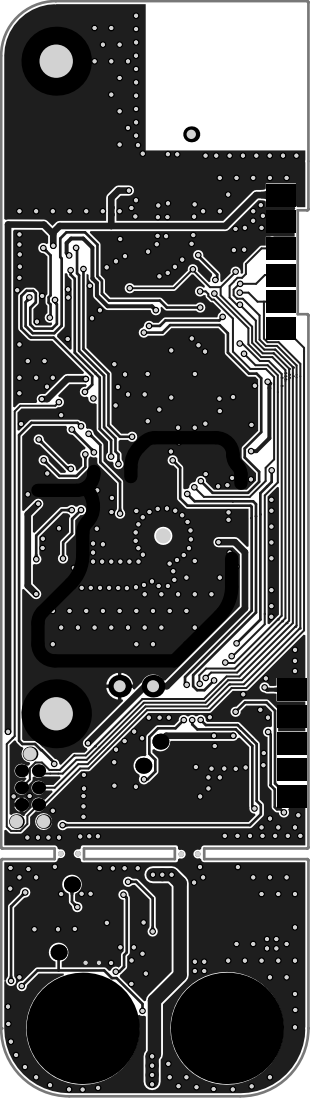
[picture p106: page 6]

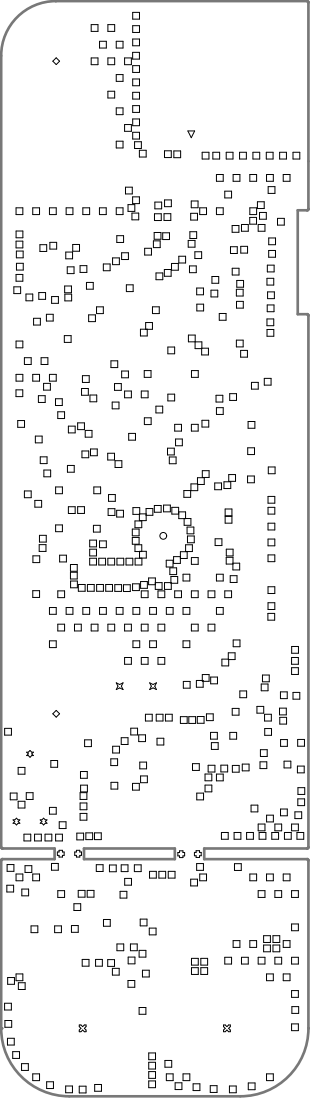
[picture p107: page 7]

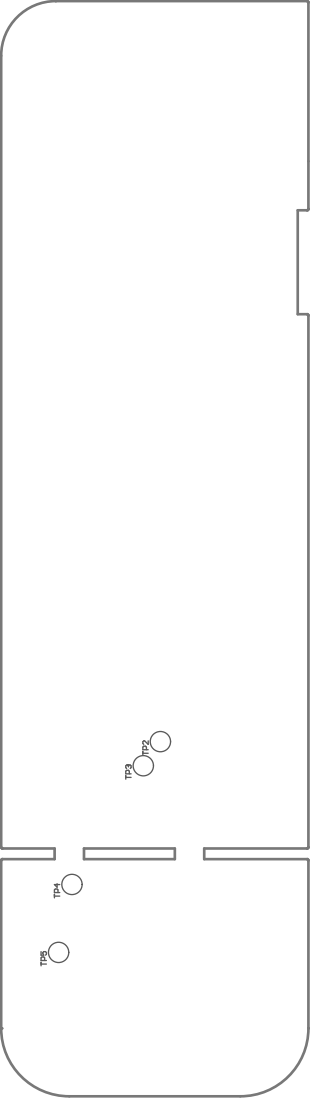
[picture p108: page 8]
