IRNAS/smartparks-lion-tracker-hardware/LION/06_RELEASE/V0/Lion tracker_V0_Assembly/Lion tracker_V0_Assembly.PDF

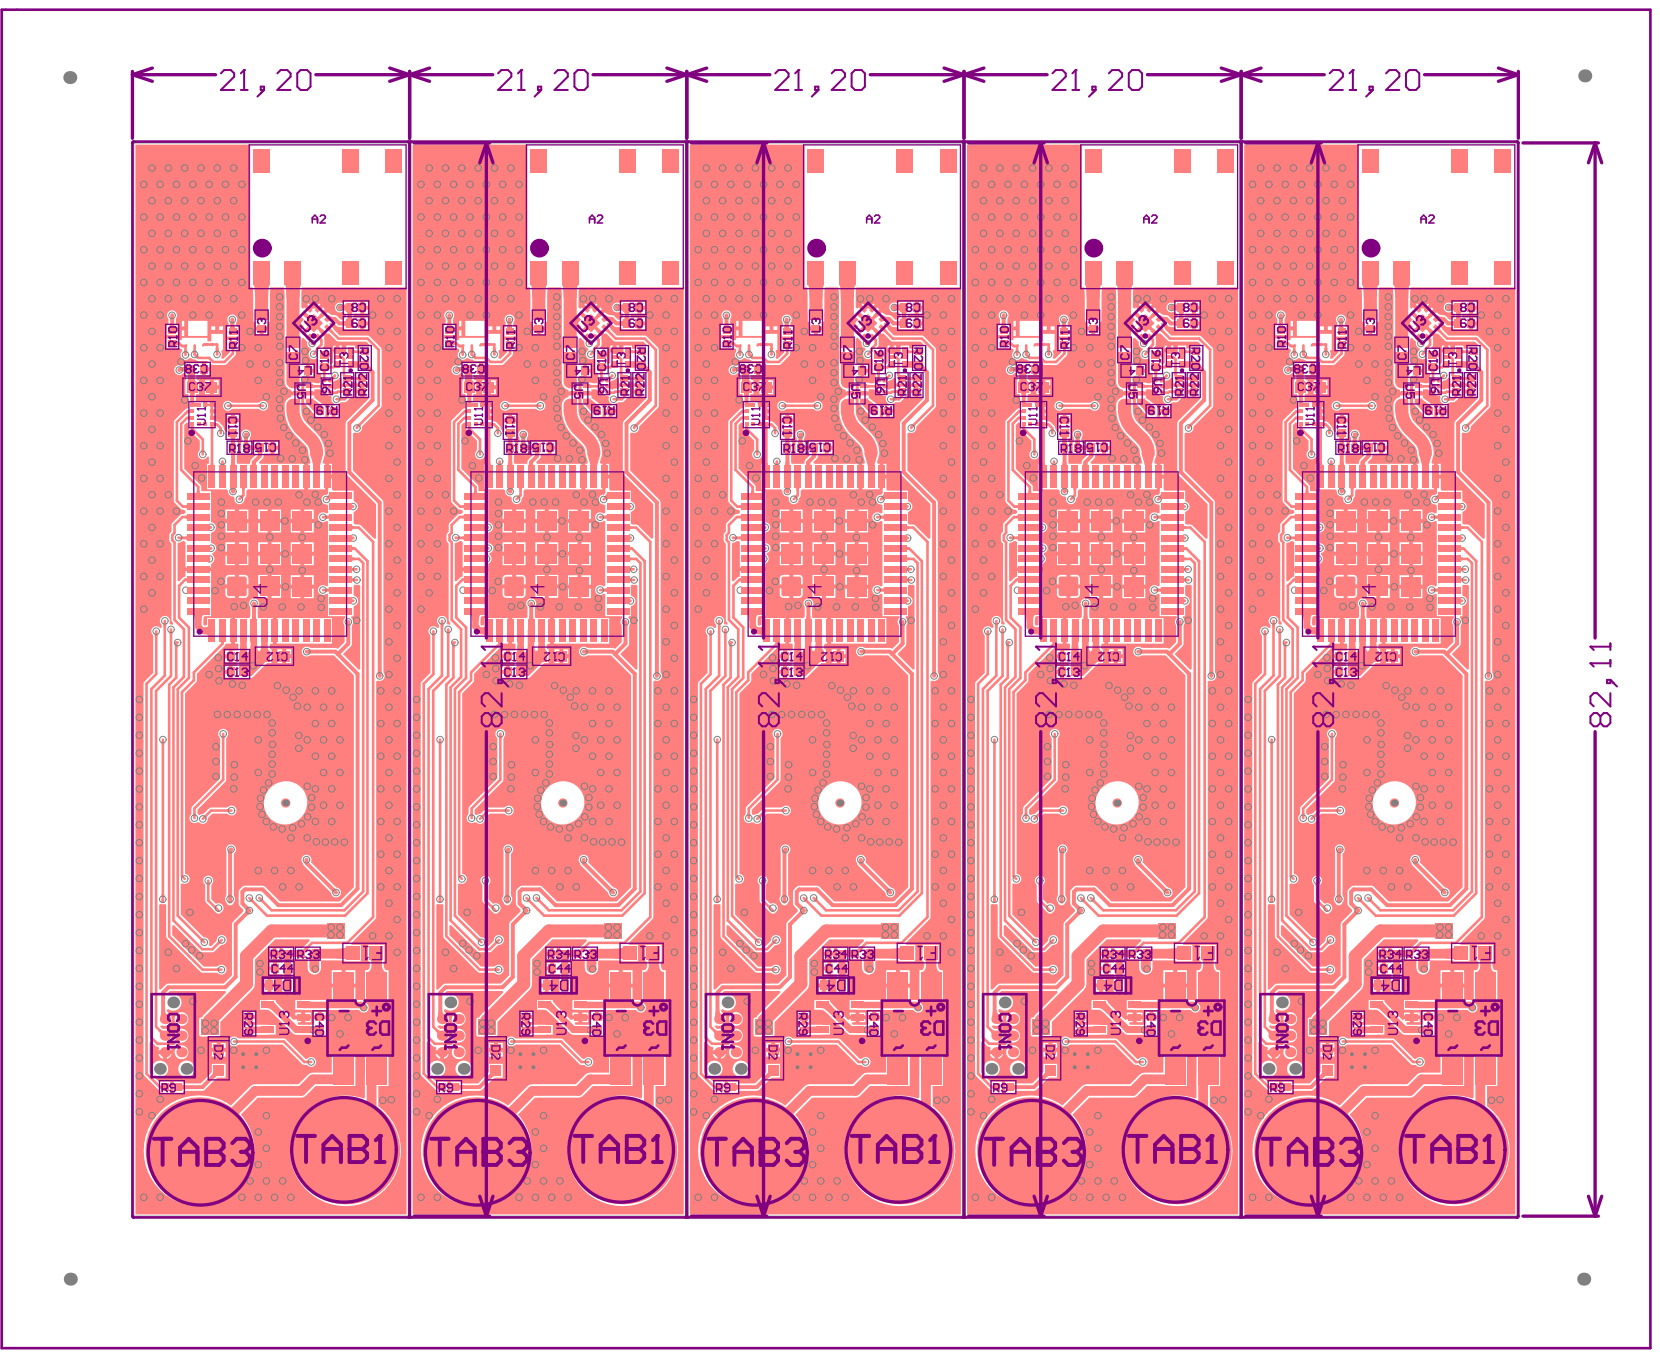
[picture p109: page 1]

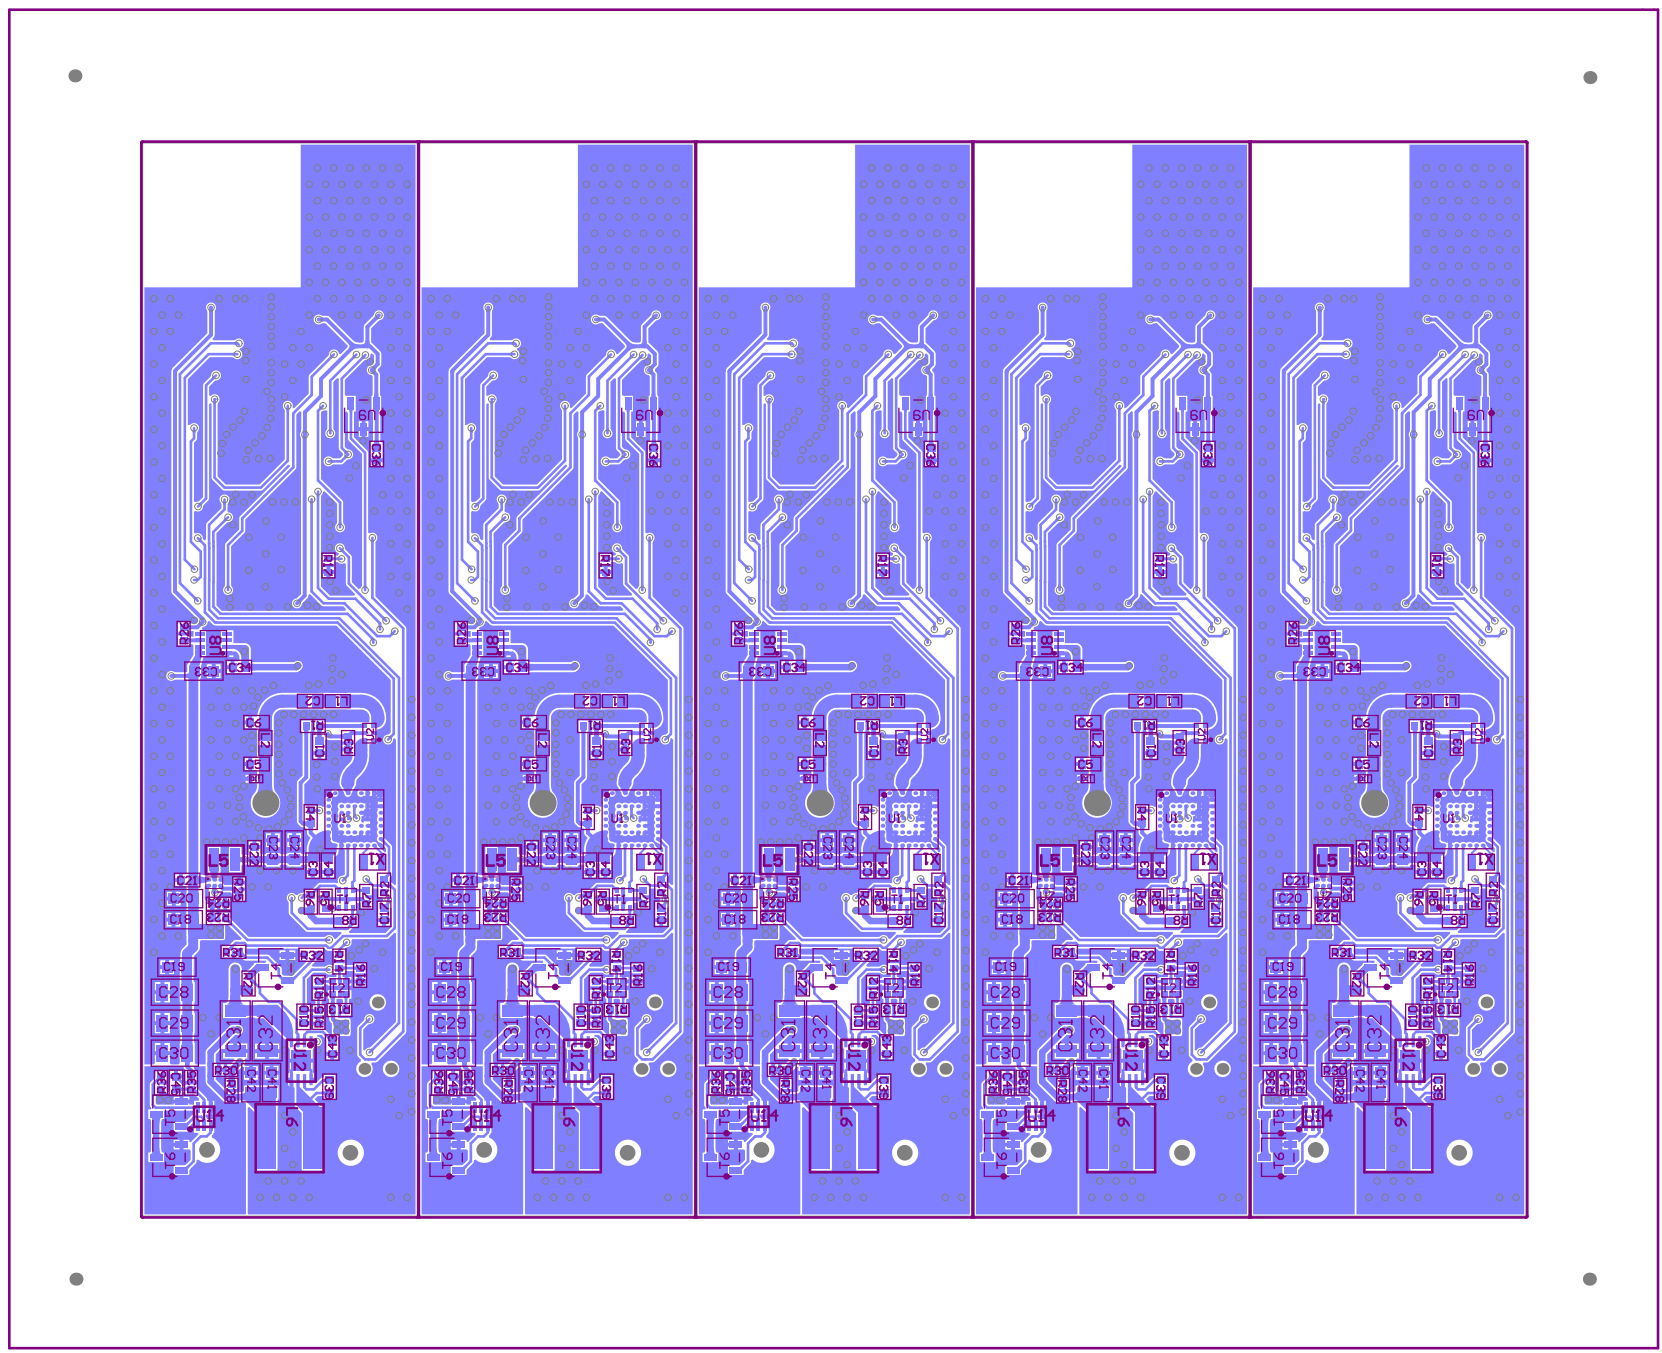
[picture p110: page 2]
