IRNAS/smartparks-lion-tracker-hardware/LION/06_RELEASE/V0/Lion tracker_V0_PCB_Print/Lion tracker_V0_PCB_Print.PDF

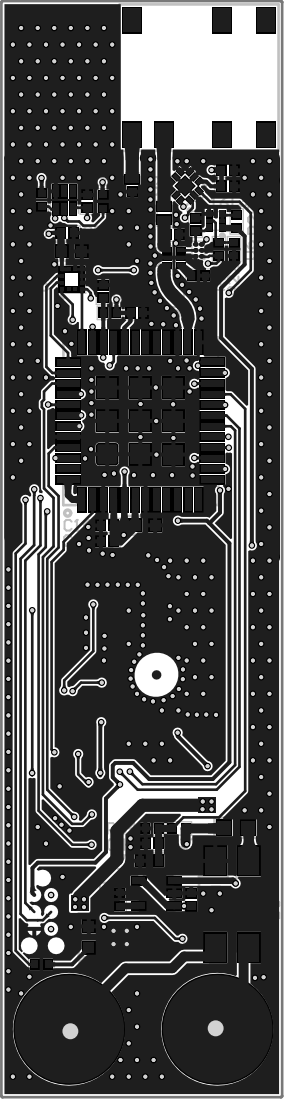
[picture p111: page 1]

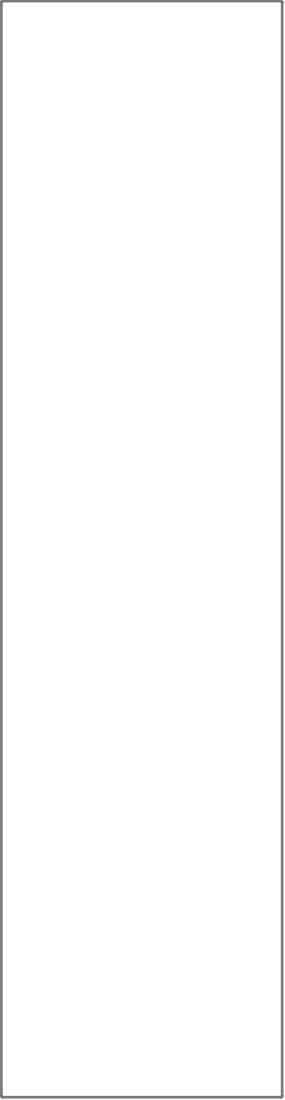
[picture p112: page 2]

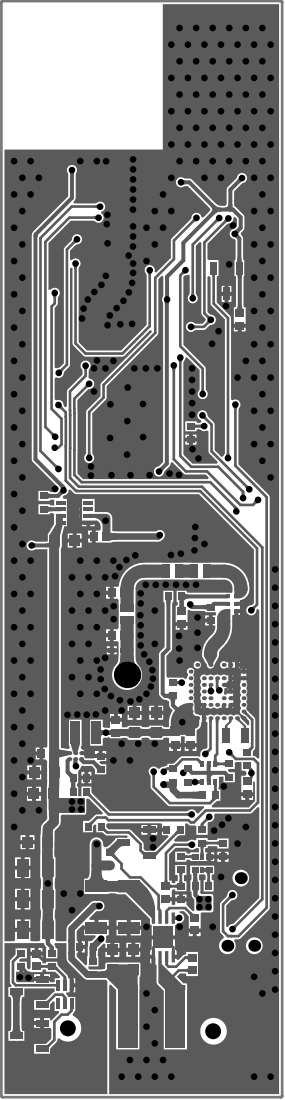
[picture p113: page 4]

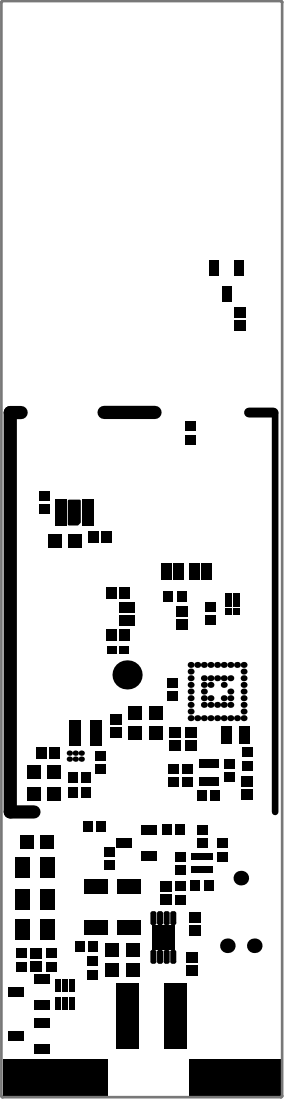
[picture p114: page 5]

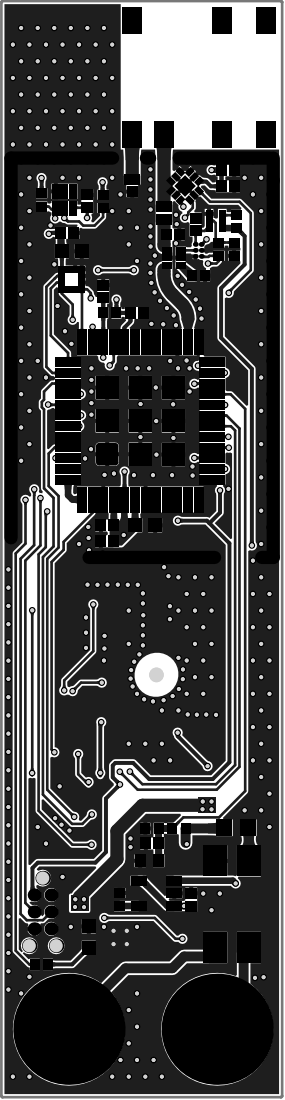
[picture p115: page 6]

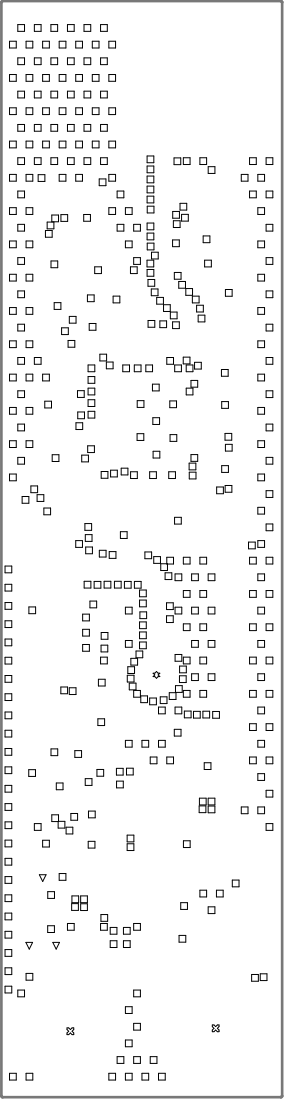
[picture p116: page 7]
