IRNAS/smartparks-lion-tracker-hardware/LION/06_RELEASE/V1.1/Lion_Tracker_V1.1_Assembly/Lion_Tracker_V1.1_Assembly.PDF

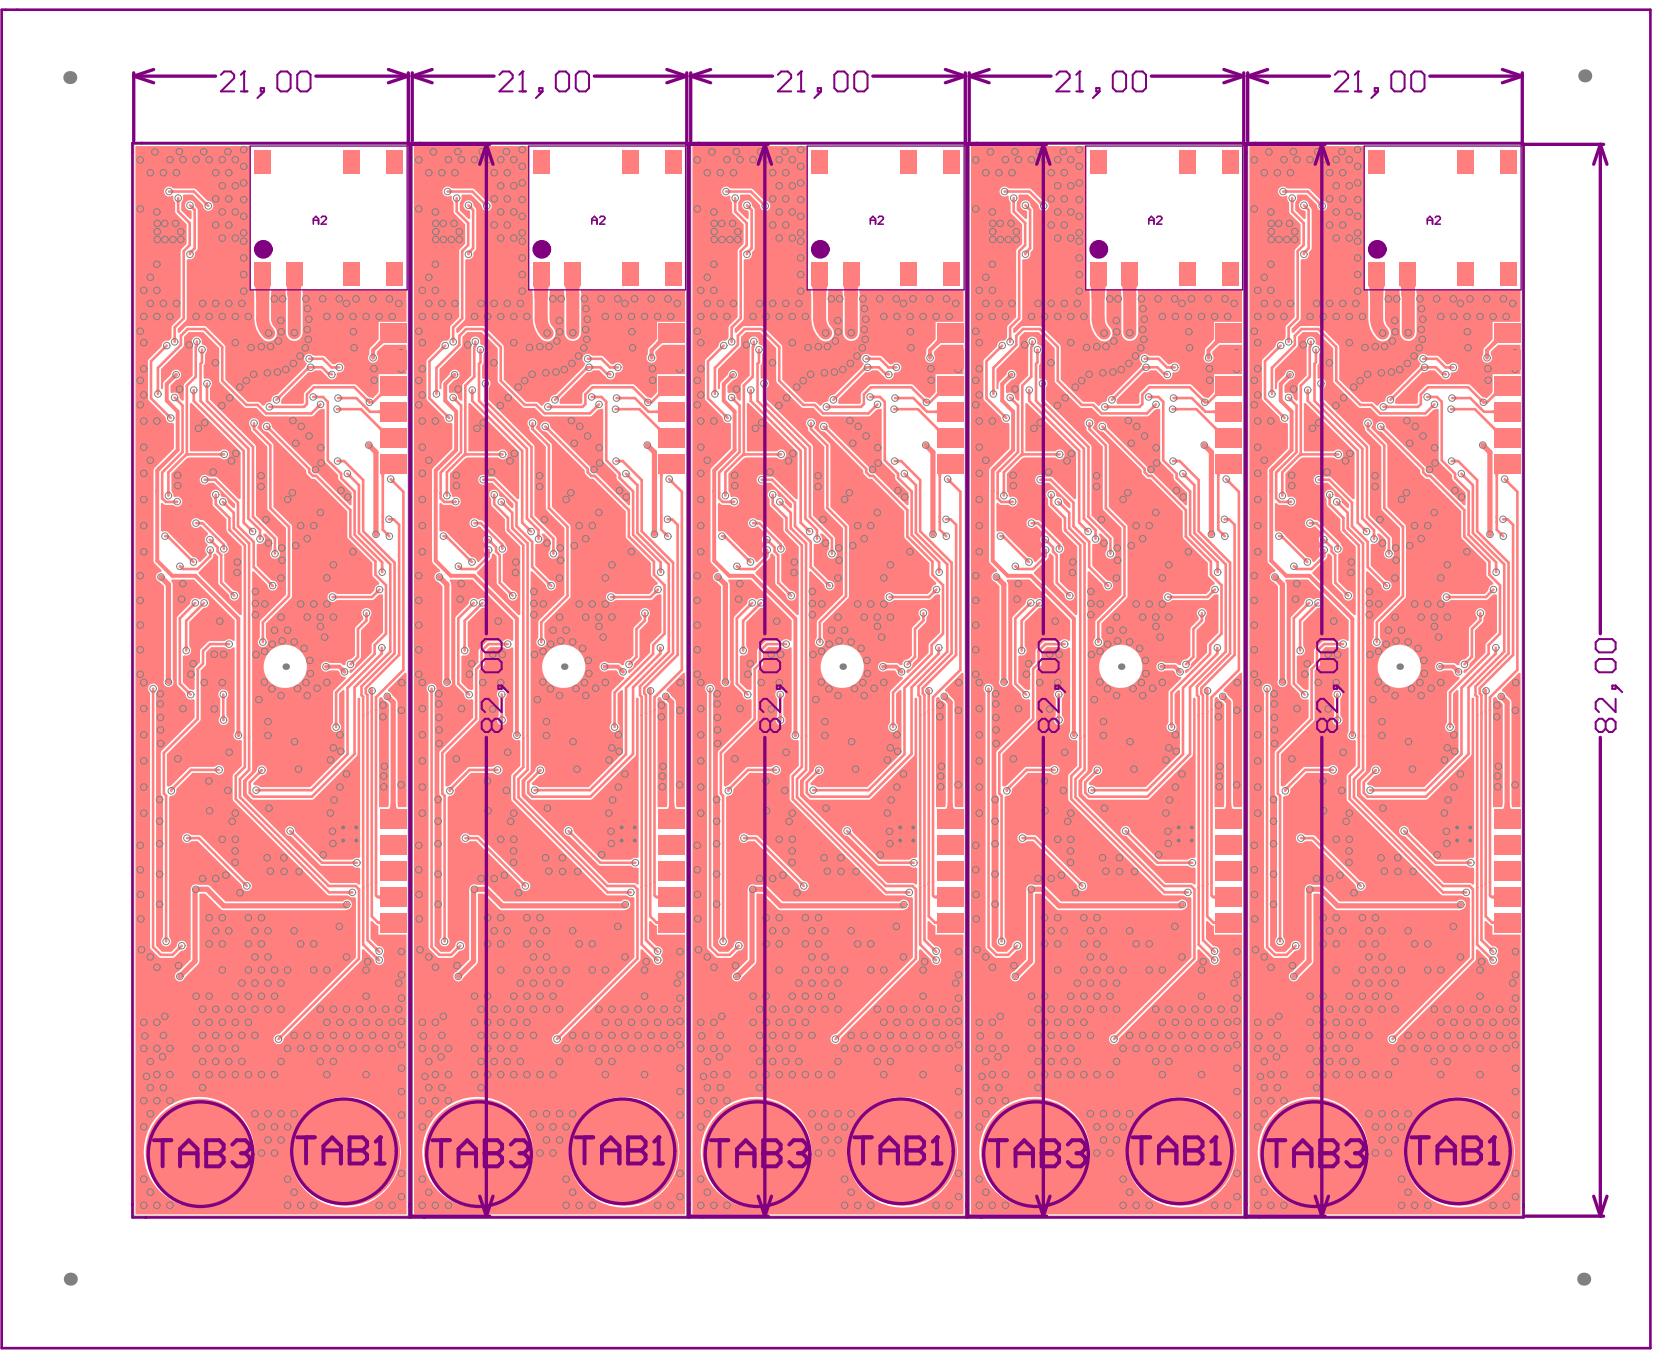
[picture p117: page 1]

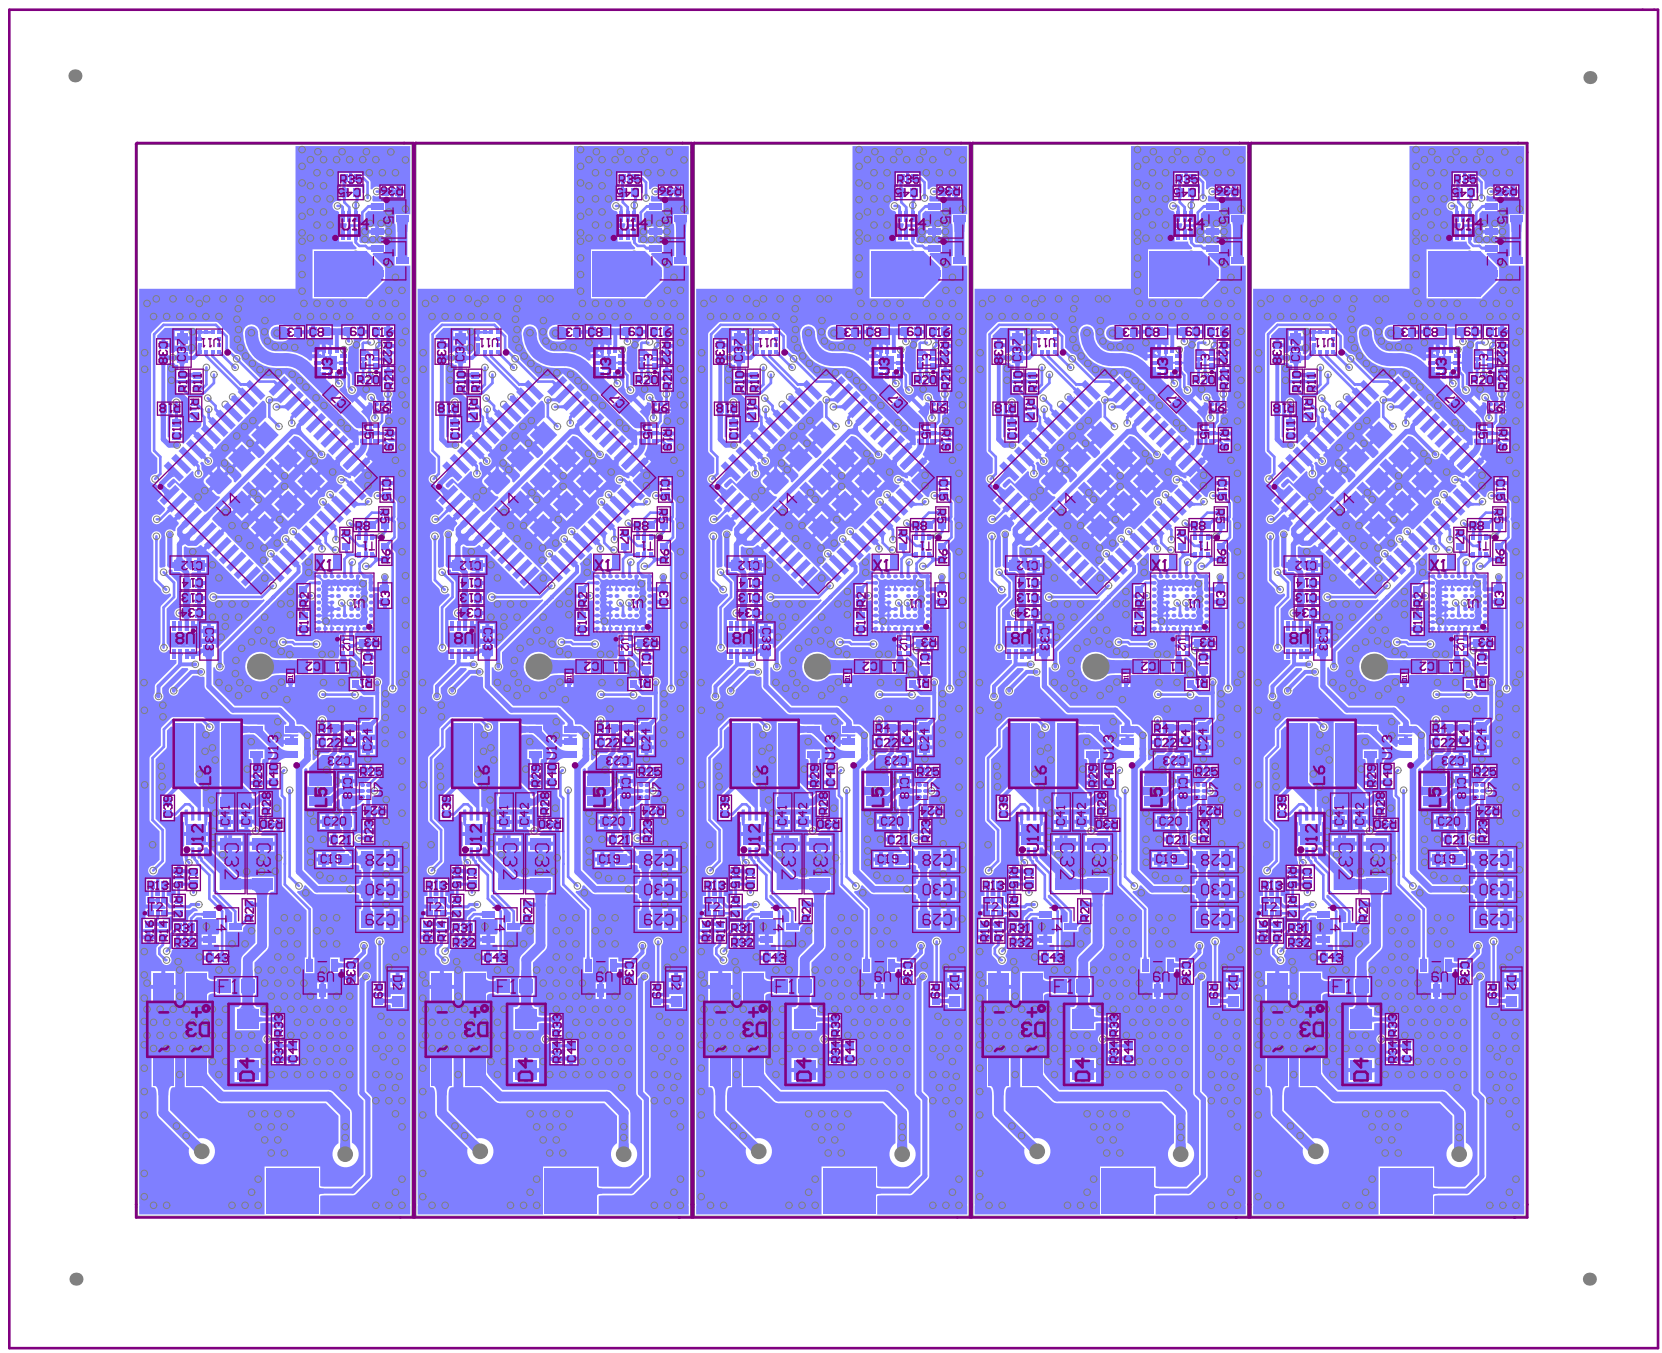
[picture p118: page 2]
