IRNAS/smartparks-lion-tracker-hardware/LION/06_RELEASE/V1.1/Lion_Tracker_V1.1_PCB_Print/Lion_Tracker_V1.1_PCB_Print.PDF

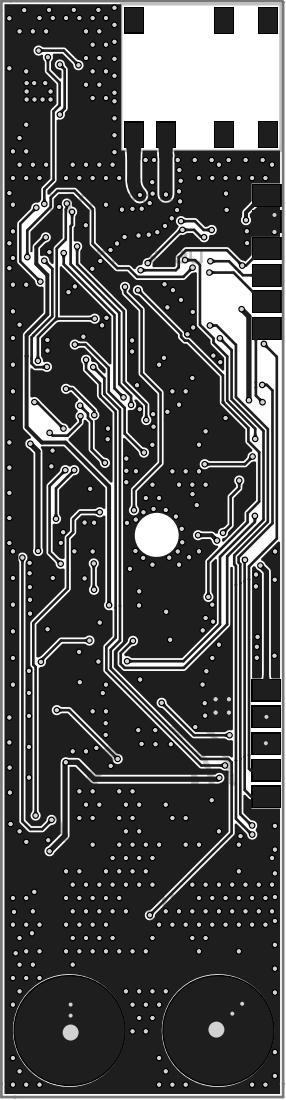
[picture p119: page 1]

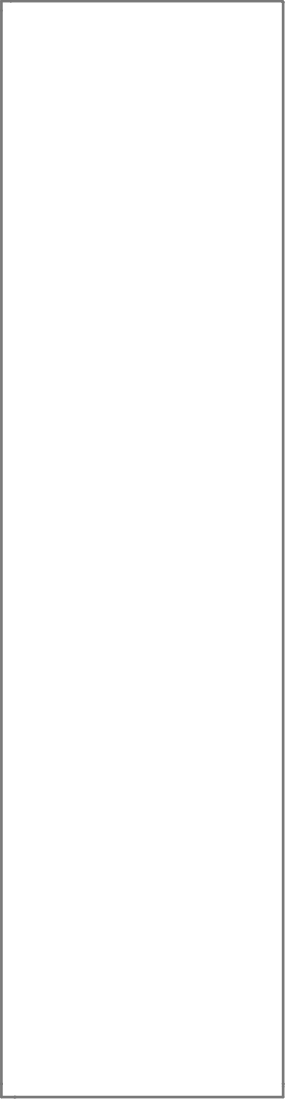
[picture p120: page 2]

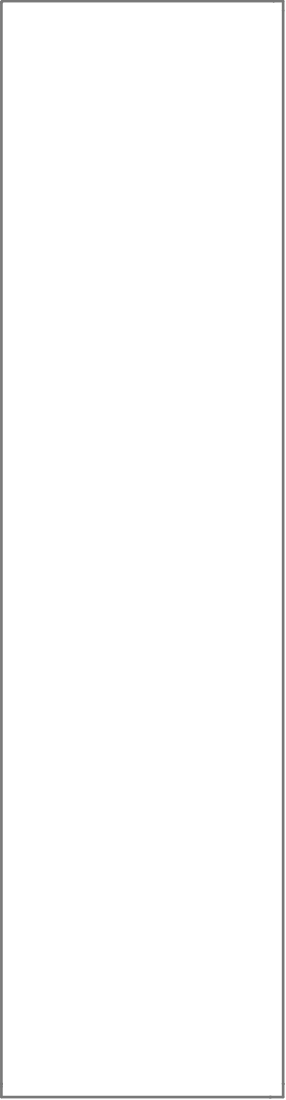
[picture p121: page 3]

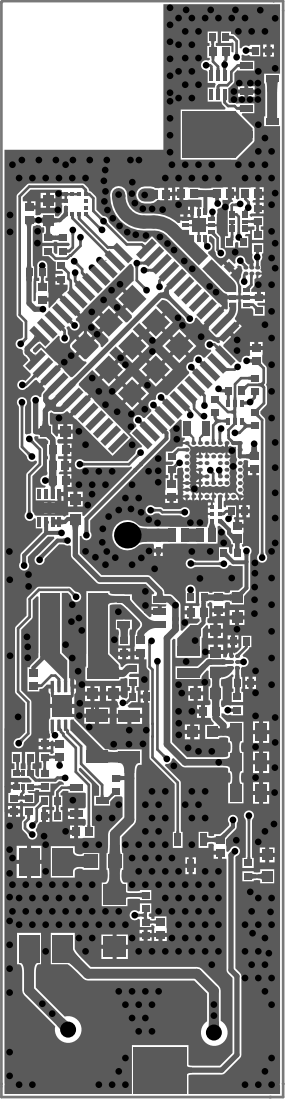
[picture p122: page 4]

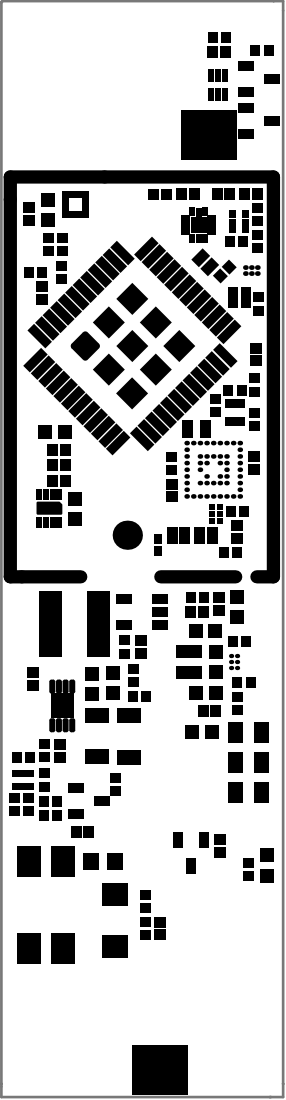
[picture p123: page 5]

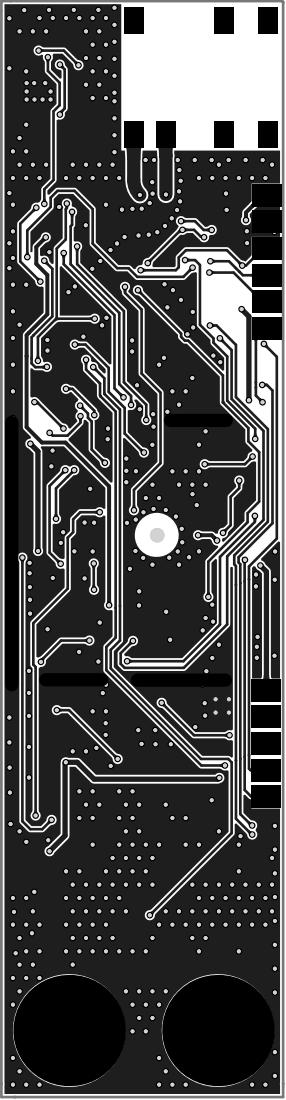
[picture p124: page 6]

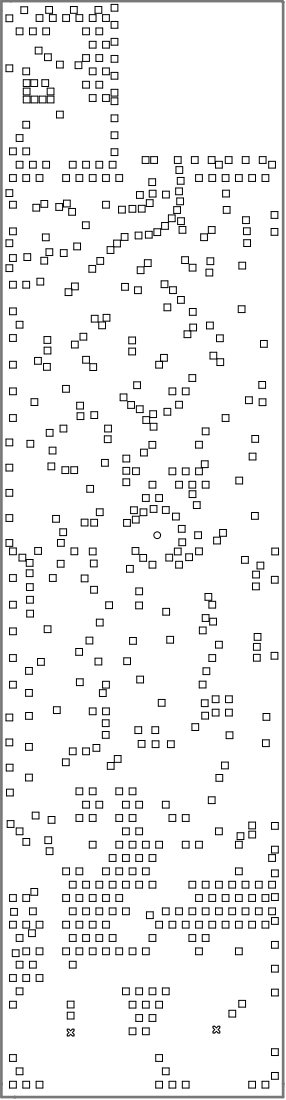
[picture p125: page 7]
