IRNAS/smartparks-lion-tracker-hardware/LION/06_RELEASE/V1.2/Lion_Tracker_V1.2_Assembly/Lion_Tracker_V1.2_Assembly.PDF

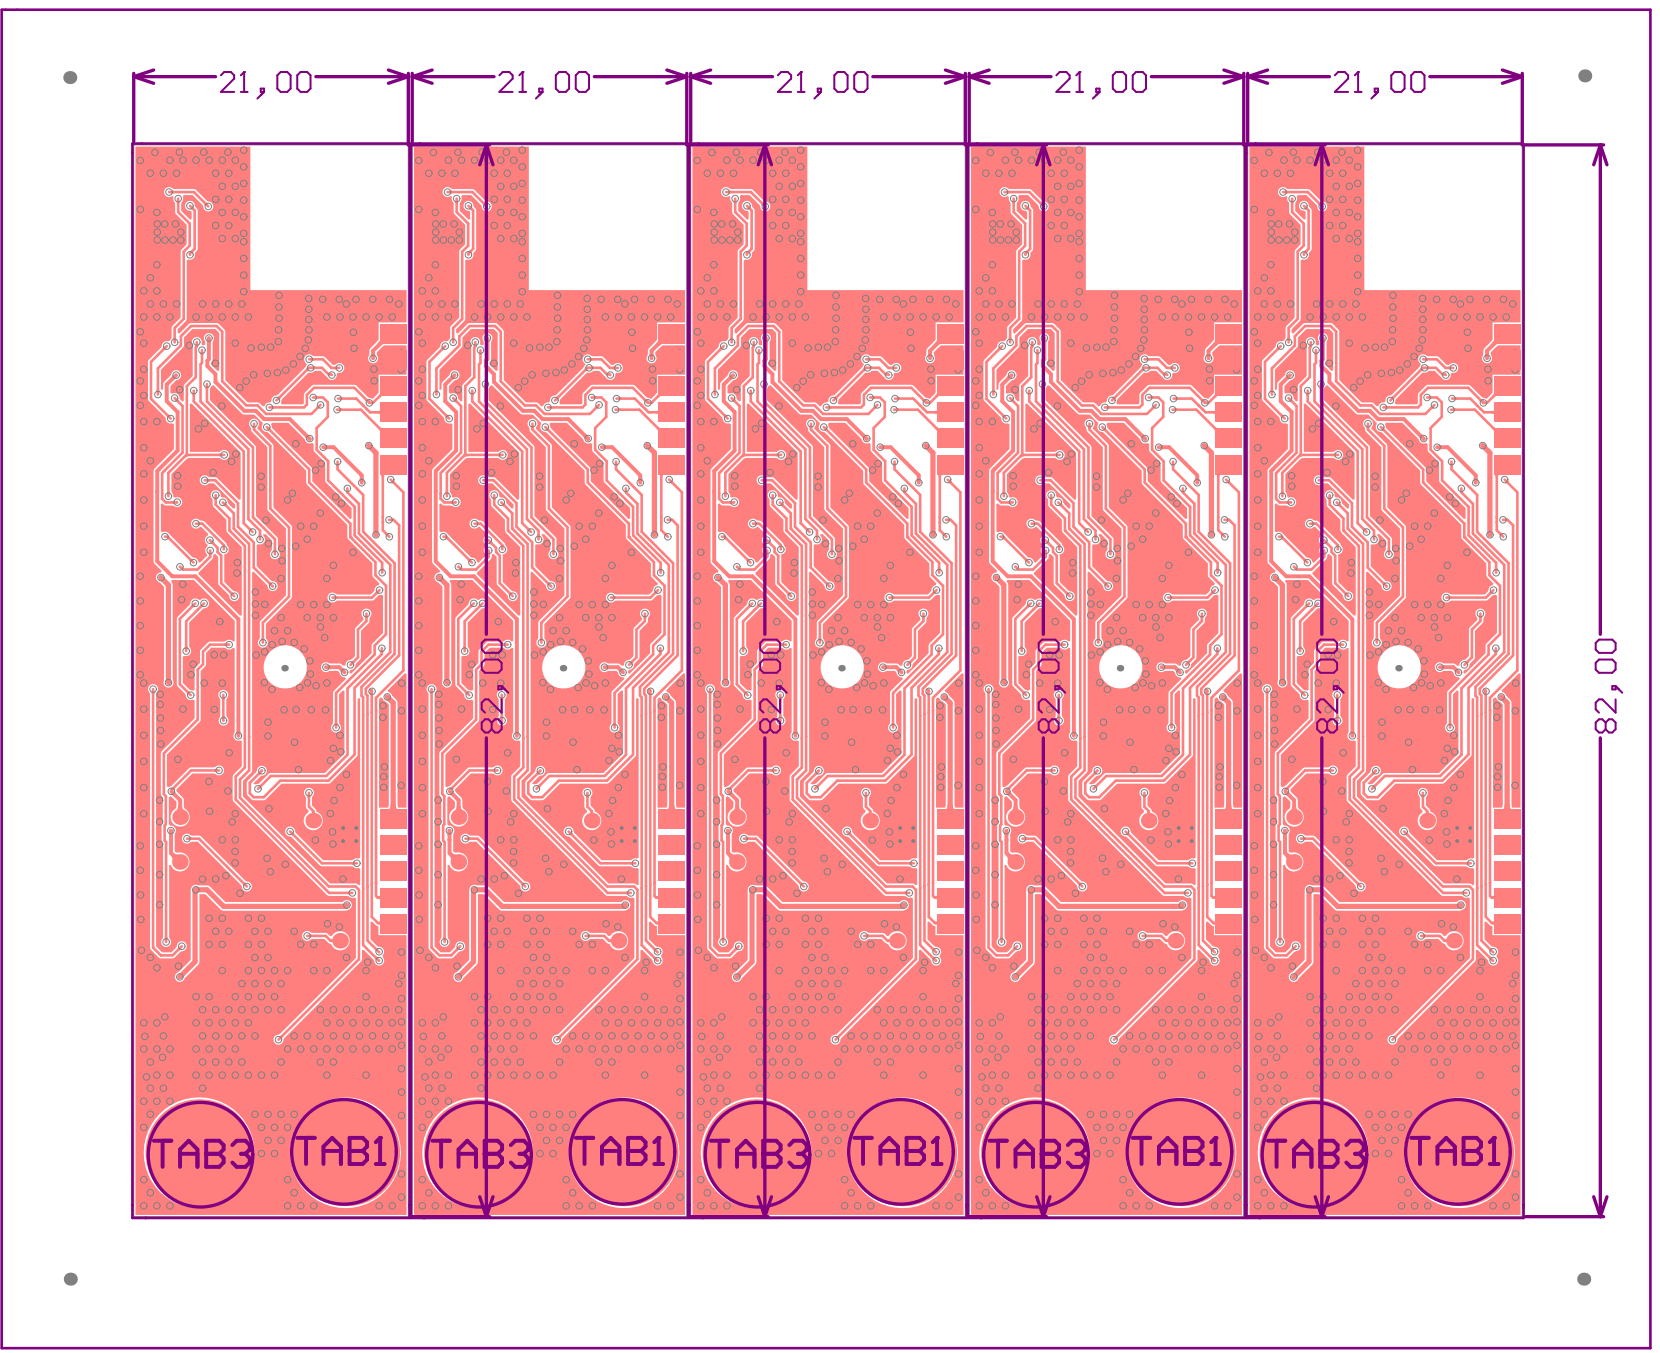
[picture p126: page 1]

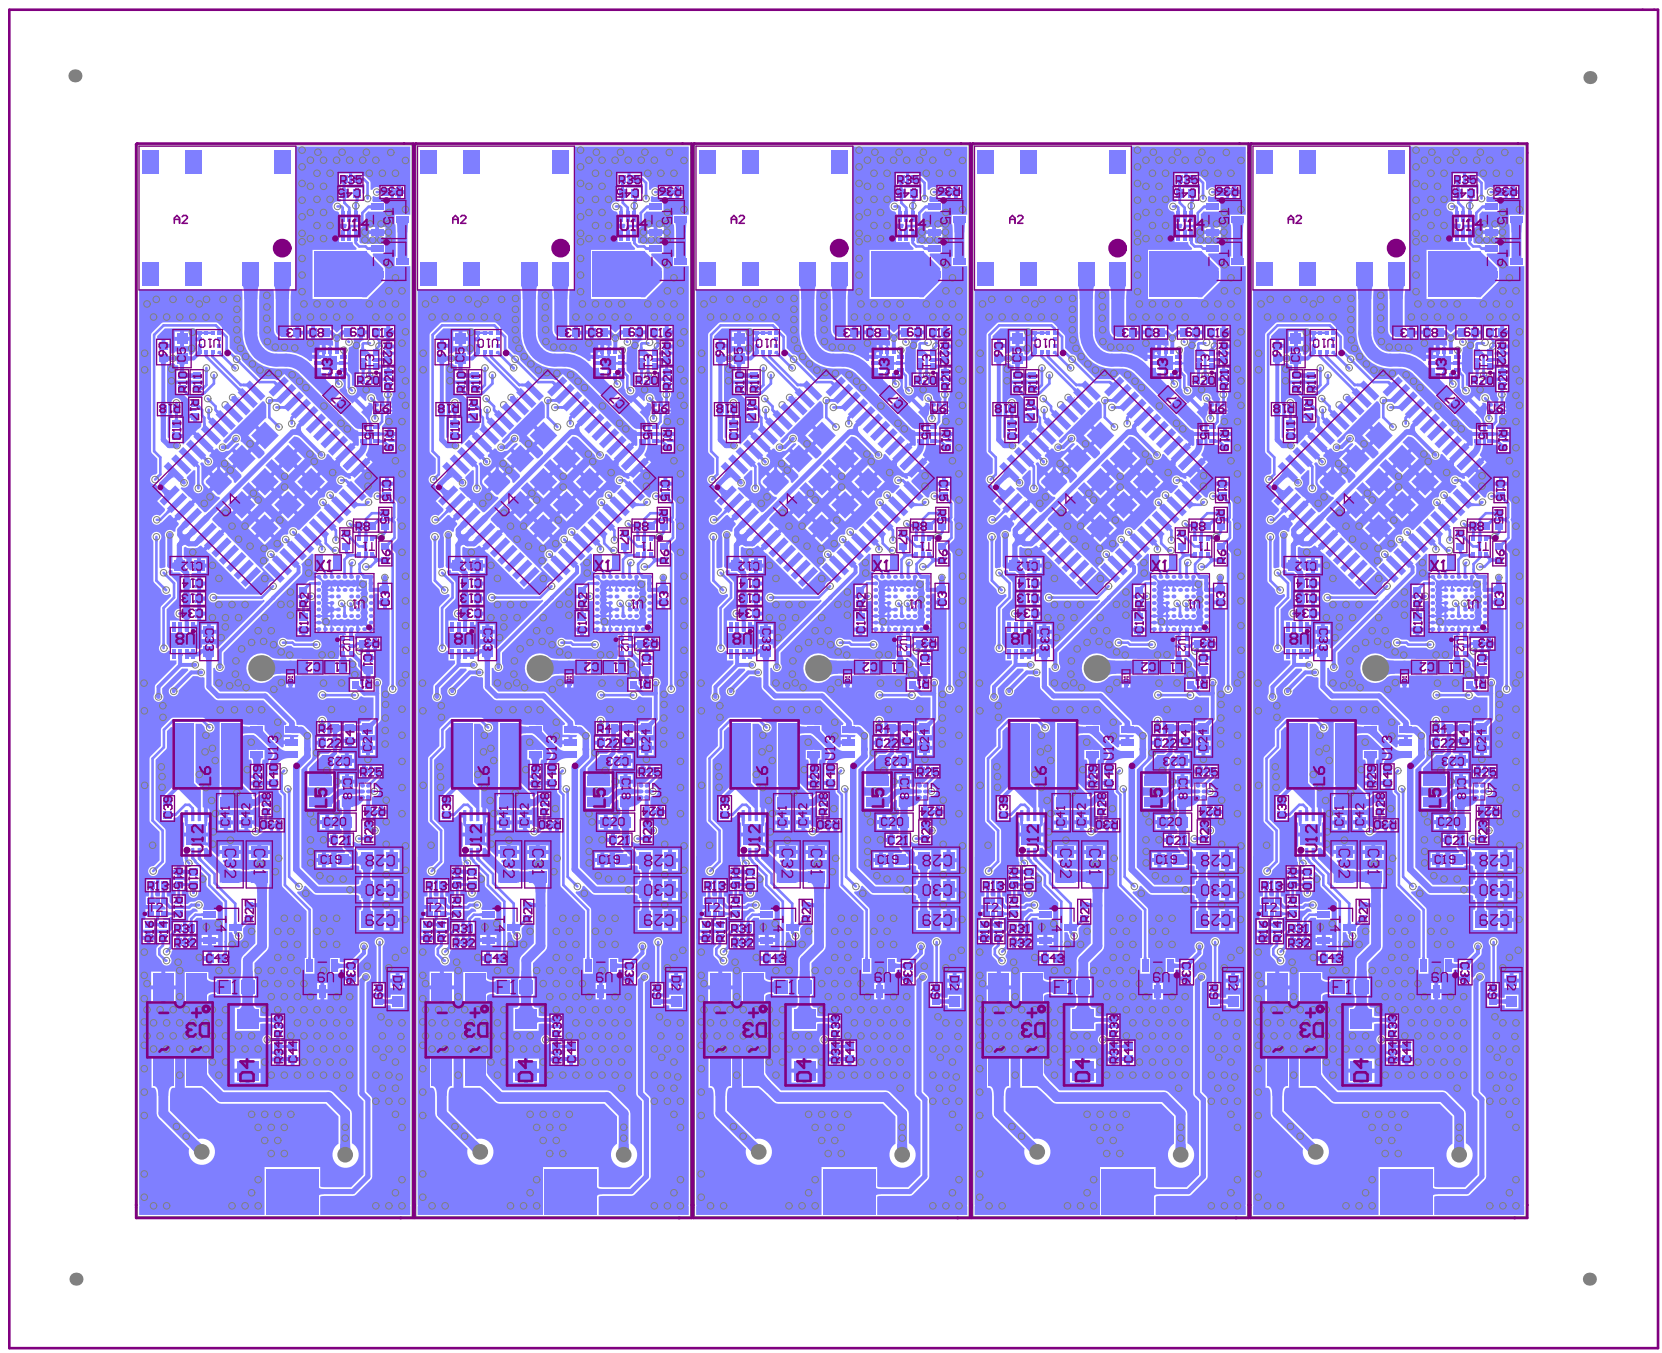
[picture p127: page 2]
