IRNAS/smartparks-lion-tracker-hardware/LION/06_RELEASE/V1.2/Lion_Tracker_V1.2_PCB_Print/Lion_Tracker_V1.2_PCB_Print.PDF

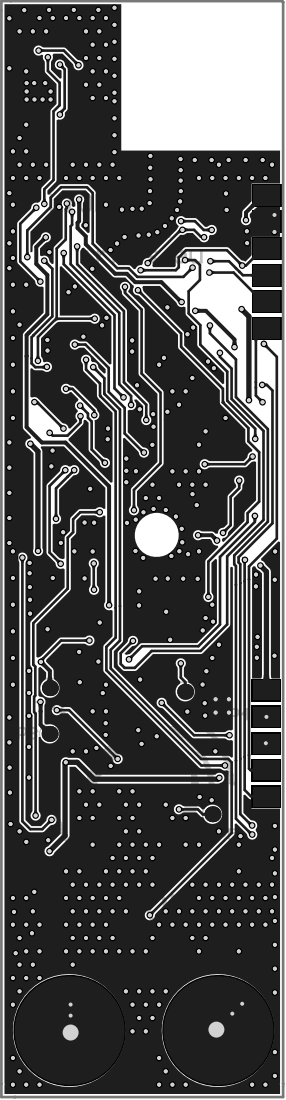
[picture p128: page 1]



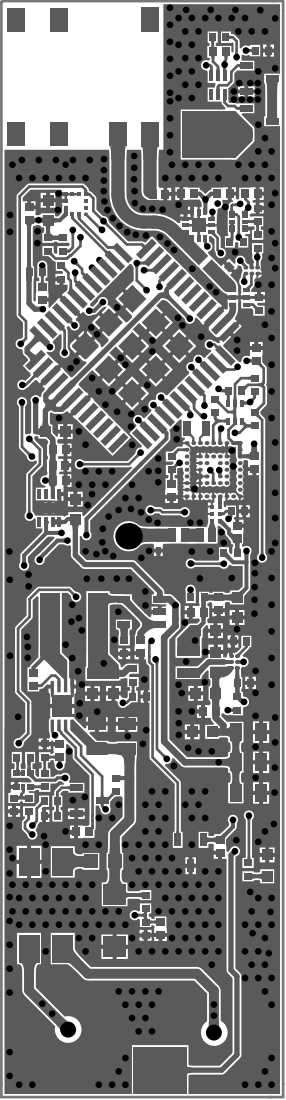
[picture p129: page 4]

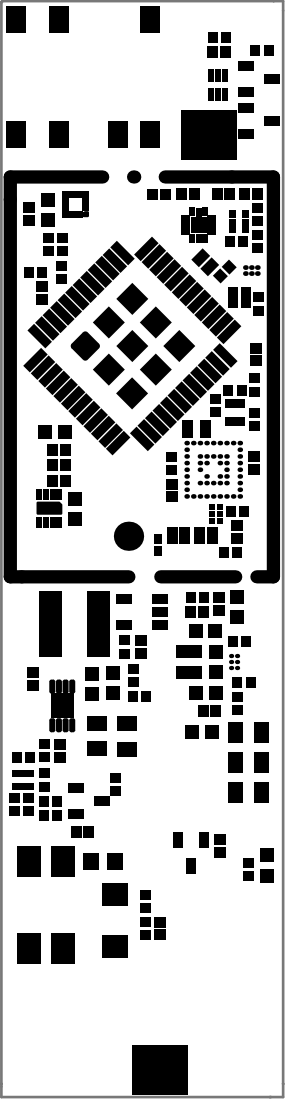
[picture p130: page 5]

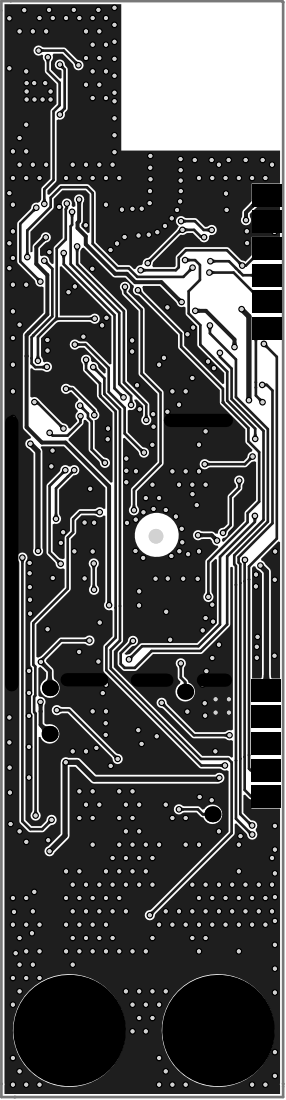
[picture p131: page 6]

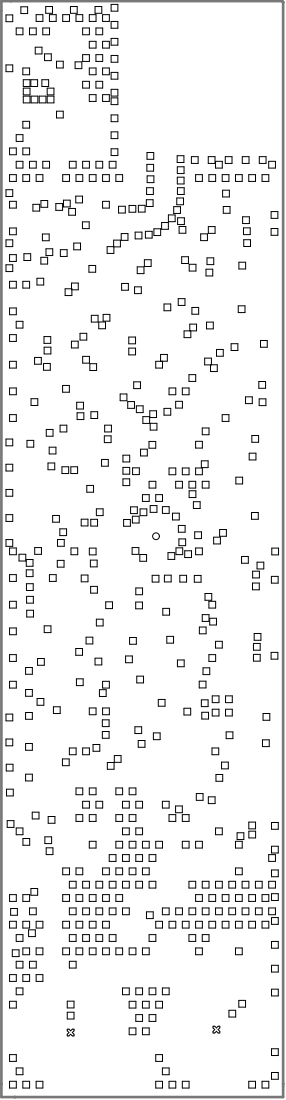
[picture p132: page 7]

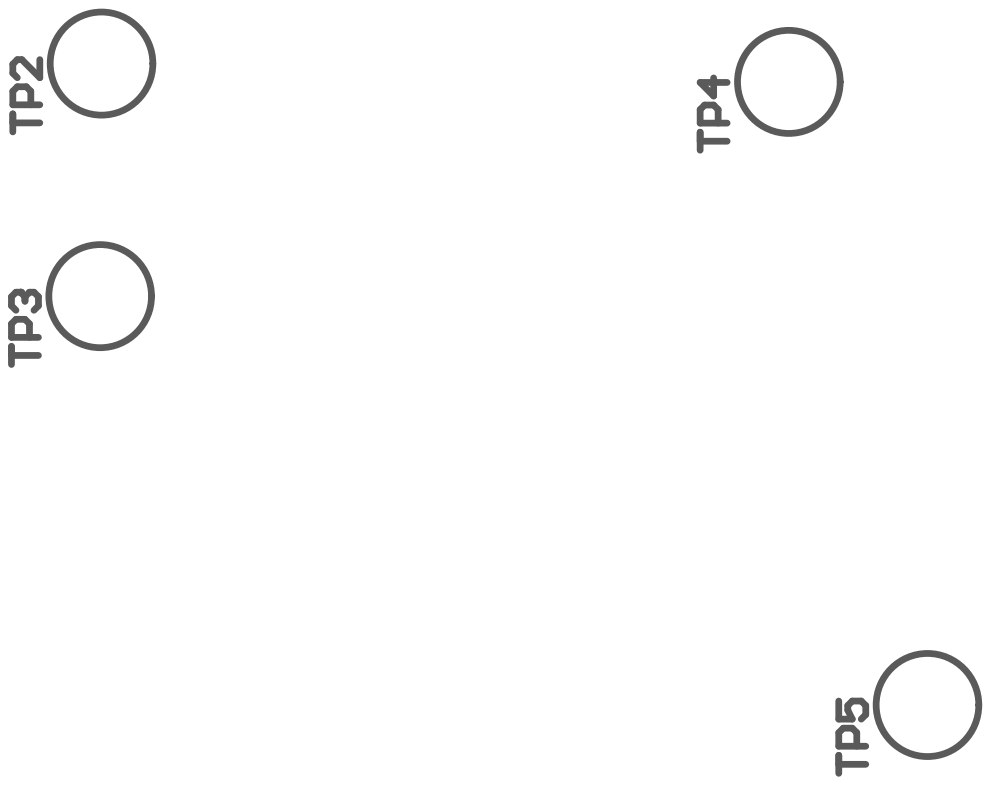
[picture p133: page 8]
