IRNAS/smartparks-lion-tracker-hardware/LION/06_RELEASE/V1.3/Lion_Tracker_V1.3_Assembly/Lion_Tracker_V1.3_Assembly.PDF

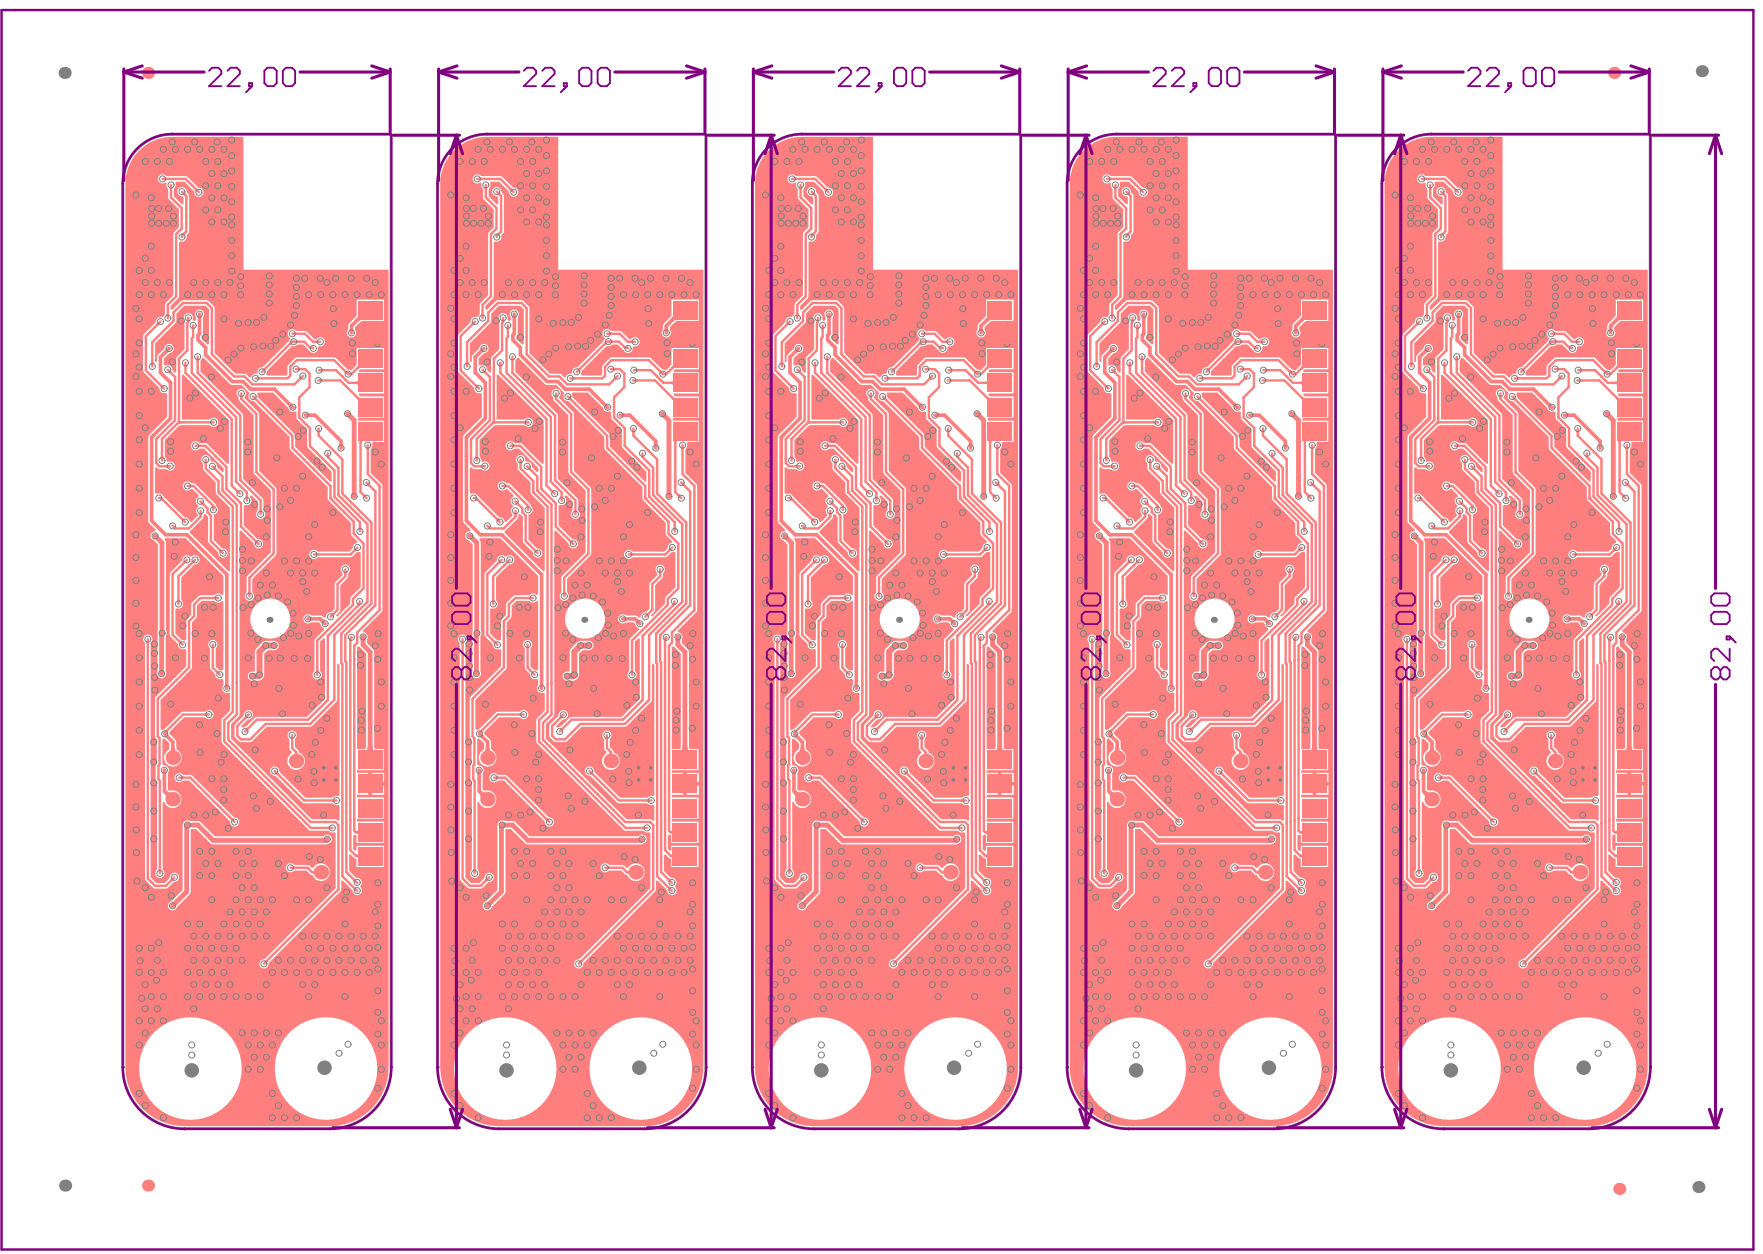
[picture p134: page 1]

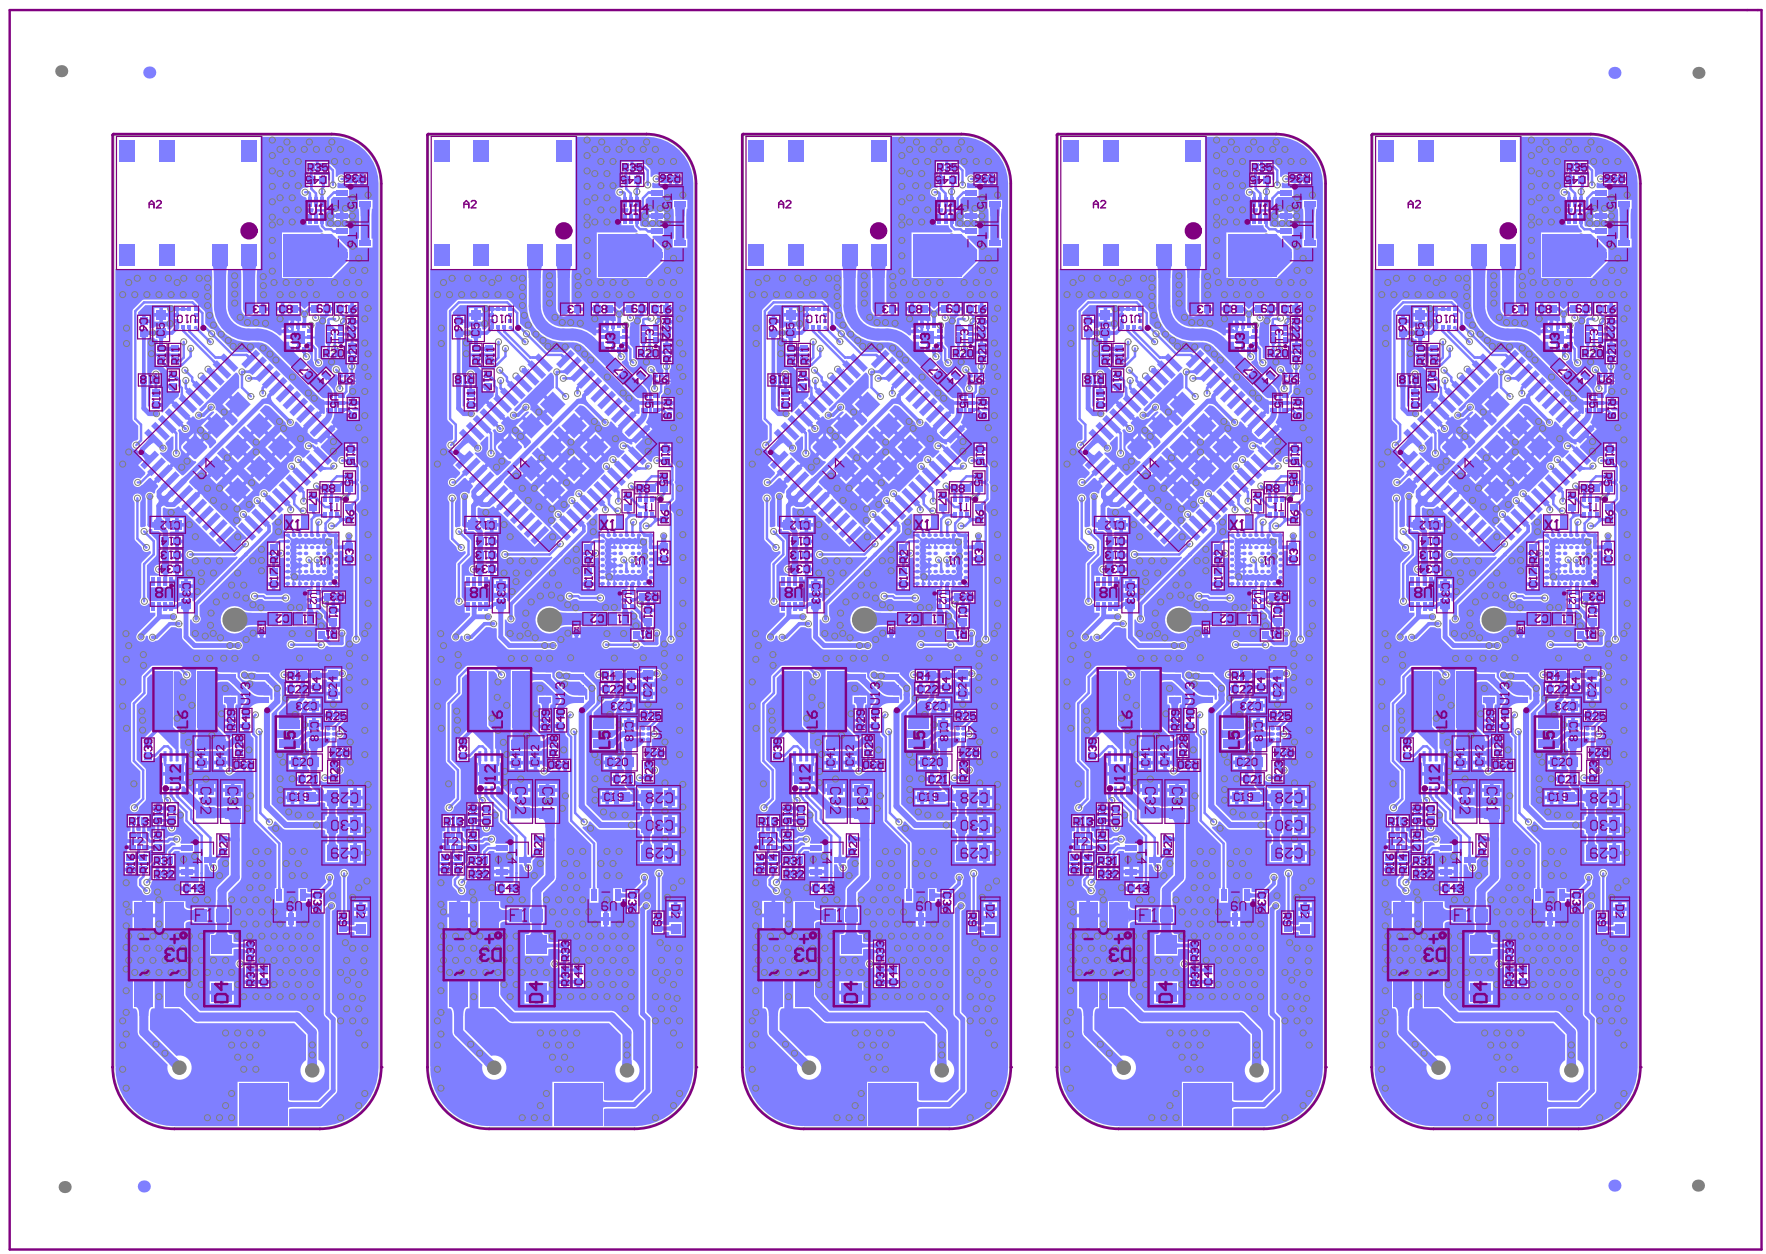
[picture p135: page 2]
