IRNAS/smartparks-lion-tracker-hardware/LION/06_RELEASE/V1.3/Lion_Tracker_V1.3_PCB_Print/Lion_Tracker_V1.3_PCB_Print.PDF

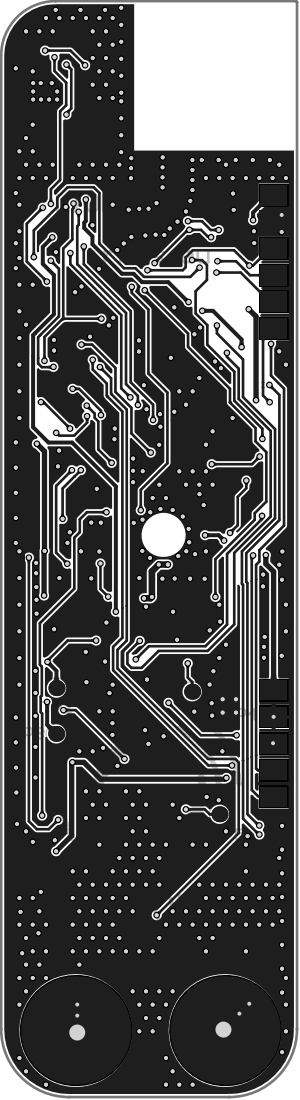
[picture p136: page 1]

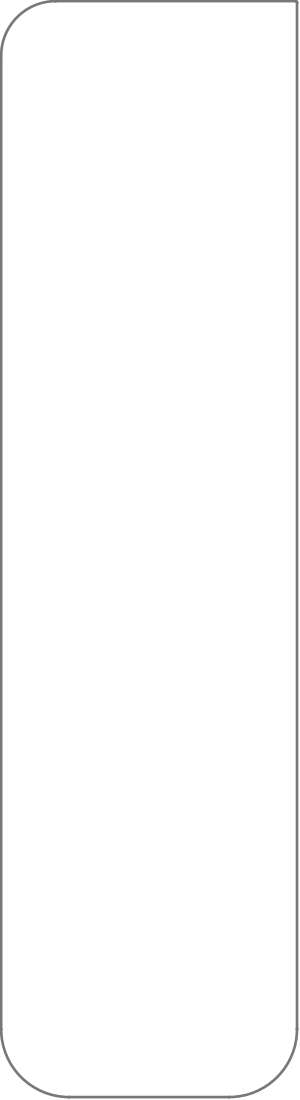
[picture p137: page 2]

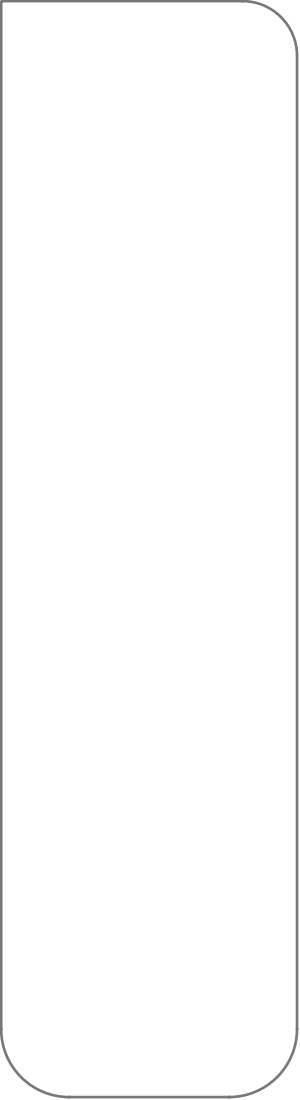
[picture p138: page 3]

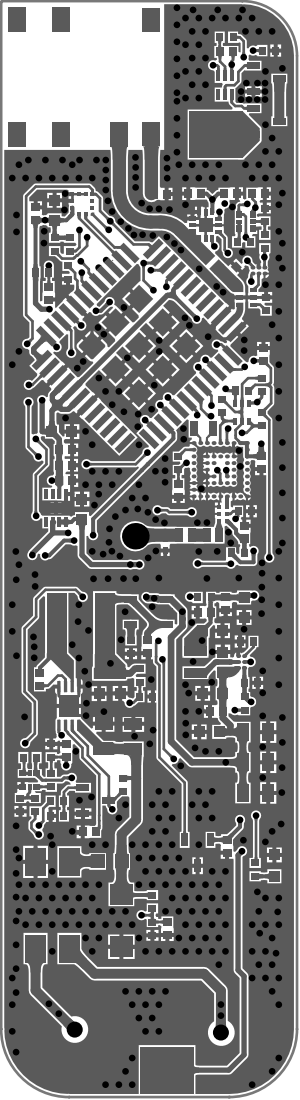
[picture p139: page 4]

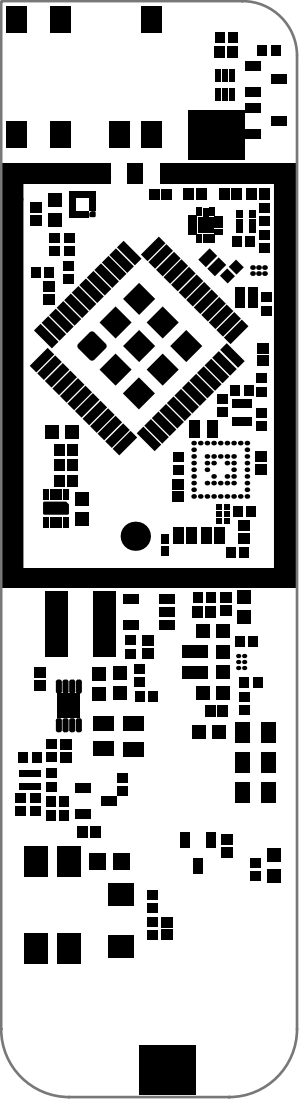
[picture p140: page 5]

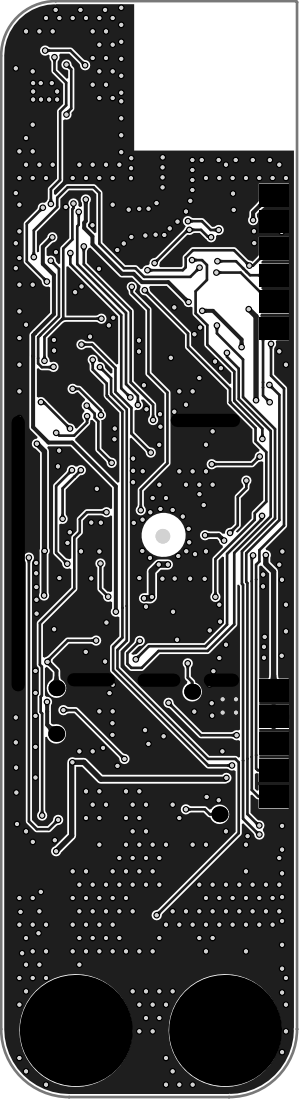
[picture p141: page 6]

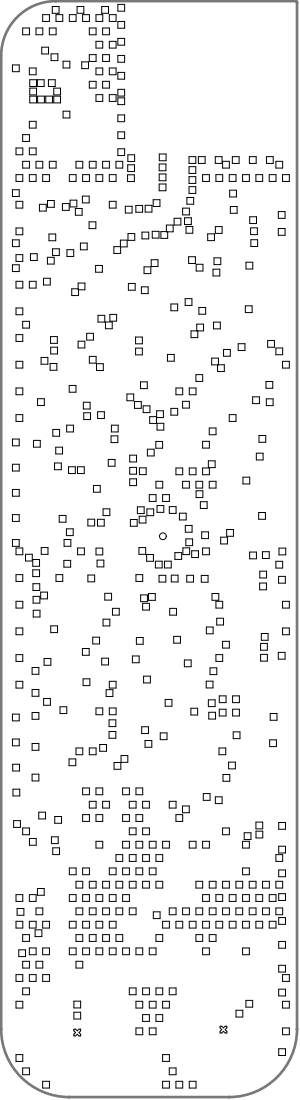
[picture p142: page 7]

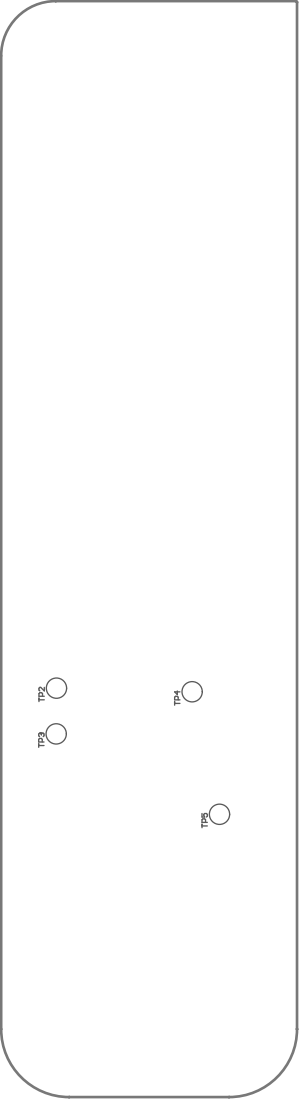
[picture p143: page 8]
